DavidSPuentesc/SmartSense-Monitoring/tesis/capitulos/07-desarrollo-implementacion.tex

\chapter{Desarrollo e implementación}
\label{cap:implementacion}

\section{Arquitectura y responsabilidades}
La implementación distribuye la adquisición entre \NumeroNodos{} nodos y concentra recepción, persistencia y consulta en un gateway. La cadena funcional es PT100 $\rightarrow$ MAX31865 $\rightarrow$ ESP32-C6 $\rightarrow$ E220 $\rightarrow$ gateway $\rightarrow$ microSD/LittleFS $\rightarrow$ pantalla/dashboard. El gateway también actualiza la lectura reciente de la interfaz al recibir datos: la pantalla no necesita volver a leer el histórico para cada actualización. La figura~\ref{fig:impl-arquitectura} muestra la separación entre adquisición, enlace radio y acceso local.

\begin{figure}[htbp]
\centering

\caption[Arquitectura de adquisición y consulta local.]{Arquitectura de adquisición y consulta local. Los tres nodos comparten el gateway, que identifica las tramas, conserva series por sensor y presenta lecturas por pantalla y Wi-Fi. Fuente: diseño del proyecto.}
\label{fig:impl-arquitectura}
\end{figure}

El enlace entre nodos y gateway es LoRa punto a punto con mensajes propios, no una red LoRaWAN. El Wi-Fi conecta el navegador con el gateway y nada más. Así se consultan los datos sin Internet, mientras el gateway tenga alimentación, almacenamiento y hora válida.

\section{Construcción del nodo sensor}
\label{sec:impl-nodo}
Cada nodo combina una placa XIAO ESP32-C6, una PT100 magnética de tres hilos, el MAX31865, un E220 y una batería LiPo. La conexión RTD se configura como \texttt{MAX31865\_3WIRE}; el firmware define $R_{\mathrm{nominal}}=\SI{100}{\ohm}$ y $R_{\mathrm{ref}}=\SI{421.1}{\ohm}$. Este último es el valor caracterizado del módulo que usa la conversión (sección~\ref{sec:fund-calculos}).

El MAX31865 se conecta por SPI implementado en software; la alimentación del acondicionador se conmuta desde un pin para reducir su actividad entre lecturas. El E220 se conecta por UART y dispone de líneas de selección de modo. La figura~\ref{fig:impl-esquematico-nodo} documenta las conexiones y la figura~\ref{fig:impl-nodo-montado} muestra el montaje físico. El radio es un E220-400T22D. La sonda es una PT100 magnética de tres hilos marca ZUIDID (artículo 1005008619909588 de AliExpress): elemento de película delgada en una sonda de 19$\times$9.5~mm con tubo protector y funda de resorte, encapsulada en resina epoxi con silicona térmica, cable estándar de $-60$ a \SI{200}{\celsius} y terminal en U de tres hilos \citep{pt100aliexpress}. El vendedor no indica la clase de tolerancia (sección~\ref{sec:marco-rtd}).

\begin{figure}[htbp]
\centering

\caption[Conexiones eléctricas del nodo sensor.]{Conexiones del nodo: SPI hacia el MAX31865, UART y líneas de modo hacia el E220, alimentación y divisor de batería. Los rótulos identifican el tipo de componente, no la referencia comercial exacta de la sonda ni del radio. Fuente: esquema del proyecto.}
\label{fig:impl-esquematico-nodo}
\end{figure}

\begin{figure}[htbp]
\centering

\caption[Nodo ensamblado e instalado sobre un equipo.]{Nodo ensamblado e instalado sobre un equipo de la planta piloto. Fuente: registro fotográfico del proyecto.}
\label{fig:impl-nodo-montado}
\end{figure}

\begin{figure}[htbp]
\centering
\begin{minipage}[t]{0.31\textwidth}\centering

\end{minipage}\hfill
\begin{minipage}[t]{0.31\textwidth}\centering

\end{minipage}\hfill
\begin{minipage}[t]{0.31\textwidth}\centering

\end{minipage}
\caption[Carcasas finales del nodo y del gateway.]{Carcasas finales impresas en PLA. Izquierda: nodo cilíndrico con la antena SMA. Centro: tapa del nodo con el conector USB-C de carga y la antena. Derecha: gateway con la ventana de la pantalla táctil, la antena y la marca del nodo asociado. Los archivos STL y 3MF están en \texttt{hardware/carcasa/}. Fuente: registro fotográfico del proyecto.}
\label{fig:impl-carcasas-finales}
\end{figure}

\begin{figure}[htbp]
\centering
\begin{minipage}[t]{0.34\textwidth}\centering

\end{minipage}\hfill
\begin{minipage}[t]{0.62\textwidth}\centering

\end{minipage}
\caption[Nodo A instalado sobre el motor del succionador.]{Izquierda: ventilador de succión de la máquina Twin con su motor y el nodo A instalado sobre la carcasa. Derecha: detalle del nodo con la carcasa final sobre el motor, fijado por el imán de la sonda. Fuente: registro fotográfico del proyecto.}
\label{fig:impl-instalacion-final}
\end{figure}

\subsection{Ciclo de adquisición y control de fallas}
El archivo \texttt{Nodo\_Lora.ino} de la versión con LoRa y página local inicia interfaces, carga configuración persistida, alimenta el acondicionador y revisa su registro de fallas. En condiciones normales intenta cuatro conversiones, descarta valores no numéricos y valores fuera de los límites programados, y promedia las lecturas aceptadas. El registro de fallas del MAX31865 permite identificar problemas eléctricos \citep{max31865}; los límites de software son filtros, no el rango de la sonda.

Si todas las conversiones fallan se intenta una lectura adicional y, si tampoco sirve, el firmware devuelve 0.0. Como es un número finito, puede llegar al histórico; por eso hay que revisar los valores anómalos de cada serie, y un indicador explícito de validez en la trama es una mejora pendiente.

Tras medir temperatura y batería, el nodo forma y transmite la trama, atiende brevemente mensajes y programa el temporizador de sueño profundo. El parámetro de sueño se guarda con \texttt{Preferences} entre 5 y 7200~s; el código trae 60~s por defecto y el piloto operó con los \PeriodoNominal{} guardados en configuración. Durante los 30 primeros ciclos tras energizar el nodo, el firmware solicita configuración remota en cada ciclo; después no escucha mientras duerme.

\subsection{Lectura de batería}
El ADC lee un divisor resistivo. En la versión revisada se definen $R_1=344\,800~\Omega$, $R_2=994\,300~\Omega$, ganancia $K=1$ y corrección $B=\SI{0.090}{\volt}$. La operación programada es
\begin{equation}
V_{\mathrm{bat}}=K V_{\mathrm{ADC}}\frac{R_1+R_2}{R_2}+B.
\label{eq:impl-bateria}
\end{equation}
La tensión se convierte en un porcentaje lineal entre 3.30 y \SI{4.10}{\volt}, saturado entre 0 y 100, como indicador para la interfaz; no es una medición de carga remanente ni la curva OCV--SoC de la sección~\ref{sec:metodo-autonomia}. El dimensionamiento del divisor y el error del ADC están en la sección~\ref{sec:fund-calculos}.

\section{Comunicación y formato de mensajes}
\label{sec:impl-comunicacion}
El módulo de radio es un Ebyte E220-400T22D, basado en el LLCC68, cuya banda va de 410.125 a 493.125~MHz en pasos de 1~MHz; el canal 23 usado por nodos y gateway corresponde a 433.125~MHz, la frecuencia de fábrica \citep{e220manual}. El firmware incluye una rutina de configuración que escribe por comandos AT la dirección, el canal 23, UART a 9600~bit/s 8N1, tasa aérea de 2.4~kbit/s, modo fijo, paquetes de 200 bytes y el código de potencia 0, que en este módulo equivale a 22~dBm, su valor máximo y de fábrica. La rutina está deshabilitada en el arranque normal, de modo que el radio trabaja con los parámetros que tiene guardados; al reproducir el sistema conviene leerlos desde el módulo. La dirección de destino del maestro es 1.

Para transmitir en modo fijo, el nodo antepone los bytes alto y bajo de la dirección del gateway y el canal al mensaje textual terminado en salto de línea. La dirección radio encamina la trama; la MAC identifica de forma persistente el sensor para el almacenamiento y la interfaz. La tabla~\ref{tab:impl-identidad-nodos} fija la correspondencia que usan los scripts del piloto; la dirección 13 del código es la del ejemplo, no la de los tres dispositivos.

\begin{table}[htbp]
\centering
\caption{Identificadores de los nodos en los scripts de análisis.}
\label{tab:impl-identidad-nodos}
\begin{tabular}{ll}
\toprule
\textbf{Nombre en el análisis} & \textbf{MAC} \\
\midrule
Nodo A & \texttt{58:E6:C5:13:A3:C0} \\
Nodo B & \texttt{58:E6:C5:13:A9:20} \\
Nodo C & \texttt{58:E6:C5:19:28:20} \\
\bottomrule
\end{tabular}
\end{table}

La trama histórica contiene tipo \texttt{DATA}, \texttt{ID}, \texttt{TEMP}, \texttt{BAT} y \texttt{MAC}. La instrumentación posterior amplía el formato con los campos de la tabla~\ref{tab:impl-campos}. En el firmware se construye como la siguiente secuencia de claves, con valores separados por comas:
\begin{quote}\small\ttfamily
DATA,ID=...,SEQ=...,TEMP=...,VBAT=...,\\
BAT=...,UP=...,MAC=...
\end{quote}

\begin{table}[htbp]
\centering\small
\caption{Campos de aplicación y significado en la versión instrumentada.}
\label{tab:impl-campos}
\begin{tabularx}{\textwidth}{@{}p{1.7cm}X>{\raggedright\arraybackslash}p{4.5cm}@{}}
\toprule
\textbf{Campo} & \textbf{Contenido} & \textbf{Alcance} \\
\midrule
\texttt{ID} & Dirección lógica del nodo. & No reemplaza la MAC del archivo. \\
\texttt{TEMP} & Temperatura calculada en el nodo, en \textdegree C. & El gateway puede aplicar offset. \\
\texttt{BAT} & Porcentaje aproximado por tensión. & Indicador, no capacidad medida. \\
\texttt{MAC} & Identificación persistente del dispositivo. & Clave para asociar serie y configuración. \\
\texttt{SEQ} & Contador incrementado en cada envío. & Añadido después del histórico; retenido en sueño profundo. \\
\texttt{VBAT} & Tensión calculada por ADC y divisor. & Añadida para ensayos instrumentados. \\
\texttt{UP} & Milisegundos encendido hasta construir la trama. & No mide recepción ni latencia de red. \\
\bottomrule
\end{tabularx}
\end{table}

El intercambio de configuración utiliza \texttt{CFG\_REQ}, \texttt{CFG} y \texttt{CFG\_ACK}; también existen mensajes de consulta y estado. Estos mensajes no deben contarse como muestras térmicas. El contador \texttt{SEQ} se incrementa para \texttt{DATA}, sobrevive al sueño profundo y puede reiniciarse por corte de alimentación. El gateway cuenta recepciones entre secuencias observadas, pero no elimina duplicados ni detecta todos los reinicios; una prueba directa de PDR debe tratar esos casos (sección~\ref{sec:metodo-60min}).

La instrumentación de RSSI habilita el byte adicional del E220 y registra un indicador de ausencia cuando no está disponible; el protocolo pide comprobarla con el módulo instalado y permite desactivarla si interfiere con la recepción. El RSSI existe desde el ensayo de alcance; el histórico de planta no lo tiene.

\section{Gateway, reloj y persistencia}
El gateway utiliza ESP32-C6, radio E220, pantalla táctil con controlador ST7789 y microSD. Las conexiones añadidas se presentan en la figura~\ref{fig:impl-esquematico-gateway}. Al recibir una trama, el programa identifica la MAC, actualiza su última recepción, separa temperatura cruda de corregida y actualiza el estado mostrado. La lógica de alarma se ejecuta con la temperatura del nodo disponible en el gateway.

\begin{figure}[htbp]
\centering

\caption[Conexiones externas del gateway.]{Conexiones externas del gateway con el radio UART y la salida de alarma crítica. La pantalla, el panel táctil y la ranura microSD forman parte de la placa; el esquema permite distinguir sus funciones de las conexiones agregadas. No certifica una función de seguridad de máquina. Fuente: esquema del proyecto.}
\label{fig:impl-esquematico-gateway}
\end{figure}

La hora se sincroniza desde el navegador con la zona UTC$-$5, y con ella se nombran los archivos y se ubican las muestras en el día. Mientras el reloj no sea válido la rutina de guardado no escribe, así que una lectura visible en pantalla no garantiza que se haya guardado; verificar hora y escritura es parte de la puesta en marcha.

\subsection{Archivos diarios y ventana móvil}
\label{sec:impl-almacenamiento}
El gateway guarda en la microSD cuando está montada y en LittleFS si no; LittleFS aloja además los recursos web y la configuración. Es un medio alternativo, no una réplica ni una migración automática, y un fallo al abrir un archivo en una tarjeta montada no conmuta a LittleFS.

Por cada MAC hay un directorio y por cada fecha un archivo de texto cuyas líneas guardan el segundo del día y la temperatura multiplicada por diez como entero, con una resolución de representación de \SI{0.1}{\celsius}. Se guarda la temperatura corregida y se evita escribir dos veces el mismo segundo del mismo sensor. Secuencia, batería y RSSI no van en esas líneas; se capturan aparte por la salida serie.

La constante \texttt{MAX\_DAYS\_HISTORY} vale 30. La limpieza ordena los archivos diarios por fecha y elimina los más antiguos cuando existen más de 30. En operación diaria esto produce una ventana móvil de 30 días; si hay días sin archivo, la implementación conserva hasta 30 fechas con datos, no necesariamente 30 días calendario consecutivos.

El conjunto analizado se exportó antes de que la rotación eliminara sus fechas; por eso los \DuracionComunDias{} días de estudio superan las 30 fechas que el gateway retiene. La exportación directa desde la web no se verificó; para repetir el piloto hay que programar la extracción antes de la rotación y conservar la copia fuera del dispositivo.

\section{Pantalla local y dashboard}
El gateway publica el punto de acceso \texttt{Sensores\_Temp} y la página local en \texttt{192.168.4.1}. El navegador recibe actualizaciones por eventos del servidor cada segundo, que muestran la última lectura de cada nodo y su estado de conexión; la adquisición sigue siendo cada 120~s.

Las funciones implementadas incluyen temperatura y batería recientes, consulta por fecha, gráfica de 24~horas, mínimo, máximo y promedio, agrupación por máquina y comparación entre sensores. También permiten asignar nombres, configurar el periodo, ajustar la compensación y fijar umbrales. La figura~\ref{fig:impl-dashboard} ilustra estas funciones con nueve registros de interfaz; el análisis experimental corresponde a los \NumeroNodos{} nodos del piloto.

\begin{figure}[htbp]
\centering

\caption[Dashboard local y organización de registros por máquina.]{Dashboard con agrupación por máquina, lectura reciente, batería, conectividad y tendencia. La captura muestra la organización de nueve registros de interfaz; el análisis experimental de este trabajo corresponde a tres nodos. Fuente: captura del proyecto.}
\label{fig:impl-dashboard}
\end{figure}

\subsection{Compensación progresiva de temperatura}
El gateway permite ajustar un offset por sensor a partir de una referencia fría y un punto caliente. Para temperatura cruda $T_r$, base fría $T_f$, punto caliente $T_c$ y offset $O$, el comportamiento nominal dentro de una configuración válida se expresa como
\begin{equation}
T_{\mathrm{corr}}=T_r+O\,\min\!\left(1,\max\!\left(0,\frac{T_r-T_f}{T_c-T_f}\right)\right),
\qquad T_c>T_f.
\label{eq:impl-offset}
\end{equation}
Por debajo de $T_f$ no se aplica el ajuste y por encima de $T_c$ se aplica completo; si faltan referencias válidas o la separación es insuficiente, el offset se suma completo. Conviene conservar los parámetros usados, porque un cambio de offset produce saltos en el registro que no vienen de la máquina. Es un ajuste operativo, no una calibración \citep{jcgm2012}.

\subsection{Alarmas y alcance de la supervisión}
Los umbrales por nodo distinguen advertencia y condición crítica; la interfaz los señala visualmente y con sonido en el navegador, y el gateway tiene además una salida digital de alarma crítica. Llaman la atención sobre una condición térmica configurada; no diagnostican la causa ni son un sistema de parada de seguridad. Sus valores por defecto están en la sección~\ref{sec:fund-calculos}.

\section{Relación entre implementación y evidencia}
La implementación permite adquirir y conservar las series; qué puede afirmarse con ellas lo fijan los procedimientos del capítulo~\ref{cap:metodologia}. Hay que distinguir el firmware revisado, la configuración desplegada y los registros de cada ensayo: la instrumentación añadida después no completa el histórico, y los cálculos de autonomía no sustituyen una descarga hasta el corte.
