DavidSPuentesc/SmartSense-Monitoring/tesis/capitulos/02-planteamiento-problema.tex

\chapter{Planteamiento del problema}
\label{cap:problema}

\section{Necesidad identificada}
En la planta piloto, la temperatura de los equipos se revisaba con inspecciones puntuales: cada lectura decía cómo estaba el equipo en ese momento y nada más. Como las lecturas no se guardaban con una identificación y una hora comunes, lo que pasaba entre una visita y la siguiente quedaba sin documentar. El problema que aborda este trabajo es esa falta de un historial térmico continuo y accesible con el que comparar jornadas, puntos de medición y transitorios de la operación.

Resolverlo exige cuatro funciones encadenadas: adquirir la temperatura superficial, transmitirla desde el equipo, almacenarla por sensor y fecha, y presentarla para consulta. Si una falla, la lectura puede ser correcta y aun así no estar disponible después. A eso se suman las restricciones de la instalación: puntos distribuidos, poco cableado de comunicación, nodos a batería y consulta local, que obligan a equilibrar frecuencia de adquisición, consumo y continuidad del registro, como en cualquier red de sensores diseñada para una aplicación concreta \citep{yick2008}.

Existen soluciones comerciales de monitoreo de condición; el WISE-2410, por ejemplo, integra temperatura y vibración sobre LoRaWAN \citep{wise2410}. La pregunta de ingeniería que motiva SmartSense es otra: cómo construir una plataforma modificable que integre una sonda externa de superficie y un historial ajustado a las consultas que necesita esta planta. Ser abierta no la hace mejor por sí sola, y no todos los sistemas comerciales dependen de la nube; la comparación por características está en el capítulo~\ref{cap:estado-arte}.

\section{Pregunta de investigación}
\begin{quote}
¿Es viable diseñar e implementar una red inalámbrica, abierta y de operación local que adquiera, transmita, almacene y visualice la temperatura superficial de equipos industriales, conservando un historial útil para analizar su comportamiento térmico?
\end{quote}

Viabilidad significa aquí que la cadena completa funciona y que su comportamiento en el piloto queda caracterizado: recepción de muestras identificadas, consulta del histórico, comparación térmica de campo y evaluación del enlace y de la energía. La respuesta distingue lo observado directamente de lo inferido o estimado.

\section{Justificación y alcance}
Técnicamente, el proyecto se justifica porque conserva información que una inspección aislada no da: el historial permite revisar un episodio térmico y orientar nuevas inspecciones. Académicamente, porque documenta la relación entre requisitos, decisiones de integración y evidencia experimental, de modo que otro desarrollador pueda revisar y adaptar la solución. Abierto se refiere a los archivos de diseño, el firmware y el software, publicados con sus licencias; los módulos comerciales que se usan siguen siendo cerrados.

El alcance comprende \NumeroNodos{} nodos, un gateway, adquisición por contacto, almacenamiento local, visualización histórica y alarmas por umbrales configurables. La evaluación en planta cubre \DuracionComunDias{} días para los nodos A y C y una ventana más larga para el nodo B; las comparaciones entre nodos usan el tramo en que coinciden. Lo que se mide es la temperatura del punto de la superficie donde va la sonda, no la temperatura interna del motor ni la de toda la carcasa.

Quedan fuera del alcance la calibración trazable, la descarga completa de la batería, el comportamiento de una red más grande y la relación causal entre temperatura y daño de rodamientos. Siguiendo la distinción entre adquisición, diagnóstico y pronóstico \citep{jardine2006,cinar2020}, el sistema aporta los datos para el monitoreo de condición; los algoritmos de mantenimiento predictivo no forman parte del trabajo.
