DavidSPuentesc/SmartSense-Monitoring/tesis/preliminares/portada.tex

\begin{titlepage}
\begin{center}
\vspace*{2cm}
{\Large\bfseries SMARTSENSE MONITORING: SISTEMA INALÁMBRICO PARA EL MONITOREO Y ANÁLISIS HISTÓRICO DE TEMPERATURA EN EQUIPOS INDUSTRIALES\par}
\vfill
{\large Jesus Andre Bojaca Lopez\par}
\vspace{0.4cm}
{\large David Santiago Puentes Cárdenas\par}
\vfill
{\large Universidad ECCI\par}
{\large Facultad de Ingenierías\par}
{\large Programa de Ingeniería Electrónica\par}
{\large Bogotá D. C.\par}
{\large 2026\par}
\end{center}
\end{titlepage}

\begin{titlepage}
\begin{center}
\vspace*{1.6cm}
{\Large\bfseries SMARTSENSE MONITORING: SISTEMA INALÁMBRICO PARA EL MONITOREO Y ANÁLISIS HISTÓRICO DE TEMPERATURA EN EQUIPOS INDUSTRIALES\par}
\vfill
{\large Jesus Andre Bojaca Lopez\par}
\vspace{0.4cm}
{\large David Santiago Puentes Cárdenas\par}
\vfill
{\large Trabajo de grado presentado como requisito para optar al título de Ingeniero Electrónico\par}
\vfill
{\large Tutores:\par}
{\large Jhon Edwin Vera\par}
{\large Sergio Francisco Mora Martínez\par}
\vfill
{\large Universidad ECCI\par}
{\large Facultad de Ingenierías\par}
{\large Programa de Ingeniería Electrónica\par}
{\large Bogotá D. C.\par}
{\large 2026\par}
\end{center}
\end{titlepage}
