DavidSPuentesc/SmartSense-Monitoring/hardwarex/SmartSense_HardwareX.pdf

Article title
SmartSense Monitoring: an open-source wireless PT100 node and gateway for surface-temperature monitoring of industrial equipment

Authors
Jesus Andre Bojaca Lopez, David Santiago Puentes Cardenas*, Jhon Edwin Vera, Sergio Francisco Mora Martinez

Affiliations
Electronic Engineering Program, Faculty of Engineering, Universidad ECCI, Bogota D.C., Colombia

Corresponding author’s email address and Twitter handle davids.puentesc@ecci.edu.co

Abstract
SmartSense Monitoring is an open-source wireless PT100 node and gateway for industrial surface-temperature monitoring. Each battery-powered node combines a XIAO ESP32-C6, a three-wire PT100 probe, a
MAX31865 front-end and an Ebyte E220 LoRa radio at 433 MHz. The gateway stores a rolling 30-day history locally and serves a Wi-Fi dashboard without a cloud service. A three-node evaluation includes a 32-day pilot deployment and an extended Node B record, totalling 51,338 samples across the individual recording windows. Raw availability was 76.0%, 32.3% and 75.1%; link availability conditioned on inferred gateway-active periods was 97.8–98.4%. Arrival intervals support an inferred PDR of 95.3–96.6%. Six time-stamped paired readings against an infrared thermometer, taken with the surface stable, differ by 0.15 ◦C on average and 0.23 ◦C at most after offset adjustment, without establishing absolute accuracy. A five-day partial discharge supports estimated autonomy of 177 days by linear extrapolation and 291–307 days using a LiPo-curve model, not demonstrated service lifetime. A temperature rise was later associated with a bearing anomaly during inspection, supporting condition monitoring without validated diagnosis or prediction. Hardware, firmware, software and analysis artifacts are versioned in a public repository; absent primary CSV files and incomplete component identification limit full replication of the evaluation.

Keywords
Open-source hardware; LoRa; PT100; RTD; MAX31865; ESP32-C6; industrial temperature monitoring; condition monitoring

Specifications table

Hardware name | SmartSense Monitoring
Subject area | • Engineering and material science • Educational tools and open source alternatives to existing infrastructure
Hardware type | • Measuring physical properties and in-lab sensors • Field measurements and sensors • Electrical engineering and computer science
Closest commercial analog | Industrial wireless RTD/condition-monitoring loggers such as the Advantech WISE-2410 and commercial PT100 wireless data loggers.
Open source license | Hardware: CERN-OHL-S v2. Firmware and software: MIT License. Documentation: CC-BY 4.0.
Cost of hardware | Itemized total: 627,000 COP (≈157 USD at the project conversion assumption of 4,000 COP/USD). Node-specific parts: 149,000 COP (≈37 USD), before shared wiring; see Bill of materials.
Source file repository | SmartSense-Monitoring on GitHub; (https://github.com/DavidSPuentesc/SmartSense-Monitoring) archived on Zenodo, DOI 10.5281/zenodo.22903028 (https://doi.org/10.5281/zenodo.22903028) (concept DOI resolving to the latest version; release v1.0-tesis: 10.5281/zenodo.22903029).

### 1. Hardware in context

Continuous temperature monitoring of motors and other industrial equipment helps identify conditions associated with friction, overload, poor ventilation or mechanical degradation. In a manual inspection, an operator obtains only the value at the instant of measurement; if that value is not systematically recorded, the thermal evolution of the equipment cannot be reconstructed or related to its operating and stop cycles.

Wireless sensor networks distribute measurement points without installing communication cabling at each location [1,2,6]. For low-data-rate applications, LoRa provides a long-range, low-power alternative suited to battery-powered nodes, whose range and scalability have been characterised experimentally [3,7,8]. Relevant precedents include LoRaWAN temperature monitoring with a local-server option [9], an open condition-monitoring sensor with vibration and acoustic measurements [10], and the local SD-based HIGROTERM logger [12]. SmartSense contributes the integration of an external three-wire PT100 and MAX31865, point-to-point radio, battery operation and a gateway-hosted daily history and dashboard. Its contribution is this documented platform and pilot evaluation, rather than invention of its constituent technologies or superiority over all existing systems. It supports condition-based maintenance [4,11] but does not implement or validate a predictive-maintenance algorithm.

A PT100 RTD was selected for its established industrial use, three-wire lead compensation with the MAX31865 and availability in a magnetic surface probe suitable for motor housings. The installed probe is a ZUIDID magnetic three-wire PT100 (AliExpress item 1005008619909588): a thin-film element in a 19 × 9.5 mm probe with a protective tube and spring sheath, epoxy-encapsulated with thermally conductive silicone, a standard cable rated −60 to 200 ◦C and a three-wire U-terminal [14]. The seller does not state the tolerance class, and the −60 to 200 ◦C figure is the cable rating, so the generic RTD conversion range cannot be assigned to the complete installed probe. The field comparison below characterises agreement in a narrow temperature interval, not the full measurement range or inter-node repeatability.

Compared with proprietary industrial loggers such as the Advantech WISE-2410, SmartSense Monitoring trades integrated vibration sensing for full openness and local-first operation. Table 1 contrasts both systems by capability rather than price alone, making it suitable for pilot plants and educational settings where flexibility and reproducibility matter more than a turnkey platform.

### 2. Hardware description

SmartSense Monitoring consists of one or more battery-powered sensor nodes and a gateway/visualizer. Each node acquires the surface temperature of a machine with a magnetic PT100 probe and a MAX31865 RTD front-end, estimates its battery state, and transmits the reading over a 433 MHz LoRa link before entering deep sleep. The gateway receives the frames, identifies each node by its MAC address, applies a configurable offset, stores the samples locally and presents them on an integrated touch display and a Wi-Fi web dashboard.

The documented radio configuration uses 9600 bit/s UART (8N1), 2.4 kbit/s air rate, channel 23 in the stated 433 MHz band and fixed addressing. The radio is an Ebyte E220-400T22D (Semtech LLCC68, 410.125– 493.125 MHz), so channel 23 corresponds to 433.125 MHz, its factory frequency. The transmit power is 22 dBm, the module’s maximum and factory default, which is also the value (power code 0) written by the firmware’s one-time configuration routine; the datasheet gives a typical receiver sensitivity of −127 dBm at 2.4 kbit/s [13]. A 120 s nominal cycle provides 720 expected samples per node per day, balancing thermal-history resolution with traffic, storage and battery demand for this pilot.

- It provides automatic periodic surface-temperature logging using commercially available modules and an itemized bill of materials.

Feature | SmartSense | WISE-2410 | Advantage
Open hardware | Project schematics and enclosure files, CERN-OHL-S v2 | Commercial design; no open hardware release identified | SmartSense
External PT100 | Yes, three-wire surface probe | Integrated temperature sensor; no external PT100 specified | SmartSense
Communication | LoRa 433 MHz (point-to-point) | LoRaWAN | Different
Vibration sensing | No | Yes | WISE-2410
Local history | microSD or LittleFS; rolling 30-day store | Depends on gateway/application integration | SmartSense
Cloud dependency | None for local dashboard | LoRaWAN gateway/server required; cloud is not inherently mandatory | SmartSense
IP rating | Not demonstrated | IP66 specified | WISE-2410
Autonomy evidence | Estimated from 5-day partial discharge: 177 or 291–307 days; 1000 mAh, 120 s cycle | Up to 2 years specified; hourly updates [5] | WISE-2410 (specified); SmartSense pending
Software openness | MIT node/gateway firmware and software | WISE Studio utility; open firmware not identified | SmartSense
Cost basis | 149,000 COP per node in listed parts (≈37 USD); excludes shared wiring | No comparable dated quotation available | Not comparable

Table 1: Functional comparison with Advantech WISE-2410 [5]. WISE-2410 retains advantages in vibration, IP66 protection and specified lifetime. Autonomy uses different update intervals and evidence types; no controlled superiority claim follows. SmartSense cost uses the project BOM and a 4,000 COP/USD conversion assumption.

- It operates fully offline: the gateway serves its own dashboard over a local Wi-Fi access point, so no cloud account or Internet connection is required.
- It preserves a per-sensor daily history, enabling the study of thermal trends, transients and machine on/off cycles that a spot measurement cannot capture.
- It is a modular basis for further work: additional nodes, alternative RTD probes, or extra variables (e.g. current, vibration) can be integrated by reusing the node design.
- Published project schematics and source code support teaching wireless sensor networks, RTD acquisition and local data handling; the purchased modules retain their manufacturer-specific internals.

Design files

The complete repository, with the editable KiCad schematics, node and gateway firmware, software, BOM, enclosure files, analysis scripts, figures, licenses and the manuscript sources, is released as version v1.0-tesis on GitHub (DavidSPuentesc/SmartSense-Monitoring) (https://github.com/DavidSPuentesc/SmartSense-Monitoring) and archived on Zenodo under the concept DOI 10.5281/zenodo.22903028, (https://doi.org/10.5281/zenodo.22903028) which resolves to the latest version (this release: 10.5281/zenodo.22903029).

The primary historical and range-test CSV files read by the scripts are not included in the archived version; their publication depends on the partner company's authorization. The tolerance class of the PT100 probe is not stated by its seller. The repository therefore supports inspection and reconstruction of the documented design, but not yet exact replication of every reported experiment.

### 3. Design files summary

Design filename | File type | Open source license | Location of the file
Node schematic (nodo sensor) | KiCad schematic + PDF/SVG | CERN-OHL-S v2 | hardware/kicad/ in identified snapshot
Gateway schematic (gateway) | KiCad schematic + PDF/SVG | CERN-OHL-S v2 | hardware/kicad/ in identified snapshot
smartsense.kicad sym | KiCad symbol library | CERN-OHL-S v2 | hardware/kicad/
Node firmware (Nodo Lora) | Arduino C++ (.ino) | MIT | Firmware directory specified below
Gateway firmware (maestro Lora pantalla) | Arduino C++ (.ino) + web assets | MIT | Firmware directory specified below
Bill of materials (BOM.csv) | CSV spreadsheet | CERN-OHL-S v2 | hardware/BOM.csv
Enclosure (node, gateway, lids) | STL + zipped 3MF | CERN-OHL-S v2 | hardware/carcasa/

The schematics document SPI, UART, switched sensor power and the battery divider. Both firmware folders are under sensores espnow lora/version con lora y pagina local/; they contain acquisition, reception, storage and dashboard logic. The BOM and existing PLA enclosure STL/3MF files are in the paths above. These project files do not replace missing probe specifications or a frozen record of the pilot configuration.

Bill of materials

Costs reproduce the project BOM, reviewed on 15 September 2026, in Colombian pesos (COP). USD equivalents use the project’s approximate conversion assumption of 1 USD = 4,000 COP, not a verified dated exchangerate quotation. Supplier invoices and purchase dates are not included. The table covers three nodes and one gateway; prices are historical project entries rather than current market quotations.

### 4. Bill of materials summary

ID | Component | Qty. | Unit cost (COP) | Total (COP) | Source | Material
U1 | Seeed Studio XIAO ESP32-C6 (node) | 3 | 30,000 | 90,000 | Seeed Studio (https://www.seeedstudio.com/) | Semiconductor
U2 | ESP32-C6 Touch LCD 1.47 board (gateway) | 1 | 90,000 | 90,000 | Local distributor | Semiconductor
U3 | Ebyte E220-400T22D LoRa module (LLCC68, 22 dBm) + antenna | 4 | 30,000 | 120,000 | Ebyte (https://www.cdebyte.com/products/E220-400T22D) | Semiconductor
RT1 | ZUIDID magnetic three-wire PT100 probe (thin film; cable rated −60 to 200 ◦C) | 3 | 30,000 | 90,000 | AliExpress (https://www.aliexpress.com/item/1005008619909588.html) [14] | Metal
U4 | MAX31865 RTD front-end module | 3 | 14,000 | 42,000 | Sigma Electr´onica (https://www.sigmaelectronica.net/) | Semiconductor
BT1 | LiPo battery 3.7 V 1000 mAh | 3 | 30,000 | 90,000 | Did´acticas Electr´onicas (https://www.didacticaselectronicas.com/) | Other
U5 | LiPo charge and protection module (TP4056 or equiv.) | 3 | 5,000 | 15,000 | Local distributor | Semiconductor
R1 | Resistor 344.8 kΩ (battery divider) | 3 | – | – | Local distributor | Other
R2 | Resistor 994.3 kΩ (battery divider) | 3 | – | – | Local distributor | Other
MEC1 | 3D-printed PLA enclosure | 4 | 10,000 | 40,000 | Self-printed | Polymer
W1 | Wires, connectors, headers, hardware, adhesives | 1 | 50,000 | 50,000 | Local distributor | Other

Itemized total: 627,000 COP (≈157 USD at the stated conversion). Node-specific parts sum to 149,000 COP per node, including the 1000 mAh cell and enclosure; gateway board, radio and enclosure sum to 130,000 COP. Shared wiring/hardware contributes 50,000 COP, including battery-divider resistors. These entries do not establish a labor, shipping or certification cost.

### 5. Build instructions

The following steps describe the construction of one sensor node and the gateway. Refer to the node and gateway schematics (Design files) and to the Bill of materials for component designators.

Sensor node

1. Use a three-wire magnetic PT100 probe (the pilot used a ZUIDID thin-film probe, AliExpress item 1005008619909588, cable rated −60 to 200 ◦C, tolerance class not stated [14]); record the tolerance class when available before replication. Configure the MAX31865 module in three-wire mode (bridge the 2/3-wire jumper), and connect the PT100 leads: the two leads from the same probe end to F+ and RTD+, and the remaining lead to RTD-, bridged to F-.
2. Wire the MAX31865 SPI bus to the XIAO ESP32-C6: CLK → D6 (GPIO16), SDO→ D5 (GPIO23), SDI →D4 (GPIO22), CS→ D3 (GPIO21). Power the module VIN from D2 (GPIO2) so the firmware can switch it off during deep sleep.
3. Connect the E220 LoRa module by UART: E220 TXD → D7 (GPIO17), RXD→ D8 (GPIO19), M0 → D10 (GPIO18), M1 → D9 (GPIO20); power VCC/GND from 3V3/GND.
4. Build the battery divider: VBAT – R1 (344.8 kΩ) – A0 (GPIO0) – R2 (994.3 kΩ) – GND. Connect the LiPo cell through the TP4056 charge/protection module to the XIAO battery pads.
5. Flash the node firmware (Nodo Lora.ino) with the Arduino IDE and the ESP32 board package. Install the Adafruit MAX31865 library. Set RREF to the measured reference resistance of your MAX31865 module (421.1 Ω in this build).
6. Fit the components in the 3D-printed PLA enclosure and attach the PT100 magnetically to the target surface.

Gateway

1. Connect the E220 module to the ESP32-C6 Touch LCD board: E220 TXD→ GPIO8 (gateway RX), RXD →GPIO7 (gateway TX), and both M0 and M1 to GPIO9; power VCC/GND from 3V3/GND.
2. Optionally wire a critical-alarm output (LED, buzzer or relay driver) to GPIO16.
3. Flash the gateway firmware (maestro Lora pantalla.ino) and upload the web dashboard assets to the on-board storage (LittleFS). Insert a microSD card for the history.

Safety. Use a fused LiPo cell with the TP4056 protection module and observe LiPo handling precautions. Ensure the PT100 and enclosure are rated for the surface temperature of the monitored equipment and mounted so they do not interfere with moving parts.

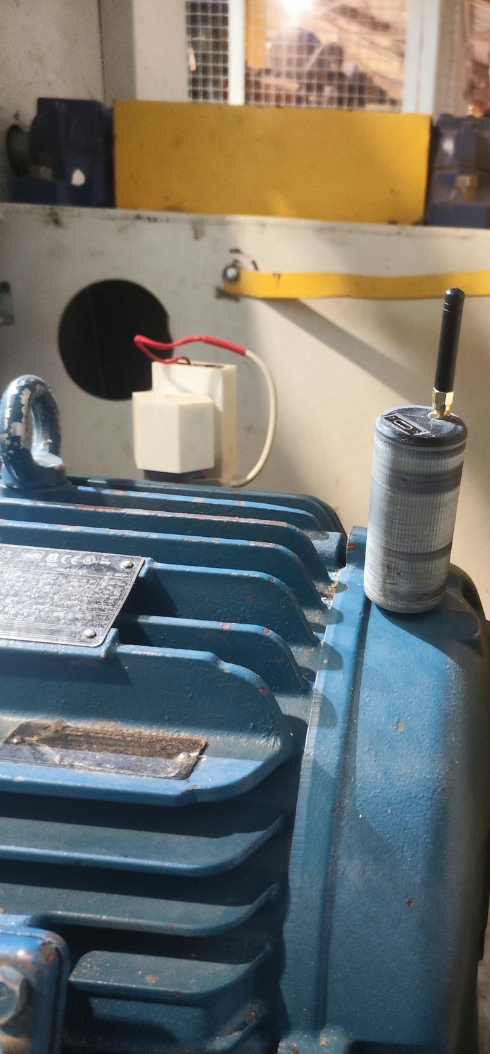
[picture p9: figure]

Figure 1: Assembled sensor node mounted on a motor housing: the PT100 probe with the MAX31865 module (left) and the node enclosure with the LoRa antenna (right).

### 6. Operation instructions

1. Power the gateway. It creates a Wi-Fi access point (Sensores Temp) and serves the dashboard at http://192.168.4.1.
2. Power each node. The reviewed firmware defaults to 60 s of sleep, configurable between 5 and 7200 s; the pilot used 120 s. Activity after waking adds to this sleep duration. Verify the retained setting before replication. The gateway registers each node by its MAC address.
3. In the dashboard, assign names to sensors, group them by machine, set the sampling interval, apply a per-node temperature offset, and configure warning and critical thresholds.

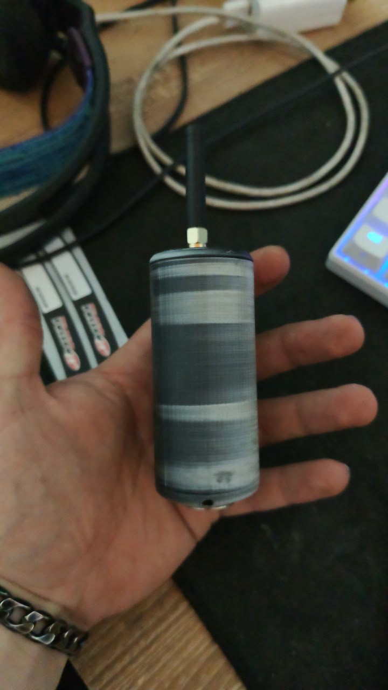
[picture p10: figure]
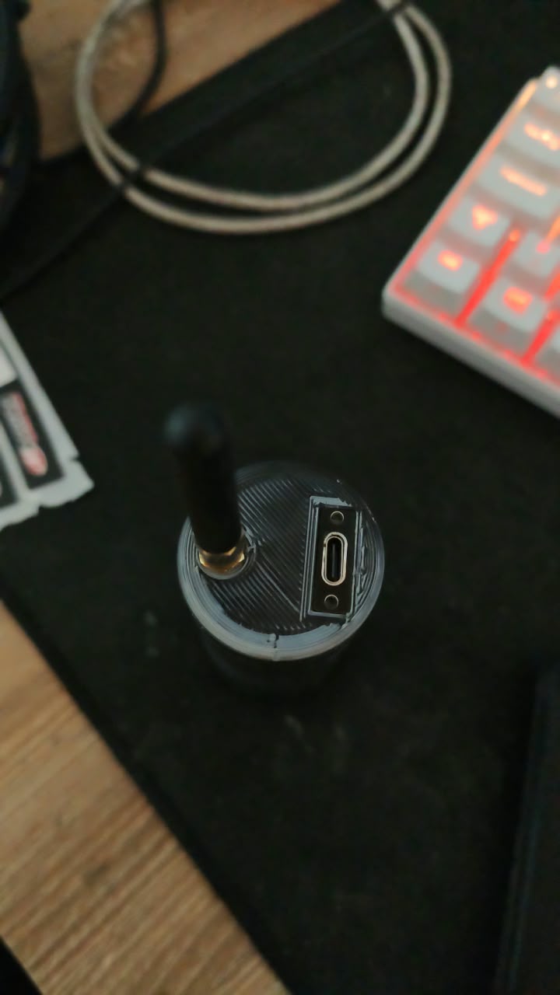
[picture p11: figure]
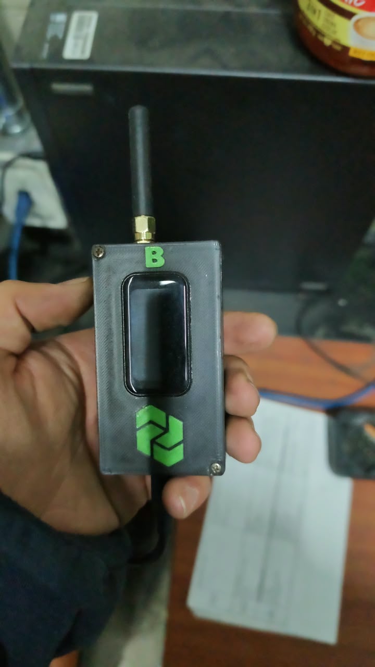
[picture p12: figure]

Figure 2: Final 3D-printed PLA enclosures. Left: cylindrical node enclosure with the SMA antenna. Centre: node lid with the USB-C charging port and antenna. Right: gateway enclosure with the touch-screen window, antenna and the label of its paired node. STL and 3MF files are in hardware/carcasa/.

4. Monitor the live values (temperature, battery, connectivity) and consult the per-day 24-hour history, including minimum, maximum and average, and compare sensors of the same machine.
5. Preserve copies of the per-sensor stored history before the 30-day rotation removes older dates. The project analysed exported CSVs and the software replica can import them; direct web CSV download is not verified in the reviewed gateway firmware and is not claimed as a demonstrated interface function.

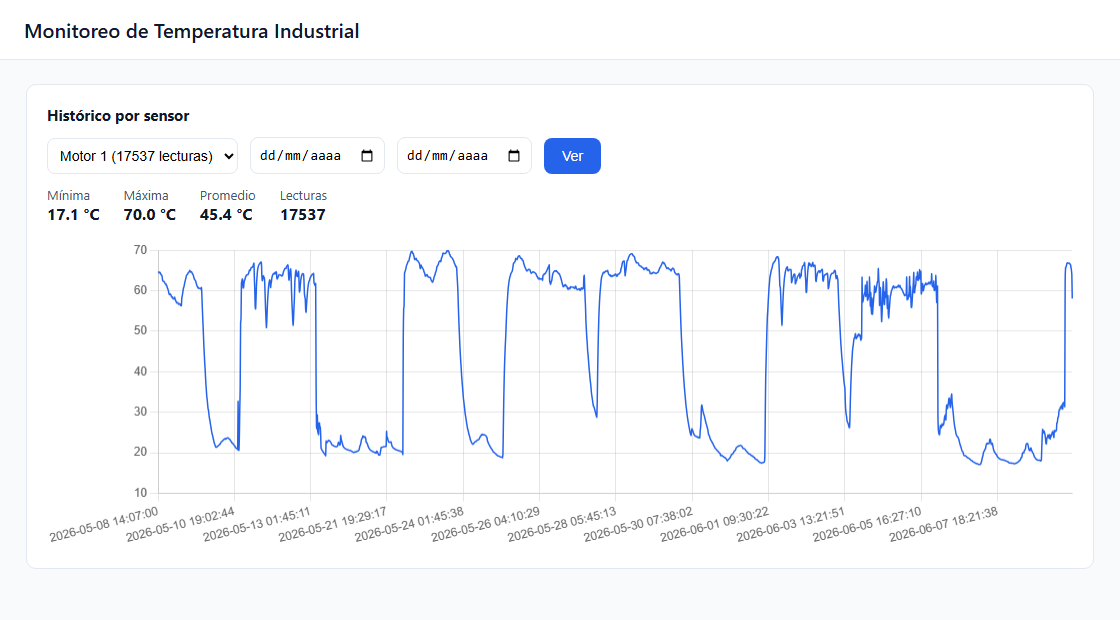
[picture p13: figure]

Figure 3: Local web dashboard: per-sensor temperature history over the deployment, with minimum, maximum and mean statistics. Shown here running on the open-source software replica with generic sensor labels.

Safety. The critical-alarm output is a supervisory aid, not a safety interlock; do not use it as the sole protection for equipment or personnel.

### 7. Validation and characterization

The three-node evaluation includes a 32-day pilot deployment (8 May–9 June 2026 for Nodes A and C), with Node B recorded from 10 May to 20 July 2026. The 51,338 samples are the sum of these individual files, not a count over 32 complete days common to all three nodes. Figures comparing nodes use their overlapping interval. The nominal cycle was 120 s and the documented median inter-arrival interval was 121 s. Separate partial-discharge and radio-range tests were performed in August.

Availability. Table 2 separates raw system-level data availability from link availability conditioned on inferred gateway-active periods. The generator analisis/figuras validacion.py uses 121 s as the expected cadence. Raw availability divides received samples by the expected count across each node’s first-to-last-record span. Conditioned availability removes the entire duration of each inter-arrival gap exceeding 363 s before computing the expected count. Simultaneous gaps in Fig. 9 support a common-cause interpretation, including gateway power interruptions during plant stoppages; they do not independently prove the power state or distinguish reception, clock and storage failures. Thus 97.8–98.4% describes classified active periods, not overall system availability, and the excluded hours cannot all be asserted to be confirmed power-off hours.

Node | Samples | Raw avail. | Conditioned link avail. | Gaps | Hours excluded
Node A | 17,537 | 76.0% | 98.4% | 66 | 176
Node B | 16,487 | 32.3% | 98.3% | 73 | 1154
Node C | 17,314 | 75.1% | 97.8% | 81 | 180

Table 2: Documented availability in the individual recording windows. Node B’s longer file includes a gap of approximately 33 days; its raw availability is not a comparison over the same calendar span as A and C. Gap counts and excluded hours are temporal classifications, not a direct power log.

Reception cadence and inferred packet delivery. Retained short intervals cluster near a 121 s median (Fig. 10). The separate generator analisis/perdida paquetes.py uses a 120 s nominal cycle and excludes intervals longer than 1800 s. For retained gaps it rounds the interval divided by 120 s to k, infers k − 1 missing frames when k ≥ 2, and computes received/(received + inferred missing). The documented inferred PDR is 96.55%, 96.07% and 95.32% for A, B and C, respectively: 95.3–96.6% rounded, with inferred loss of 3.5–4.7%. Each estimate uses its individual node file, including Node B’s extension. These filters and denominators differ from availability; neither metric is a direct sent-versus-received count. Without a historical sequence counter and send log, cadence assumptions cannot distinguish radio loss from absent acquisition or persistence.

Representative 60-minute window. The historical window of 10 May 2026, 00:00–01:00 (Fig. 5), contains 29, 30 and 30 records for A, B and C against 30 nominally expected at a 120 s cycle: received/expected ratios of 96.7%, 100% and 100%. The denominator is a schedule, not an observed transmission count. The script selects a window with at least 25 records per node, so this is a coverage-selected illustration, not an independent test or an unbiased estimate for all hours. RSSI was enabled later for the range test; the interface used did not expose SNR. A sequence counter added after the deployment supports future direct PDR testing but cannot recover historical sends. End-to-end latency and service recovery require synchronized node/gateway measurements.

Range test. On 20 August 2026 a node moved away from the gateway and back in an urban non-line-ofsight path with buildings in between (Fig. 4). Valid packets were received at the farthest observed distance, approximately 688 m, with RSSI near −98 dBm at 20:44–20:54, compared with approximately −15 dBm nearby. The test ended voluntarily with the link still operational: at least 688 m is a demonstrated lower bound in this geometry. Against the E220-400T22D datasheet sensitivity of −127 dBm typical at 2.4 kbit/s (−126 to −129 dBm) [13], the −98 dBm RSSI leaves a margin of about 29 dB; this is a margin to the manufacturer’s figure, not a measured link-failure point. The recorded battery indicator stayed near 94% during 2.6 h; this voltage-derived indication does not measure charge consumption. Motion and changing obstacles prevent a controlled RSSI–distance characterization; fixed positions and repeated trials remain future work.

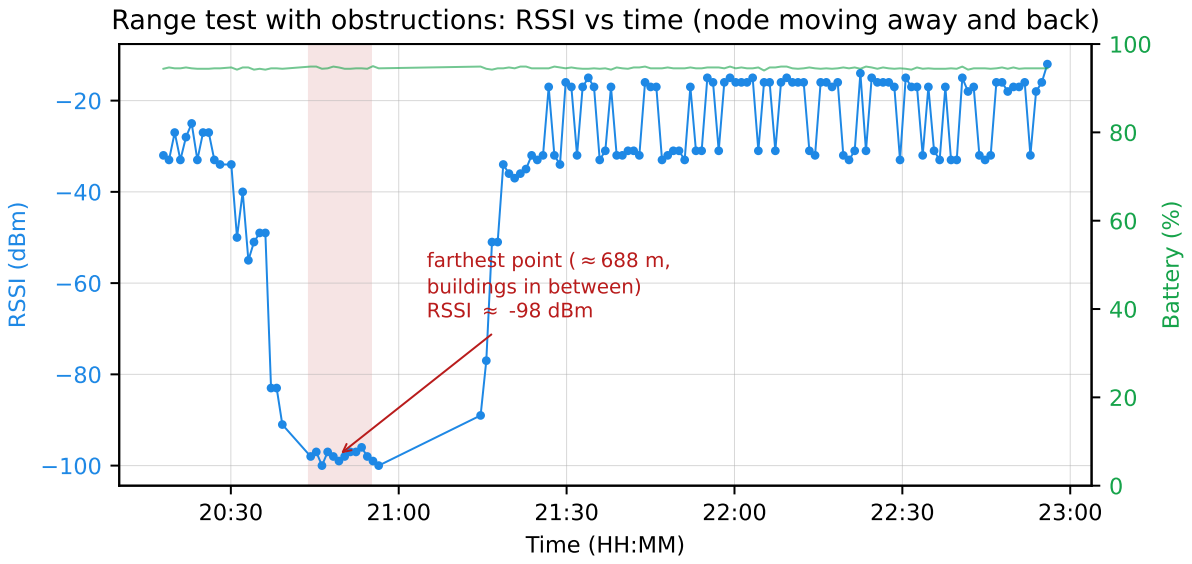
[picture p14: figure]
Time (HH:MM); RSSI (dBm); RSSI ≈ -98 dBm; Battery (%)

farthest point ( ≈ 688 m, buildings in between)

## Range test with obstructions: RSSI vs time (node moving away and back)

Figure 4: Urban obstructed-path test of 20 August 2026: per-packet RSSI (blue) and voltage-derived battery indication (green) against time during a mobile outward and return route. The link remained operational near 688 m at approximately −98 dBm; distance was not a controlled fixed-position sweep.

Temperature field comparison. The purpose was to assess consistency of the installed node with a field reference on the suction-fan motor. Each Fluke 62 MAX reading was photographed next to the probe, and the photo time recorded by the phone locates it in the exported CSV; the node reading at that instant is interpolated between the two surrounding samples (analisis/parejas fluke.py), so every pair can be checked against the record (Table 3). The six pairs taken with the surface stable (changing less than 0.1 ◦C/min), over three visits, give a signed mean difference of −0.07 ◦C, a mean absolute difference of 0.15 ◦C, an RMSE of 0.16 ◦C and a maximum of 0.23 ◦C between 51.6 and 67.6 ◦C. The pair of 10 May was taken while the motor was starting after a stop and the surface rose 0.34 ◦C/min; the housing seen by the Fluke warms ahead of the magnetic probe’s contact point, and its −3.6

◦C difference reflects that thermal lag. With all seven pairs the mean absolute difference is 0.64 ◦C and the RMSE 1.37 ◦C. Earlier field readings from a visit whose record was not exported are not used.

Date and time Fluke (◦C) SmartSense (◦C) ∆T (

◦C) Rate (◦C/min)
10 May 22:54:00 | 37.4 | 33.8 | −3.6 | +0.34
12 May 14:17:15 | 51.7 | 51.6 | −0.1 | −0.08
25 May 17:09:02 | 67.7 | 67.6 | −0.1 | −0.01
25 May 17:15:18 | 67.7 | 67.5 | −0.2 | −0.01
25 May 19:20:49 | 65.3 | 65.2 | −0.1 | −0.02
5 June 17:14:19 | 62.5 | 62.3 | −0.2 | −0.04
5 June 17:30:01 | 61.4 | 61.6 | +0.2 | −0.04

Table 3: Field-comparison pairs with photo time. SmartSense is the Node A reading interpolated at the photo time; the rate is the surface change over the surrounding ten minutes.

The FLIR image (Fig. 6), attributed in the field record to a C8 camera, corroborates the location and approximate 70–71 ◦C magnitude of the hotspot; it is not synchronized with the paired readings. The result is field consistency, not traceable calibration. The Fluke was also used to adjust the offset, so the comparison is not independent. The project cites instrument specifications of ±1.5 ◦C for the Fluke and ±2

| | | | ◦C for the FLIR, with

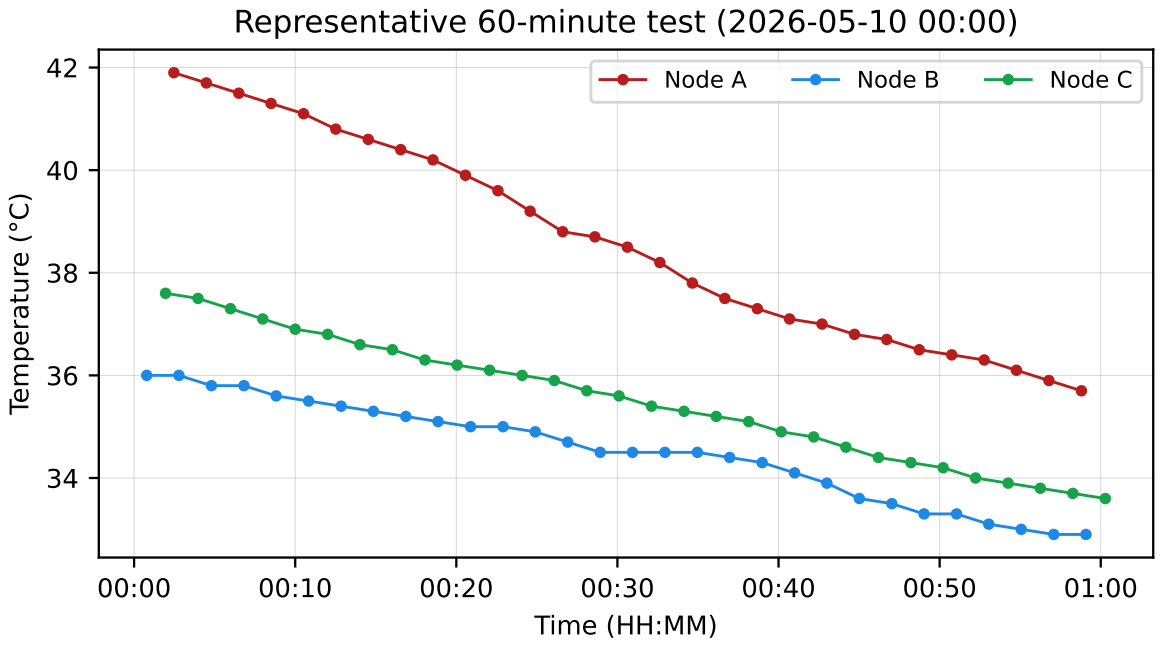
[picture p15: figure]
Time (HH:MM); Temperature (°C); Node A; Node B; Node C

00:00 | 00:10 | 00:20 | 00:30 | 00:40 | 00:50 | 01:00

## Representative 60-minute test (2026-05-10 00:00)

Figure 5: Temperature during a coverage-selected historical hour with three nodes. The original plot label “test” identifies this illustrative window, not a separate trial with a transmission counter.

no current Fluke calibration certificate. These limits exceed the order of the 1 ◦C target and are not a combined uncertainty budget for the installed system. Emissivity and viewed area affect infrared readings; contact and mounting affect the PT100. Complementary characterization must use a calibrated contact reference, separate adjustment from verification, compare the three nodes at multiple temperatures and account for reference, conversion, lead, mounting and repeatability contributions. Absolute accuracy and inter-node repeatability remain unestablished.

Field observation (case study). The suction-fan motor history includes rises and falls and a recorded maximum of 70.0 ◦C (Fig. 8). Plant observations associated rising segments with periods when the machine stopped while the fan continued spinning unloaded; no synchronized machine-state log establishes the timing or lag of each transition. The thermal image then provides spatial context for the hotspot (Fig. 6). Subsequent inspection associated the case with a bearing anomaly, which the plant team serviced during the machine stops of 30–31 May and 7–8 June 2026, after the 23 May peak; the exported history shows the probe near ambient temperature during those stops. This sequence—thermal history, operational context, thermal image and later inspection association—illustrates the use of historical data in condition monitoring. It does not establish diagnosis, prediction, lead time, causality, sensitivity or false-alarm performance; load, ventilation, mounting and other factors were not controlled.

Instrumented activity and temperature range. A firmware-instrumented interval was 2.279 s in eight of ten documented starts, with small variations reported for the remaining two. Instrumentation begins after initial serial setup and delay, so this is not total physical power-on-to-service time or synchronized network latency. Dividing by the 120 s cycle gives approximately 1.9% instrumented duty cycle; complete reset recovery remains to be measured through reception and persistence at the gateway. Across the individual historical files, surface temperature spanned 15.3–70.0 ◦C, with per-node means of 39.5–45.4 ◦C. These statistics describe recorded thermal behaviour, not calibrated range or measurement uncertainty.

Estimated battery autonomy. A controlled five-day partial discharge under the nominal 120 s operating cycle used the same 1000 mAh cell type fitted to the nodes, from 13 to 18 August 2026. Two volt-


Figure 6: Thermal image of the suction-fan motor, attributed to a FLIR C8 in the field record, locating a hotspot near 70–71 ◦C. It supplies spatial context without proving a bearing cause or the PT100’s absolute accuracy.

age readings, 4.112 V and 4.089 V over 120 h, give a slope of approximately 0.19 mV/h. The generator analisis/autonomia bateria.py extrapolates that slope to 3.30 V for a conservative linear estimate of 177 days. Its assumed typical LiPo open-circuit-voltage/state-of-charge curve, fitted to the same two points, gives 291–307 days at cutoffs of 3.30 and 3.00 V, respectively (Fig. 7). This range expresses two cutoffs under one model, not a statistical confidence interval. The curve is a project modeling assumption without a documented primary cell characterization. A component-level model built from datasheet currents and firmware timings (analisis/modelo consumo.py, Monte Carlo) gives 42–54 days, i.e. 3.5–6.4 times more consumption than the discharge implies; until node current is measured, autonomy is bounded between about 1.5 and 10 months.

Both values are estimated autonomy, not experimentally demonstrated lifetime. The linear result is conservative relative to the LiPo model but is not a guaranteed physical lower bound. Temperature, load, relaxation, ADC resolution, aging and self-discharge can alter the projection from this small voltage drop. Model-implied average current is approximately 0.13–0.24 mA; neither it nor the assumed microcontroller sleep current is an integrated measurement of the complete node. The 1.9% instrumented duty cycle does not establish energy consumption. A full discharge to a specified cutoff and current logging by operating state are needed.

Capabilities and limitations.

- Acquires periodic surface-temperature readings with a three-wire PT100 and configurable per-node offset; the tolerance class of the probe is not stated by the seller.
- Raw availability is 76.0%, 32.3% and 75.1% in the individual windows; conditioned link availability is 97.8–98.4% and PDR is inferred at 95.3–96.6%, using different gap filters.
- Operates locally with a rolling 30-day per-sensor store; older dates are removed after rotation. Pre-rotation exports preserved the records analysed beyond 30 days, including Node B’s longer history. LittleFS is an alternative storage medium, not a mirrored backup. Direct web CSV export is unverified and primary CSVs are absent from the reviewed repository.
- Six time-stamped pairs in steady state agree with the same Fluke used for the offset within 0.23 ◦C; a pair

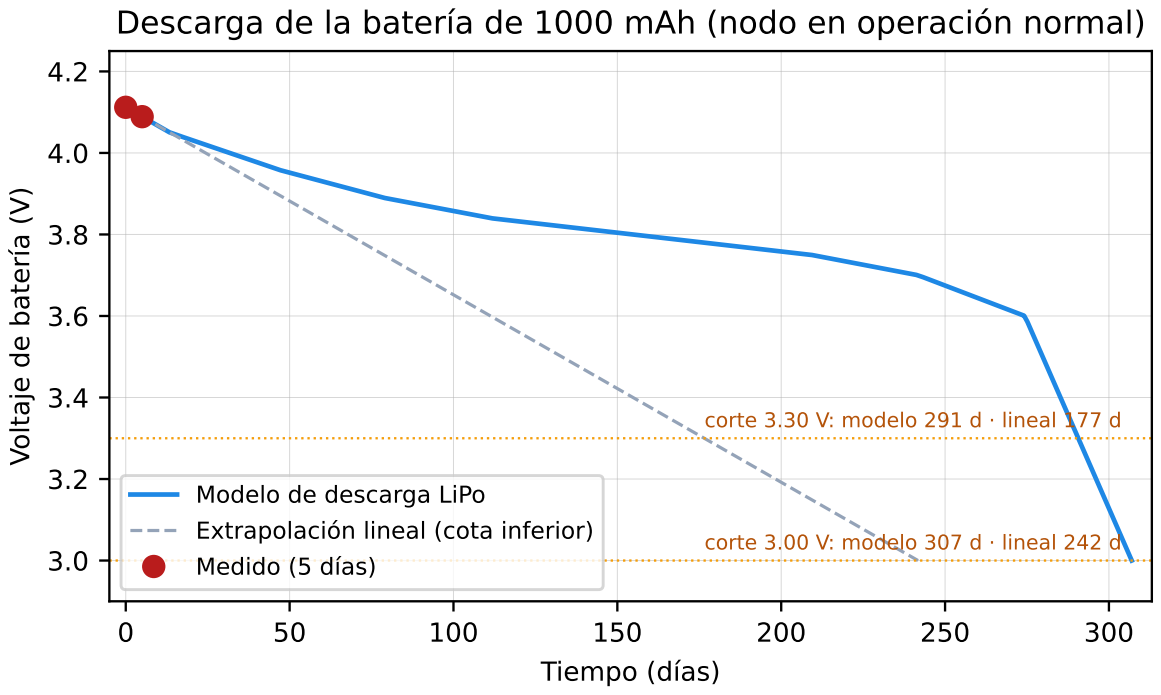
[picture p16: figure]
Tiempo (días); Voltaje de batería (V)

| | corte 3.30 V: modelo 291 d · lineal 177 | d
Modelo Extrapolación lineal (cota inferior) Medido | de descarga LiPo (5 días) | corte 3.00 V: modelo 307 d · lineal 242 | d

### Descarga de la batería de 1000 mAh (nodo en operación normal)

Figure 7: Two measured voltage points over five days with a 1000 mAh cell and extrapolated curves. Estimated autonomy is 177 days (linear, 3.30 V cutoff) or 291–307 days (assumed LiPo curve, 3.30/3.00 V cutoffs). The original plot’s lower-bound label compares models; it does not guarantee service lifetime.

taken during a warm-up differs by 3.6 ◦C. Absolute accuracy requires an independent calibrated contact reference and an uncertainty budget.
- A five-day partial discharge supports estimated autonomy of 177 days or 291–307 days under the stated model and cutoff assumptions; extended lifetime and complete-node current consumption were not experimentally demonstrated.
- LoRa range of at least ≈688 m in a non-line-of-sight urban path, with the link operating down to ≈ −98 dBm RSSI (test stopped voluntarily, not by link failure).
- The interface used did not expose SNR, and synchronized end-to-end latency and complete service recovery were not measured. Three deployed nodes do not constitute controlled inter-node repeatability or a network-capacity test.

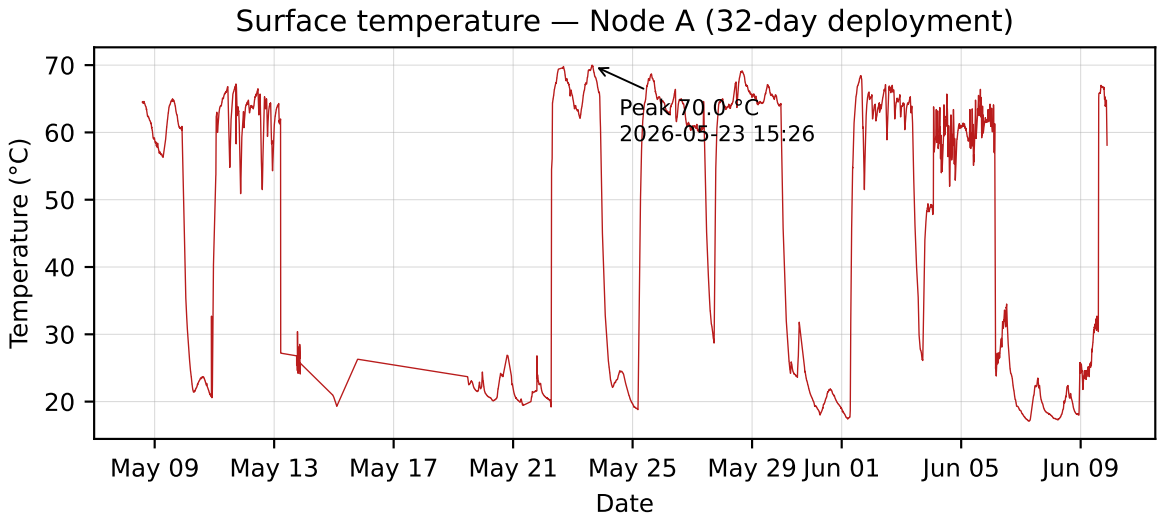
[picture p17: figure]
Date; Temperature (°C); Peak 70.0 °C 2026-05-23 15:26

May 09 May 13 May 17 May 21 May 25 May 29 Jun 01 | Jun 05 | Jun 09

## Surface temperature — Node A (32-day deployment)

Figure 8: Node A surface-temperature history during the 32-day pilot deployment. The 70.0 ◦C peak is a historical observation; its annotation does not identify a mechanical cause.

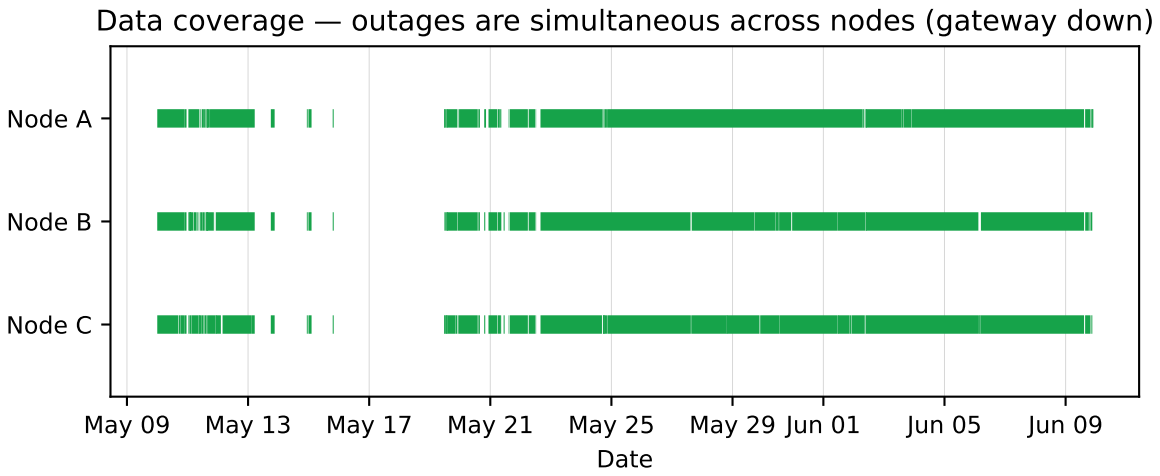
[picture p18: figure]
Date; Node C; Node B; Node A

May 09 | May 13 | May 17 | May 21 | May 25 | May 29 Jun 01 | Jun 05 | Jun 09

Data coverage — outages are simultaneous across nodes (gateway down)

Figure 9: Data coverage in the three-node overlapping interval. White gaps retain missing data. The original “gateway down” plot label is an interpretation compatible with simultaneous interruptions, not an independently verified power-state record.

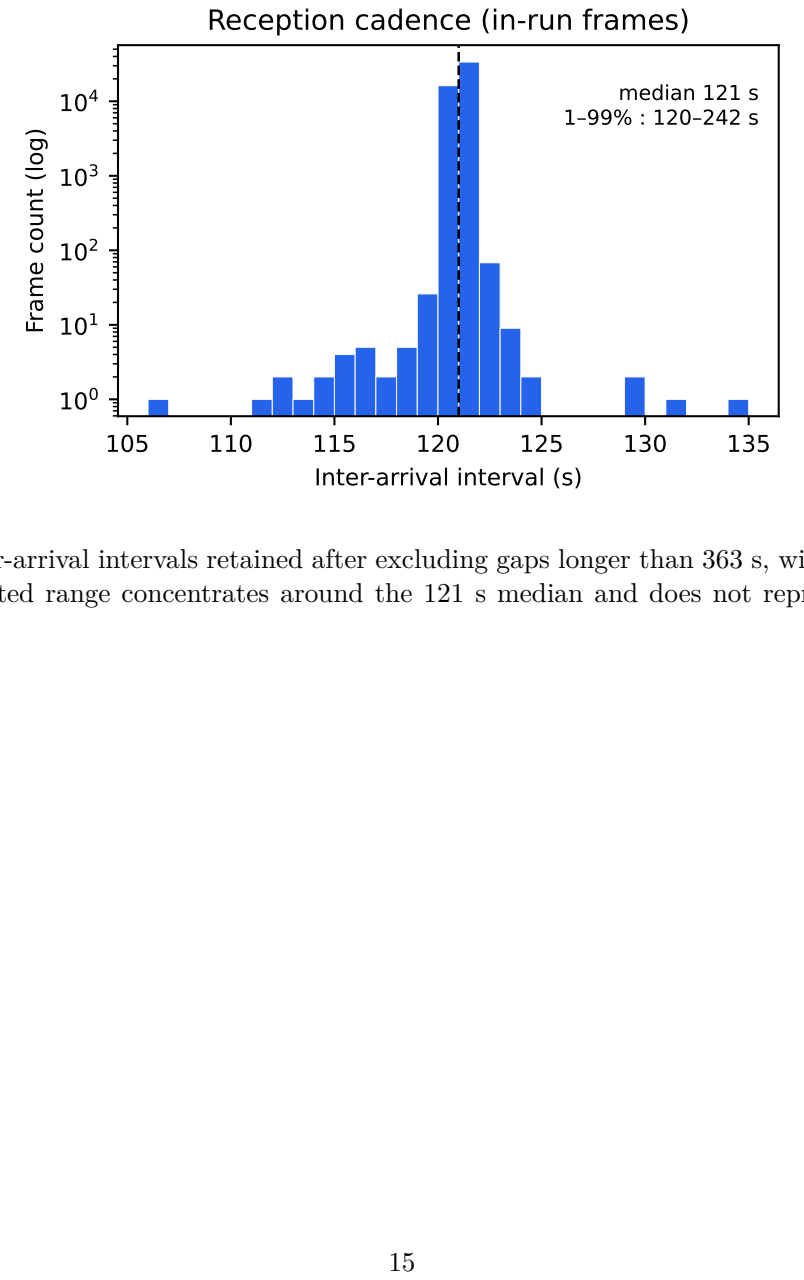
[picture p19: figure]
Inter-arrival interval (s); Frame count (log); median 121 s 1–99% : 120–242 s; Reception cadence (in-run frames)

Figure 10: Short inter-arrival intervals retained after | excluding gaps longer than 363 | s, with logarithmic frame-
count axis. The plotted range concentrates | around | the | 121 s | median and | does not represent the full outage
distribution.

Ethics statements
This work did not involve human subjects or animal experiments.

CRediT author statement
Jesus Andre Bojaca Lopez: Conceptualization, Methodology, Software, Investigation, Writing – Original draft. David Santiago Puentes Cardenas: Conceptualization, Hardware, Software, Validation, Data curation, Writing – Review & Editing. Jhon Edwin Vera: Supervision. Sergio Francisco Mora Martinez: Supervision.

Declaration of generative AI and AI-assisted technologies in the writing process
During the preparation of this work the authors used generative AI tools (ChatGPT, OpenAI, and Claude, Anthropic) to assist with language editing, restructuring and consistency checks of the manuscript. After using these tools, the authors reviewed and edited the content as needed and take full responsibility for the content of the publication.

Acknowledgements
The authors thank the partner company that provided access to the pilot plant. This research did not receive any specific grant from funding agencies in the public, commercial, or not-for-profit sectors.

References

[1] I. F. Akyildiz, W. Su, Y. Sankarasubramaniam, and E. Cayirci, “Wireless sensor networks: A survey,” Computer Networks, vol. 38, no. 4, pp. 393–422, 2002.
[2] J. Yick, B. Mukherjee, and D. Ghosal, “Wireless sensor network survey,” Computer Networks, vol. 52, no. 12, pp. 2292–2330, 2008.
[3] M. Centenaro, L. Vangelista, A. Zanella, and M. Zorzi, “Long-range communications in unlicensed bands: the rising stars in the IoT and smart city scenarios,” IEEE Wireless Communications, vol. 23, no. 5, pp. 60–67, 2016.
[4] A. K. S. Jardine, D. Lin, and D. Banjevic, “A review on machinery diagnostics and prognostics implementing condition-based maintenance,” Mechanical Systems and Signal Processing, vol. 20, no. 7, pp. 1483–1510, 2006.
[5] Advantech Co., Ltd., “WISE-2410 LoRaWAN wireless condition monitoring sensor,” Data Sheet, 23 October 2024. Manufacturer datasheet, (https://advdownload.advantech.com/productfile/PIS/WISE-2410/file/WISE-2410_DS%28102324%2920241023133301.pdf) accessed 15 September 2026.
[6] G. Mois, S. Folea, and T. Sanislav, “Analysis of three IoT-based wireless sensors for environmental monitoring,” IEEE Trans. Instrum. Meas., vol. 66, no. 8, pp. 2056–2064, 2017.
[7] A. Augustin, J. Yi, T. Clausen, and W. M. Townsley, “A study of LoRa: Long range & low power networks for the Internet of Things,” Sensors, vol. 16, no. 9, art. 1466, 2016.
[8] M. Bor, U. Roedig, T. Voigt, and J. M. Alonso, “Do LoRa low-power wide-area networks scale?” in Proc. 19th ACM MSWiM, 2016, pp. 59–67.
[9] T. Polonelli, D. Brunelli, A. Bartolini, and L. Benini, “A LoRaWAN wireless sensor network for data center temperature monitoring,” in Applications in Electronics Pervading Industry, Environment and Society, LNEE, vol. 573, Springer, 2019.
[10] M. O. Jakobsen, “Low cost MEMS accelerometer and microphone based condition monitoring sensor, with LoRa and Bluetooth Low Energy radio,” HardwareX, vol. 18, art. e00525, 2024.
[11] Z. M. C¸ ınar, A. A. Nuhu, Q. Zeeshan, O. Korhan, M. Asmael, and B. Safaei, “Machine learning in predictive maintenance towards sustainable smart manufacturing in Industry 4.0,” Sustainability, vol. 12, no. 19, art. 8211, 2020.
[12] R. R. Ribeiro, E. Bauer, and R. Lameiras, “HIGROTERM: An open-source and low-cost temperature and humidity monitoring system for laboratory applications,” Inventions, vol. 6, no. 4, art. 84, 2021.
[13] Chengdu Ebyte Electronic Technology Co., Ltd., “E220-400T22D user manual: 433/470 MHz 22 dBm LoRa wireless module,” v1.0, 2020. Manufacturer page, (https://www.cdebyte.com/products/E220-400T22D) accessed 17 September 2026.
[14] ZUIDID, “Magnetic RTD PT100 sensor, high temperature, oil and corrosion resistant,” AliExpress item 1005008619909588 product page (thin-film element, 19 × 9.5 mm probe, cable rated −60 to 200 ◦C, three-wire U-terminal), accessed 23 September 2026. Product page. (https://www.aliexpress.com/item/1005008619909588.html)
