DavidSPuentesc/SmartSense-Monitoring/hardware/kicad/nodo_sensor.pdf

1 | 2 | 3 | 4 | 5 | 6
1 | 2 | 3 | 4 | 5 | 6

AB

C

D

AB

C

### D Date:

Size: A4 | Rev:
KiCad E.D.A. 10.0.5 | Id: 1/1

## Title: SmartSense - Nodo sensor de temperatura

### File: nodo_sensor.kicad_sch

### Sheet: /

SmartSense Monitoring - design files | H1 1 | H2 2 | H3 3 | RT1 PT100 3 hilos D10 1 | D9 2 | D8 3 | D7 4
3V3 5 | GND 6 | D6 | 7 D5 | 8 D4 | 9 D3 | 10 D2 | 11 D0_A0 | 12 BAT_P | 13 BAT_N | 14 U1
XIAO ESP32-C6 | P1 1 | P2 | 2 R2
994.3k | CLK 1
SDO 2
SDI 3 | CS 4
VIN 5 | GND 6
3V3_OUT 7 | RDY 8
F_P | 9 RTD_P | 10 RTD_N | 11
F_N | 12 U4 MAX31865 (RREF 421.1) AUX 1 | M0 | 2 M1 | 3 RXD | 4
TXD | 5
VCC | 6 GND | 7 U3
Ebyte E220-433 POS | 1 NEG | 2 BT1

LiPo 3.7V 2000mAh

VBUS | 1 GND | 2
J3 USB carga | P1 1 | P2 | 2 R1

344.8k

IN_P 1

IN_N 2 | B_P 3 | B_N 4 | OUT_P | 5 OUT_N | 6 U5 Carga/proteccion LiPo

VBAT_SENSE GND
VBAT GND

# VBATGND

VBAT Divisor: VBAT - R1 - VBAT_SENSE (A0) - R2 - GND. Factor (R1+R2)/R2 = 1.347 PT100 3 hilos: par del mismo extremo a F+ y RTD+; hilo restante a RTD-, puenteado con F- (jumper 2/3-wire)

# Nodo sensor: XIAO ESP32-C6 + PT100/MAX31865 + LoRa E220-433

Verificado contra Nodo_Lora.ino; detalle en hardware/CONEXIONES.md
