DavidSPuentesc/SmartSense-Monitoring/figuras/modelo-consumo.pdf

0 | 10 | 20 | 30
Carga por ciclo (mA·s), caso nominal

ESP32-C6

E220 RX

E220 TX (exceso)

MAX31865 + RTD

33

18

33

4

Reparto del consumo activo

50 | 100 | 150 | 200 | 250 | 300
Autonomía estimada hasta 3.30 V (días)

0

250

500

750

1000

1250

1500

1750
Frecuencia (Monte Carlo)
fichas: 47 | d

[42, 54]

descarga observada,
lineal: 177 d

descarga observada,
curva LiPo: 291–307 d

Modelo por fichas frente a la descarga observada
