DavidSPuentesc/SmartSense-Monitoring/figuras/distribucion-temperatura.pdf

Node A | Node B | Node C

20

30

40

50

60

70

Temperature (°C)

Temperature distribution per node
