DavidSPuentesc/SmartSense-Monitoring/figuras/val-intervalos.pdf

105 | 110 | 115 | 120 | 125 | 130 | 135
Inter-arrival interval (s)

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
Frame count (log)

median 121 s
1–99% : 120–242 s

### Reception cadence (in-run frames)
