DavidSPuentesc/SmartSense-Monitoring/Entrega_SmartSense/Proyecto_SmartSense_Monitoring_IEEE.pdf

# SmartSense Monitoring: Sistema Inalámbrico para el Monitoreo y Análisis Histórico de Temperatura en Equipos Industriales

Jesus Andre Bojaca Lopez y David Santiago Puentes Cárdenas Programa de Ingeniería Electrónica, Facultad de Ingeniería Universidad ECCI, Bogotá D.C., Colombia {jesusa.bojacal, davids.puentesc}@ecci.edu.co

Resumen—Este artículo presenta el diseño, implementación y evaluación preliminar de SmartSense Monitoring, un sistema inalámbrico para medir temperatura superficial en equipos de una planta piloto. La solución está compuesta por nodos con microcontrolador XIAO ESP32-C6, sondas PT100 de tres hilos, acondicionadores MAX31865, alimentación mediante batería y comunicación LoRa con módulos Ebyte E220. Un gateway con ESP32-C6 recibe las mediciones, las almacena en una tarjeta microSD y las presenta mediante una pantalla local y un dashboard web. A diferencia de una inspección manual puntual, la solución conserva el comportamiento térmico durante las 24 horas, permite consultar días anteriores, comparar sensores, aplicar compensaciones de temperatura y configurar alarmas. Durante la validación en planta, el histórico permitió observar un incremento de temperatura en el motor de un succionador después de la parada de la máquina; el comportamiento se relacionó posteriormente con una condición anómala de los rodamientos. El sistema se comparó cualitativamente con una pistola de temperatura Fluke y con un sensor Advantech WISE-2410 en la configuración disponible en planta. Los resultados funcionales verificaron la adquisición, transmisión, almacenamiento, visualización histórica, compensación y gestión de alarmas. La evaluación cuantitativa de exactitud y disponibilidad se completará con los registros pareados de los instrumentos de referencia.
Index Terms—Internet de las cosas industrial, LoRa, PT100, MAX31865, monitoreo de temperatura, mantenimiento predictivo, dashboard, ESP32-C6.
I. INTRODUCCIÓN

El seguimiento de temperatura en motores y otros equipos industriales permite identificar cambios asociados con fricción, sobrecarga, ventilación deficiente o degradación mecánica. En una inspección manual, el operario obtiene únicamente el valor correspondiente al instante de la medición. Si este valor no se registra de manera sistemática, no es posible reconstruir la evolución térmica del equipo ni relacionarla con sus ciclos de operación y parada.
Las redes de sensores inalámbricos permiten distribuir puntos de medición sin instalar cableado de comunicación en cada ubicación [1], [2]. Para aplicaciones de baja tasa de datos, LoRa ofrece una alternativa de largo alcance y bajo consumo adecuada para nodos alimentados por batería [3], [4]. Estas características se aprovecharon en SmartSense Monitoring para construir una plataforma local, modular y configurable. El propósito del proyecto fue implementar y validar un sistema capaz de medir temperatura superficial, transmitirla

Insertar: arquitectura

Figura 1. Arquitectura implementada de SmartSense Monitoring.

de manera inalámbrica, conservar un histórico por sensor y facilitar el análisis del comportamiento térmico. El trabajo evolucionó desde un anteproyecto hasta un prototipo funcional instalado en una planta piloto. Por tanto, este documento describe las actividades realizadas y los resultados evidenciados, en lugar de presentar únicamente resultados esperados.
Las contribuciones principales del proyecto fueron: 1) integración de nodos PT100 de tres hilos con comunicación LoRa;
2) almacenamiento diario con respaldo local; 3) dashboard de 24 horas con comparación de sensores; 4) compensación configurable de temperatura; y 5) alarmas térmicas visuales, sonoras y mediante salida física.

II. ARQUITECTURA DEL SISTEMA
La arquitectura implementada, mostrada conceptualmente en la Fig. 1, está formada por nodos sensores, un enlace LoRa, un gateway y clientes locales conectados por Wi-Fi. Cada nodo adquiere la temperatura y el estado estimado de batería. El gateway recibe las tramas, identifica el nodo, aplica la compensación configurada, almacena la muestra y actualiza la interfaz.

II-A. Nodo sensor
Cada nodo fue construido con un Seeed Studio XIAO ESP32-C6, una sonda PT100 de tres hilos, un MAX31865, una batería LiPo y un módulo Ebyte E220. El MAX31865 fue configurado mediante la biblioteca de Adafruit en el modo MAX31865_3WIRE. Se utilizó una resistencia nominal de 100 Ω y una resistencia de referencia caracterizada en 421,1 Ω. En cada ciclo se efectuaron varias conversiones de temperatura y se descartaron valores inválidos. El firmware también consultó el registro de fallas del MAX31865 para detectar problemas de conexión o lecturas fuera de rango. La tensión de batería se obtuvo mediante el convertidor analógico-digital del ESP32-C6 y un divisor resistivo. El porcentaje estimado se calculó entre 3,30 V y 4,10 V.
La trama de aplicación incluyó el identificador del nodo, temperatura, porcentaje de batería y dirección MAC. Después de la transmisión, el nodo ingresó en sueño profundo. El periodo puede configurarse entre 5 y 7200 segundos; durante la versión evaluada se utilizó un valor predeterminado de 60 segundos.

II-B. Comunicación LoRa

La comunicación se implementó con módulos UART Ebyte E220 configurados mediante comandos AT. Se utilizó direccionamiento fijo, un canal común para los nodos y el gateway, velocidad serial de 9600 bit/s y velocidad aérea de 2,4 kbit/s. La dirección MAC identifica de manera persistente cada sensor, mientras que la dirección de radio permite encaminar los mensajes.
El firmware del gateway posee un campo reservado para RSSI, pero la versión revisada no habilita ni procesa dicho valor desde el E220. Tampoco se procesa la relación señalruido (SNR). En consecuencia, estas variables no se presentan como resultados experimentales del prototipo actual.

II-C. Gateway y persistencia

El gateway fue implementado con un ESP32-C6, pantalla táctil con controlador ST7789, módulo E220 y tarjeta microSD. La tarjeta se utiliza como medio principal para los históricos. Si no está disponible, LittleFS funciona como respaldo. Para cada dirección MAC se crea un directorio independiente y un archivo por fecha. Cada línea contiene el segundo transcurrido desde el inicio del día y la temperatura representada con resolución de 0,1

◦C. El firmware conserva hasta 30 días por sensor. La hora se sincroniza desde el navegador y se ajusta a la zona horaria UTC–5, por lo cual el sistema puede trabajar localmente sin conexión permanente a Internet.

III. DASHBOARD Y FUNCIONES DE SUPERVISIÓN

El | gateway | crea | el | punto | de | acceso | Wi-Fi
Sensores_Temp y publica el dashboard en la dirección local 192.168.4.1. La actualización de los datos se realiza mediante eventos enviados por el servidor aproximadamente cada segundo.
La interfaz implementada permite visualizar temperatura, batería y conectividad; consultar fechas disponibles; representar las 24 horas; obtener mínimo, máximo y promedio; comparar sensores de una misma máquina; asignar nombres; configurar el intervalo de muestreo; aplicar compensaciones; y establecer umbrales de advertencia y condición crítica.
La Fig. 2 muestra nueve sensores registrados y organizados en cinco grupos: Twin, Molino 1, Empaque A, Cuarto Frío y sensores aún sin asignar. Cada tarjeta presenta la última temperatura, batería, estado de conexión, intervalo térmico y una minigráfica. La agrupación permite comparar sensores pertenecientes a una misma máquina y reduce el tiempo necesario para localizar una condición anómala. La interfaz también integra accesos a emergencias, configuración y selección del diseño visual.

III-A. Compensación de temperatura

Para aproximar la lectura de cada PT100 al instrumento de referencia se implementó una compensación configurable. El usuario captura una referencia en condición fría y posteriormente establece un ajuste en condición caliente. Entre ambos puntos, el firmware aplica una compensación progresiva.
Si Tr es la temperatura cruda, Tf la referencia fría, Tc el punto de calibración caliente y O el offset establecido, la compensación dentro del intervalo puede expresarse como

Tcorr = Tr + O

(
Tr − Tf
Tc − Tf

)
, | (1)

limitando el factor de interpolación entre cero y uno. Por debajo de la referencia fría no se aplica corrección y, por encima del punto caliente, se aplica el offset completo.

Evidencia pendiente: tabla con lectura cruda, cámara termográfica, offset y lectura corregida para cada nodo.

III-B. Alarmas

Cada nodo posee un umbral de advertencia y un umbral crítico configurables. Al superar el primero, el dashboard cambia la representación visual. Al superar el segundo, se activa el estado crítico, una alarma sonora opcional en el navegador y la salida física definida en el gateway. El usuario puede silenciar la alarma sin eliminar el registro del evento. La arquitectura permite integrar posteriormente módulos de relés o variables de control. Sin embargo, cualquier acción automática sobre maquinaria debe diferenciarse de las alarmas ya verificadas y validarse bajo criterios de seguridad industrial.

IV. METODOLOGÍA DE EVALUACIÓN

La validación se estructuró en cuatro etapas. Primero se verificó la lectura de las PT100 y el reporte de fallas del MAX31865. Luego se comprobó el envío de tramas y la identificación de los nodos. En la tercera etapa se validaron el almacenamiento, la consulta por fecha y las funciones del dashboard. Finalmente, el sistema se instaló temporalmente en equipos de la planta para observar el comportamiento térmico durante la operación.
La exactitud se evaluará con muestras pareadas entre SmartSense y un instrumento de referencia. Para n pares de datos, el error absoluto medio se calcula mediante

MAE = 1
n

∑n

i=1

|TSS,i − Tref,i| . | (2)

También se calcularán temperatura mínima, máxima, promedio, diferencia antes y después del offset y duración de los incrementos térmicos relevantes.


Figura 2. Interfaz principal de SmartSense Monitoring con los sensores agrupados por máquina. La captura evidencia la supervisión simultánea de nueve registros y la presentación de temperatura, batería, conectividad y tendencia reciente.

Cuadro I
FORMATO DE MEDICIÓN PAREADA EN PLANTA
Hora | SmartSense | Referencia | Estado
| (
| ◦C) | (
| | ◦C) | máquina
Pendiente | – | – | Operación/parada
Pendiente | – | – | Operación/parada
Pendiente | – | – | Operación/parada
V. COMPARACIÓN CON MÉTODOS DISPONIBLES
V-A. Medición manual con pistola Fluke
En el primer escenario, un operario se desplaza hasta el equipo y obtiene una lectura puntual. Por ejemplo, una medición de 60 ◦C en el motor del succionador describe únicamente el instante de la inspección. El procedimiento resulta útil como verificación directa, pero depende de la disponibilidad del operario y no conserva automáticamente la evolución anterior y posterior.

V-B. Advantech WISE-2410
El WISE-2410 disponible en la planta es un dispositivo industrial de monitoreo de condición que integra acelerómetro de tres ejes, temperatura, procesamiento local y LoRaWAN [8]. Su capacidad de medir vibración constituye una ventaja para el diagnóstico mecánico.
La comparación de visualización se restringió a la configuración y plataforma disponibles en la planta. En esta implementación, el equipo de trabajo observó una ventana temporal limitada y no dispuso de la misma flexibilidad para ajustar la lectura térmica o consultar directamente un día completo. Esta observación no se presenta como una limitación general del WISE-2410, pues sus capacidades dependen del gateway, servidor y aplicación empleados.

V-C. SmartSense Monitoring
SmartSense presentó el historial de la fecha seleccionada sobre un eje de 24 horas, compensación independiente por nodo, comparación entre sensores y umbrales configurables. Además, funcionó mediante una red local sin depender de servicios externos.

VI. RESULTADOS OBTENIDOS
La Tabla III resume las funciones verificadas mediante revisión del firmware y pruebas funcionales del prototipo. Los resultados cuantitativos de planta se mantienen separados hasta incorporar los archivos originales y las mediciones de referencia.

VI-A. Caso del motor del succionador
La Fig. 3 corresponde al succionador de la máquina Twin y presenta una jornada completa, desde aproximadamente las 00:01 hasta las 23:59. Al inicio se observó una condición relativamente estable cercana a 48 ◦C a 49 ◦C. Alrededor de la 01:30 ocurrió un incremento rápido hasta una zona superior a 63 ◦C. Después del transitorio, la mayor parte de la curva permaneció aproximadamente entre 57 ◦C a 61 ◦C, con ciclos repetidos de calentamiento y enfriamiento.

Cuadro II
COMPARACIÓN CUALITATIVA DE LOS MÉTODOS EVALUADOS
Criterio | Pistola Fluke | WISE-2410 evaluado | SmartSense Monitoring
Adquisición | Puntual y manual | Automática y periódica | Automática y periódica
Dependencia del opera- rio | Alta | Baja | Baja
Histórico | Requiere registro externo | Depende de la plataforma instalada | Archivo diario por sensor
Visualización observada | Un valor instantáneo | Ventana disponible en planta | Fecha seleccionable y 24 horas
Ajuste térmico | Depende del instrumento | No disponible para el equipo en la inter-
| | faz evaluada | Offset configurable por nodo
Alarmas | No incorporadas | Dependen de la integración | Advertencia, crítica, visual y sonora
Comparación entre sen- sores | No | Depende de la plataforma | Incluida en el dashboard
Variables | Temperatura | Vibración y temperatura | Temperatura, batería, conexión y alarmas
Operación sin Internet | Sí | Depende de la arquitectura | Sí, mediante servidor local

Cuadro III
RESULTADOS FUNCIONALES VERIFICADOS
Función | Estado
Lectura de PT100 de tres hilos | Implementada
Detección de fallas del MAX31865 | Implementada
Identificación individual de nodos | Implementada
Temperatura y batería en la trama | Implementada
Sueño profundo y periodo configurable | Implementada
Almacenamiento microSD/LittleFS | Implementada
Histórico por sensor y fecha | Implementada
Gráfica diaria de 24 horas | Implementada
Mínimo, máximo y promedio | Implementada
Comparación de sensores | Implementada
Offset progresivo por nodo | Implementada
Umbrales y alarmas | Implementada
Exportación directa CSV | Por verificar
RSSI y SNR experimentales | No implementados

Se identificaron varios picos breves por encima de 63 ◦C. El mayor ocurrió cerca del mediodía y el dashboard mostró una máxima de 67,0

◦C. También se observaron descensos hasta la zona de 52 ◦C a 55 ◦C durante la tarde, seguidos por recuperaciones progresivas. A partir de aproximadamente las 21:00, la temperatura aumentó de forma gradual y se estabilizó alrededor de 60 ◦C a 61 ◦C hasta finalizar el día. El cambio de color de la curva representa los umbrales configurados: verde para la zona inferior, naranja para advertencia y rojo para condición térmica alta.
Este patrón muestra que el calentamiento no correspondió a un único evento aislado. La serie histórica permitió observar transitorios y repeticiones que no podrían reconstruirse con una medición manual ocasional. De acuerdo con la operación observada en planta, los tramos ascendentes corresponden a periodos en los que la Twin se detuvo y el motor del succionador permaneció girando en vacío. Los descensos se presentaron cuando la máquina volvió a operar. Esta relación aporta contexto al comportamiento térmico, aunque las horas exactas deberán confirmarse con un registro de marcha y parada.
La revisión posterior relacionó el patrón con una condición anómala en los rodamientos. Para presentar este hallazgo como resultado concluyente se incorporarán la gráfica original, la hora de parada, la magnitud del incremento y la evidencia de inspección o mantenimiento.
La captura muestra un mínimo de 21,8

◦C, un promedio
de 36,6

◦C y un máximo de 67,0

◦C. Sin embargo, los dos
primeros valores no concuerdan con el intervalo visible de la curva. La revisión del dashboard mostró que la actualización periódica puede sobrescribir los indicadores del histórico seleccionado con las estadísticas del día actual, mientras conserva en pantalla la curva de la fecha consultada. Por rigor experimental, el mínimo y el promedio de esta jornada se recalcularán a partir del archivo original antes de utilizarlos como resultados cuantitativos.

Evidencia pendiente: archivo original del día, horas de marcha y parada de la Twin y confirmación de la inspección de rodamientos.

VII. EVIDENCIAS COMPLEMENTARIAS PENDIENTES
La Fig. 4 reserva los espacios de las evidencias que se incorporarán en la versión final. Cada fotografía deberá acompañarse con fecha, equipo, instrumento y una descripción breve del procedimiento realizado.

VIII. DISCUSIÓN
La principal ventaja evidenciada no fue únicamente la medición inalámbrica, sino la continuidad temporal. Un valor puntual informa el estado presente; una serie de tiempo permite identificar tendencias, retardos térmicos y eventos asociados con cambios de operación. El dashboard desarrollado facilitó este análisis al conservar el contexto diario completo.
La compensación configurable mejora la concordancia con una referencia, pero no reemplaza un procedimiento formal de calibración. La exactitud final depende de la clase de la PT100, la resistencia de los conductores, el contacto térmico, la ubicación de la sonda y la incertidumbre del instrumento de referencia. Por ello, la evaluación cuantitativa debe utilizar muestras simultáneas y documentar el montaje.
El límite actual de 30 días es una decisión de firmware y puede ampliarse según la capacidad de la microSD. Asimismo, los archivos poseen una estructura separada por comas, pero la versión revisada no expone todavía una ruta web de descarga CSV. Esta función debe verificarse en otra versión o implementarse antes de declararla como resultado definitivo.


Figura 3. Histórico térmico de 24 horas del succionador de la máquina Twin. La captura fue obtenida del dashboard local desarrollado. El estado offline corresponde al momento de consulta del histórico y no invalida las muestras almacenadas.

Nodo PT100 instalado en el succionador de la Twin

(a) Instalación del nodo

Medición simultánea con
pistola Fluke
(b) Referencia Fluke

Captura o fotografía de la cámara termográfica

(c) Cámara termográfica

Interfaz del Advantech
WISE-2410 usada en planta
(d) WISE-2410

Tres nodos construidos y
gateway con pantalla
(e) Prototipos físicos

Inspección o mantenimiento de los rodamientos

(f) Evidencia mecánica

Históricos de los otros puntos de medición

(g) Otros sensores

Configuración de offset y
umbrales de alarma
(h) Configuración

Figura 4. Espacios reservados para las evidencias experimentales y de implementación que se incorporarán en la versión final.

IX. CONCLUSIONES

Se diseñó e implementó un sistema funcional para el monitoreo inalámbrico de temperatura superficial en una planta piloto. Los nodos adquirieron datos mediante PT100 de tres hilos y MAX31865, los transmitieron por LoRa y redujeron consumo mediante sueño profundo. El gateway almacenó las muestras y proporcionó visualización local sin depender de Internet.
El dashboard superó la presentación de un valor instantáneo al ofrecer históricos de 24 horas, estadísticas diarias, comparación entre sensores, compensación y alarmas configurables. Esta continuidad permitió observar un comportamiento térmico anómalo en el motor del succionador después de la parada de la máquina.
La comparación mostró que la pistola Fluke continúa siendo útil como instrumento de referencia puntual y que el WISE-2410 aporta variables industriales adicionales, especialmente vibración. SmartSense se destacó por la adaptación del dashboard a las necesidades específicas de visualización y análisis

térmico de la planta.
Como trabajo siguiente se incorporarán las mediciones pareadas, se calculará el MAE antes y después de la compensación, se documentará la disponibilidad del enlace, se habilitará RSSI y se completará la exportación directa de datos.

AGRADECIMIENTOS

Los autores agradecen a la empresa aliada por facilitar el escenario de planta piloto, al profesor Jhon Edwin Vera por la dirección principal del proyecto y al profesor Sergio Francisco Mora Martínez por su acompañamiento durante la formulación y el desarrollo.

REFERENCIAS

[1] I. F. Akyildiz, W. Su, Y. Sankarasubramaniam y E. Cayirci, “Wireless sensor networks: A survey,” Computer Networks, vol. 38, no. 4, pp. 393– 422, 2002.
[2] J. Yick, B. Mukherjee y D. Ghosal, “Wireless sensor network survey,” Computer Networks, vol. 52, no. 12, pp. 2292–2330, 2008.

[3] M. Centenaro, L. Vangelista, A. Zanella y M. Zorzi, “Long-range communications in unlicensed bands: The rising stars in the IoT and smart city scenarios,” IEEE Wireless Communications, vol. 23, no. 5, pp. 60–67, 2016.
[4] Semtech Corporation, “AN1200.22 LoRa modulation basics,” Application Note, 2015.
[5] Analog Devices, “MAX31865 RTD-to-digital converter,” Data Sheet, Rev. 3, 2015. [En línea]. Disponible: https://www.analog.com/media/en/technical-documentation/data-sheets/MAX31865.pdf (https://www.analog.com/media/en/technical-documentation/data-sheets/MAX31865.pdf)
[6] Seeed Studio, “Getting started with Seeed Studio XIAO ESP32-C6,” 2026. [En línea]. Disponible: https://wiki.seeedstudio.com/xiao_esp32c6_getting_started/ (https://wiki.seeedstudio.com/xiao_esp32c6_getting_started/)
[7] Chengdu Ebyte Electronic Technology Co., Ltd., “E220 series LoRa UART module user manual,” documentación técnica del fabricante.
[8] Advantech Co., Ltd., “WISE-2410 LoRaWAN wireless condition monitoring sensor,” Data Sheet, 2024. [En línea]. Disponible: https://advdownload.advantech.com/productfile/PIS/WISE-2410/file/WISE-2410_DS(102324)20241023133301.pdf (https://advdownload.advantech.com/productfile/PIS/WISE-2410/file/WISE-2410_DS(102324)20241023133301.pdf)
[9] J. Lee, B. Bagheri y H.-A. Kao, “A cyber-physical systems architecture for Industry 4.0-based manufacturing systems,” Manufacturing Letters, vol. 3, pp. 18–23, 2015.
[10] W. Shi, J. Cao, Q. Zhang, Y. Li y L. Xu, “Edge computing: Vision and challenges,” IEEE Internet of Things Journal, vol. 3, no. 5, pp. 637–646, 2016.
