DavidSPuentesc/SmartSense-Monitoring/tesis/capitulos/06-diseno-metodologico.tex

\chapter{Diseño metodológico}
\label{cap:metodologia}

\section{Tipo de investigación y enfoque}
Es una investigación aplicada, de tipo experimental: se construyó un prototipo, se evaluaron sus funciones y se observó su operación en planta. La unidad de adquisición es el nodo con su sonda; la unidad de análisis, la serie temporal de cada nodo identificada por su MAC. El piloto comprendió \NumeroNodos{} nodos y un gateway, y su propósito fue obtener un histórico consultable y valorar adquisición, comunicación y persistencia en las condiciones disponibles.

La evidencia es de tres clases: verificaciones funcionales de la cadena implementada, registros del despliegue y ensayos complementarios de campo. Este capítulo define los procedimientos y los cálculos; los resultados y su interpretación van en el capítulo~\ref{cap:resultados}. Que un protocolo o una función existan en el firmware no cuenta como evidencia de que un ensayo se ejecutó.

\section{Población y muestra}
La población de estudio son los puntos de medición de temperatura superficial de la planta piloto; la muestra son los tres puntos instrumentados con un nodo cada uno: el motor del succionador de la máquina Twin y dos puntos adicionales de la misma planta. La unidad de análisis es la serie temporal de cada nodo, identificada por su MAC. El conjunto reúne \TotalMuestras{} muestras: \DuracionComunDias{} días para los nodos A y C, del 8 de mayo al 9 de junio de 2026, y del 10 de mayo al 20 de julio para el nodo B. Las comparaciones entre nodos se hacen sobre el tramo en que coinciden, y cada estadística individual declara sus fechas.

\section{Técnicas e instrumentos de recolección}
La adquisición la hacen los propios nodos: sonda PT100 de tres hilos, conversor MAX31865 y XIAO ESP32-C6, con transmisión LoRa al gateway y almacenamiento en archivos diarios por sensor. Como instrumentos de contraste se usaron un termómetro infrarrojo Fluke 62 MAX ($\pm$1.5~\textdegree C declarados, sin certificado vigente) y una cámara térmica FLIR C8 ($\pm$2~\textdegree C) para la imagen del punto caliente. Los registros se exportaron a CSV antes de la rotación de 30 fechas del gateway y se procesaron con los scripts de la carpeta \texttt{analisis/}: disponibilidad, pérdida estimada, ventana de 60 minutos, autonomía, alcance, cronología, modelo de consumo e incertidumbre. En los ensayos de agosto se usaron el monitor serie del nodo, un multímetro para la tensión de la celda y el registro de RSSI del gateway.

\section{Procedimiento: etapas y productos verificables}
La tabla~\ref{tab:metodo-etapas} relaciona las entradas, procedimientos, variables y salidas de cada etapa. Permite distinguir la construcción del sistema de la evaluación de los datos que produjo.

\begingroup
\small\singlespacing
\setlength{\tabcolsep}{3pt}
\begin{longtable}{@{}>{\raggedright\arraybackslash}p{2.05cm}>{\raggedright\arraybackslash}p{2.65cm}>{\raggedright\arraybackslash}p{4.0cm}>{\raggedright\arraybackslash}p{2.8cm}>{\raggedright\arraybackslash}p{3.1cm}@{}}
\caption{Secuencia metodológica y trazabilidad de sus productos.}\label{tab:metodo-etapas}\\
\toprule
\textbf{Etapa} & \textbf{Entrada} & \textbf{Procedimiento} & \textbf{Variable registrada} & \textbf{Salida} \\
\midrule\endfirsthead
\toprule
\textbf{Etapa} & \textbf{Entrada} & \textbf{Procedimiento} & \textbf{Variable registrada} & \textbf{Salida} \\
\midrule\endhead
\bottomrule\endfoot
Requisitos & Necesidad de histórico superficial y consulta local. & Traducir el uso en funciones de adquisición, envío, conservación, consulta y alarmas. & Periodo, identificación, retención y funciones requeridas. & Requisitos para contrastar con el prototipo. \\
Selección & Requisitos y documentación técnica disponible. & Comparar componentes por interfaces, montaje, energía y operación local. & Compatibilidad y limitaciones de cada alternativa. & Matriz de selección, tabla~\ref{tab:seleccion-componentes}. \\
Construcción & Componentes, esquemas y firmware. & Integrar PT100, conversor, nodo, radio, alimentación y gateway. & Conexiones, parámetros de conversión y radio. & Prototipo y esquemas reproducibles. \\
Verificación funcional & Prototipo integrado. & Revisar lectura, recepción por MAC, escritura, consulta diaria, offset y alarmas. & Lectura, trama, archivo y respuesta de interfaz. & Evidencia funcional de cada eslabón. \\
Ventana de 60 min & CSV histórico con los tres nodos. & Extraer una hora con cobertura simultánea y contar registros en $[t_0,t_0+1\,\mathrm{h})$. & Tiempo, temperatura y conteo por nodo. & Ejemplo de continuidad; no PDR directo. \\
Despliegue & Nodos sobre equipos y gateway local. & Observar marcha y parada sin bitácora sincronizada, exportar históricos y ordenar por MAC y fecha. & Temperatura, marcas temporales y huecos. & Series del piloto y cobertura individual: A/C, \DuracionComunDias{} días; B, periodo extendido. \\
Alcance & Nodo móvil, gateway y registro instrumentado. & Alejar el nodo y regresar en recorrido urbano con obstáculos. & Recepción, RSSI, batería y punto más lejano. & Cota inferior de alcance en ese recorrido. \\
Comparación térmica & PT100 instalada y Fluke 62 MAX. & Fotografiar el Fluke apuntando junto a la sonda y emparejar cada foto, por su hora, con el registro del nodo. & Lecturas SmartSense y referencia de campo. & Diferencias pareadas y límites de la comparación. \\
Descarga parcial & Nodo y celda de \SI{1000}{\milli\ampere\hour}. & Operar durante \SI{120}{\hour} y registrar tensión inicial y final. & Tensión y duración; tiempo activo por separado. & Dos extrapolaciones condicionadas, no vida útil medida. \\
\end{longtable}
\endgroup

\section{Requisitos de diseño}
Los requisitos centrales fueron medir por contacto sin tendido de cable de datos hasta cada máquina, identificar cada punto de adquisición, conservar el histórico por fecha y consultar la información sin Internet. Los criterios con que se eligió cada componente para cumplirlos, y las limitaciones aceptadas con cada elección, se documentan en la tabla~\ref{tab:seleccion-componentes} del capítulo~\ref{cap:fundamentos}, junto con los cálculos de dimensionamiento.

\section{Periodo de adquisición y carga de datos}
\label{sec:metodo-muestreo}
El periodo nominal del piloto fue \PeriodoNominal{}. La evolución térmica de la superficie de los equipos es lenta frente a las oscilaciones que se estudian por vibración, así que una serie con esa cadencia sigue los calentamientos y enfriamientos, aunque no capture transitorios más breves. No se midió la constante de tiempo del conjunto sonda y máquina.

Para operación continua, el volumen nominal por nodo se calcula como
\begin{equation}
N_{\text{día}}=\frac{86\,400~\mathrm{s}}{120~\mathrm{s}}=720
\quad\text{muestras por nodo y día}.
\label{eq:metodo-muestras-dia}
\end{equation}
Con \NumeroNodos{} nodos son 2160 muestras diarias y 64\,800 en los 30 días que retiene el gateway, antes de descontar interrupciones. Acortar el periodo multiplica en proporción inversa las conversiones, los envíos y las escrituras, y con ellas el consumo y la probabilidad de colisiones en el canal compartido \citep{bor2016}; el dimensionamiento del almacenamiento está en la sección~\ref{sec:fund-calculos}.

Los 120~s son un compromiso de este piloto; una aplicación con cambios térmicos más rápidos o alarmas más exigentes necesitaría otro valor. El firmware usa el parámetro como duración del sueño y suma la actividad al despertar, por lo que las recepciones no llegan cada 120~s exactos: la mediana observada fue \PeriodoMediano{}, y los cálculos publicados usan el periodo nominal.

\section{Protocolo de despliegue y evaluación de comunicación}
\label{sec:metodo-enlace}
La instalación fijó las sondas sobre las superficies de interés y vinculó cada MAC con un nodo y un equipo. La puesta en marcha comprendió comprobar recepción, configurar la hora local del gateway, revisar escritura diaria y confirmar acceso al dashboard. Se mantuvieron registros separados por sensor para estudiar los ciclos de operación y los huecos. El archivo analizado se conservó mediante exportación previa a la rotación de históricos; el procedimiento de almacenamiento se desarrolla en la sección~\ref{sec:impl-almacenamiento}.

Cada comparación del piloto declara su ventana: el archivo tiene cobertura desigual y el nodo B se extiende más allá de los \DuracionComunDias{} días de A y C. Las comparaciones entre equipos se recortan a las fechas compartidas, cada estadística individual lleva sus fechas de inicio y fin, y los huecos no se rellenan.

\subsection{Indicadores y exclusiones}
Se aplican las definiciones del marco de referencia a ventanas y poblaciones explícitas:
\begin{equation}
\mathrm{PDR}=\frac{N_{\mathrm{recibidos}}}{N_{\mathrm{enviados}}}\times100\%,
\qquad
A_{\mathrm{datos}}=\frac{N_{\mathrm{muestras\ disponibles}}}{N_{\mathrm{muestras\ esperadas}}}\times100\%.
\label{eq:metodo-indicadores}
\end{equation}
La disponibilidad cruda compara lo recibido con lo esperado en toda la ventana; la condicionada excluye los tramos clasificados como gateway apagado. Ninguna de las dos es el PDR, cuyo denominador ideal son los envíos reales.

El histórico no contenía secuencia de envío. El script \texttt{analisis/perdida\_paquetes.py} ordena las llegadas por MAC y obtiene $\Delta t_i=t_{i+1}-t_i$. Para intervalos de hasta 1800~s calcula
\begin{equation}
k_i=\operatorname{round}\!\left(\frac{\Delta t_i}{120~\mathrm{s}}\right),
\qquad
\widehat{N}_{\mathrm{faltantes},i}=\max(0,k_i-1).
\label{eq:metodo-perdida-inferida}
\end{equation}
Un intervalo cercano a $kT$ implica $k-1$ tramas faltantes si la cadencia fue estable; el denominador inferido es lo recibido más lo faltante. Los huecos mayores de 30~min se excluyen de esa suma y se cuentan aparte: cuando coinciden en los tres nodos se interpretan como paradas compartidas, aunque sin bitácora de alimentación siga siendo una inferencia. El método no ve pérdidas anteriores a la primera recepción ni posteriores a la última de cada tramo.

\subsection{Ventana representativa y protocolo instrumentado}
\label{sec:metodo-60min}
La ventana de una hora se extrae del despliegue con \texttt{analisis/prueba\_60min.py}, que busca, desde el comienzo compartido y en pasos de 30~min, la primera hora con al menos 25 registros de cada nodo; a la cadencia nominal se esperan $3600/120=30$. La ventana usada es la del 10 de mayo de 2026, de 00:00 a 01:00. Como se elige por buena cobertura, ilustra el funcionamiento y no representa todas las horas del despliegue, y la razón recibido sobre esperado es cobertura nominal, no un conteo de envíos.

Los documentos \texttt{analisis/PROTOCOLO\_PDR.md} y \texttt{analisis/PROTOCOLO\_PRUEBA\_60MIN.md} especifican una repetición instrumentada distinta: cargar y registrar el voltaje inicial, programar los tres nodos y el gateway, capturar el monitor serie durante 60~min y anotar inicio, duración y distancia. La trama añade \texttt{SEQ}, \texttt{VBAT} y \texttt{UP}; el gateway puede registrar RSSI cuando recibe el byte válido del radio. Antes de usarlo se debe comprobar recepción normal y que \texttt{rssi\_raw} sea distinto de $-1$, como prescribe el protocolo. La salida se procesa mediante \texttt{analisis/analizar\_prueba.py}.

El contador de secuencia, que sobrevive al sueño profundo, permite estimar los envíos entre el primer y el último valor observados; una medición controlada debe además tratar reinicios, duplicados y extremos de sesión. Estos protocolos son posteriores al piloto: no agregan secuencias ni RSSI al CSV histórico. El tiempo \texttt{UP} es el tiempo encendido del nodo hasta formar la trama, no la latencia extremo a extremo, que requiere relojes sincronizados.

\subsection{Ensayo de alcance con obstrucciones}
El ensayo del 20 de agosto de 2026 usó la configuración de 433~MHz del proyecto en un recorrido urbano sin línea de vista, con edificios interpuestos: un nodo se alejó del gateway y regresó mientras se registraban recepción, RSSI y batería frente al tiempo. Al ser móvil, no produce una curva de RSSI frente a distancia fija.

El recorrido llegó a unos \DistanciaDemostrada{} con el enlace operativo y terminó por decisión, no por pérdida del enlace; por eso ese punto es una cota inferior en las condiciones ensayadas y no un alcance máximo ni una cobertura garantizada en planta. El margen frente a la sensibilidad de ficha del E220-400T22D se calcula en la sección~\ref{sec:resultados-alcance}. El módulo no expone SNR.

\section{Comparación térmica de campo}
La comparación utilizó un Fluke 62 MAX como referencia de campo, sin certificado vigente de calibración disponible para el estudio. En cada visita se fotografió el Fluke apuntando a la carcasa del motor del succionador junto a la sonda. La hora de cada foto, tomada del teléfono, permite ubicar en el CSV exportado las dos muestras del nodo A que la rodean; la lectura de SmartSense en ese instante se interpola linealmente entre ellas (\texttt{analisis/parejas\_fluke.py}). Para cada pareja se calcula $\Delta T_i=T_{\mathrm{SS},i}-T_{\mathrm{ref},i}$, se resumen la media, la media absoluta de la ecuación~\ref{eq:marco-concordancia}, el RMSE y el máximo, y se registra la velocidad de cambio de la superficie en los diez minutos alrededor de la foto, porque una comparación durante un calentamiento rápido mide sobre todo el retardo térmico entre la carcasa y la sonda.

El resultado es concordancia con el instrumento usado, no calibración trazable \citep{jcgm2012,jcgm2008}: son pocas parejas, un solo nodo y un intervalo térmico estrecho, la referencia infrarroja y la sonda de contacto no observan la misma área, y el mismo Fluke sirvió para ajustar el offset. La exactitud absoluta requeriría una referencia calibrada y varios puntos en los tres nodos; mientras tanto, la incertidumbre se acota por especificaciones en la sección~\ref{sec:fund-incertidumbre}.

\section{Diseño energético y estimación de autonomía}
\label{sec:metodo-autonomia}
El intervalo de actividad se obtuvo del registro instrumentado del firmware. La variable \texttt{bootMs} se fija después de inicializar el puerto serie y de una pausa inicial de 200~ms; la duración se calcula antes del sueño, tras adquisición y transmisión. Por ello excluye la actividad anterior a esa marca y no mide todo el tiempo físico desde energización. El valor de referencia de \TiempoActivo{} y el periodo nominal dan
\begin{equation}
D=\frac{t_{\mathrm{activo}}}{T}=\frac{2.279}{120}=0.01899\approx1.9\,\text{\%}.
\label{eq:metodo-duty}
\end{equation}
Es la actividad dentro del intervalo instrumentado; no es el tiempo de emisión de radio ni la recuperación del enlace.

El modelo energético de dos estados permite expresar corriente media y autonomía ideal como
\begin{equation}
I_{\mathrm{media}}=D I_{\mathrm{activo}}+(1-D)I_{\text{sueño}},
\qquad
t_{\mathrm{aut}}=\frac{C_{\text{útil}}}{I_{\mathrm{media}}}.
\label{eq:metodo-autonomia-corriente}
\end{equation}
Con la capacidad en mAh y la corriente en mA, el cociente da horas; la corriente debe ser la del nodo completo y la capacidad la útil en las condiciones del ensayo.

\subsection{Entradas de la descarga parcial y dos extrapolaciones}
El script \texttt{analisis/autonomia\_bateria.py} utiliza una celda de \SI{1000}{\milli\ampere\hour} y dos lecturas: \SI{4.112}{\volt} el 13 de agosto y \SI{4.089}{\volt} el 18 de agosto de 2026, separadas por \SI{120}{\hour}. La caída observada de \SI{0.023}{\volt} se convierte en pendiente mediante
\begin{equation}
r_V=\frac{V_0-V_1}{\Delta t}=\frac{4.112-4.089}{120}
\approx 0.000192~\mathrm{V/h},
\qquad
\widehat{t}_{\mathrm{lineal}}=\frac{V_0-V_{\mathrm{corte}}}{r_V}.
\label{eq:metodo-lineal}
\end{equation}
Hasta \SI{3.30}{\volt} la estimación lineal da \AutonomiaLinealEstimada{}; el script la llama cota conservadora porque es la menor de sus dos proyecciones, no porque sea un mínimo garantizado.

El segundo cálculo interpola una tabla típica de tensión en circuito abierto frente a estado de carga (OCV--SoC). Si $s(V)$ es la fracción de carga interpolada, se supone descarga a ritmo constante:
\begin{equation}
r_s=\frac{s(V_0)-s(V_1)}{120~\mathrm{h}},
\qquad
\widehat{t}_{\mathrm{LiPo}}=\frac{s(V_0)-s(V_{\mathrm{corte}})}{r_s}.
\label{eq:metodo-lipo}
\end{equation}
El intervalo de \AutonomiaModeloEstimada{} corresponde a los cortes de 3.30 y \SI{3.00}{\volt}. Son salidas de un modelo ajustado a dos puntos: la tabla es típica y no una caracterización de esa celda, no consta que las lecturas fueran en reposo, y una caída tan pequeña es sensible a la resolución, la temperatura y las condiciones de lectura.

\subsection{Instrumentación para caracterizar corriente}
La figura~\ref{fig:metodo-montaje-corriente} muestra el montaje previsto para observar el pulso activo, un shunt de \SI{1}{\ohm} en el retorno de la batería y un osciloscopio, con $I(t)=V_{\mathrm{shunt}}(t)/R_{\mathrm{shunt}}$; el oscilograma no llegó a registrarse. El repositorio incluye además un programa con INA219 para la corriente activa. La corriente de sueño de \SI{15}{\micro\ampere} es el valor de ficha del XIAO ESP32-C6 \citep{xiaoc6}, no una medición del nodo completo, y el perfil del script de autonomía usa una corriente activa inferida del propio modelo.

\begin{figure}[htbp]
\centering

\caption[Montaje propuesto para medición de corriente con shunt.]{Montaje para medir la corriente del nodo con un shunt de lado bajo y un osciloscopio; la caída de tensión en el shunt se convierte en corriente. Es el esquema propuesto: el pulso activo y la corriente de sueño no llegaron a registrarse. Fuente: diagrama del repositorio.}
\label{fig:metodo-montaje-corriente}
\end{figure}

\section{Trazabilidad y límites de reproducción}
Reproducir el análisis requiere el CSV exportado, las fechas, las MAC, la configuración y los registros serie de los ensayos. Los scripts toman el CSV de una ruta local configurable; el CSV mismo no está en el repositorio (sección~\ref{sec:anexos-reproducibilidad}).
