DavidSPuentesc/SmartSense-Monitoring/tesis/capitulos/09-discusion-limitaciones.tex

\chapter{Discusión, limitaciones y amenazas a la validez}
\label{cap:discusion}

\section{Aporte del sistema frente al problema de monitoreo}
El aporte del piloto consiste en integrar adquisición superficial, comunicación inalámbrica y consulta local de series identificadas por nodo. Los \TotalMuestras{} registros documentados permiten examinar comportamientos anteriores y posteriores a una inspección puntual. Esta capacidad responde al objetivo general del capítulo~\ref{cap:objetivos}: conservar contexto térmico para apoyar el monitoreo de condición. Su utilidad depende de conocer la cobertura real y las limitaciones del dato, no únicamente de disponer de una gráfica.

Frente a los métodos disponibles, el Fluke da una lectura puntual útil para contrastar una condición en campo y SmartSense añade el registro automático y el histórico. El WISE-2410 incorpora vibración y depende de su plataforma de integración (capítulo~\ref{cap:estado-arte}); la comparación es funcional, porque no hubo un ensayo controlado con los mismos puntos de montaje, referencias y criterios.

La operación local permite consultar sin Internet y la apertura del firmware permite estudiar cómo se forman y conservan los datos. La reproducibilidad es parcial: la sonda se identifica por marca y origen de compra, sin clase de tolerancia, y los CSV primarios no están en el repositorio. La contribución es un prototipo documentado y evaluado en un piloto, no una solución industrial certificada ni una red mayor que la ensayada.

\section{Qué significa la concordancia térmica obtenida}
La diferencia frente a una referencia de campo responde a una pregunta acotada: cuánto se separan dos indicaciones en el montaje y el rango observados. Seis parejas estables de un solo nodo entre 51.6 y \SI{67.6}{\celsius} no cubren desde ambiente hasta la temperatura de operación, ni las diferencias entre los tres conjuntos PT100 y MAX31865, ni la deriva con el tiempo o el desmontaje.

El mismo Fluke sirvió para fijar el offset y para contrastar, lo que favorece diferencias pequeñas; la concordancia no es una validación independiente. Las especificaciones de $\pm\SI{1.5}{\celsius}$ del Fluke y $\pm\SI{2}{\celsius}$ de la FLIR superan el objetivo de \SI{1}{\celsius}, y no son incertidumbres estándar que se sumen sin un modelo \citep{jcgm2008,jcgm2012}; el presupuesto por especificaciones de la sección~\ref{sec:fund-incertidumbre} es ese modelo, y da \IncertidumbreTipoB{} con clase B.

La comparación descansa solo en parejas verificables: cada una tiene una fotografía con hora y la lectura del nodo en ese instante está en el CSV (sección~\ref{sec:resultados-termica}). Las lecturas de campo de una visita sin registro exportado se conservan como observación, pero no entran en la estadística. La pareja tomada durante un arranque muestra que comparar una sonda de contacto con un termómetro infrarrojo solo tiene sentido con la superficie estable, y así se declara en vez de retirarla sin decirlo.

Una evaluación metrológica separa ajuste y comprobación, usa una referencia calibrada de contacto en varios puntos y repite el montaje en los tres nodos; su incertidumbre combinada incluye referencia, resistencia de referencia, conversión, conductores, contacto térmico y repetibilidad. La clase de la PT100 instalada no está documentada; el presupuesto la asume de clase B y lo declara.

\section{Disponibilidad, inferencia de paquetes y continuidad del servicio}
La disponibilidad cruda muestra la limitación práctica: cuando el gateway deja de recibir o de guardar, no hay historial nuevo aunque el enlace funcione. Por eso 76.0\,\%, 32.3\,\% y 75.1\,\% acompañan siempre al intervalo condicionado de \DisponibilidadEnlace{}; el valor bajo del nodo B viene de una ventana más larga con un hueco prolongado, no de un peor radio o sensor.

La simultaneidad de las interrupciones apunta a una causa común, y la cronología las hace coincidir con las paradas de planta; aun así no distingue entre energía, recepción, reloj o almacenamiento. Atribuir todos los huecos a apagados haría ver mejor el enlace al excluir justo los intervalos peores, así que la métrica cruda se conserva y el criterio de exclusión se declara.

Los generadores de disponibilidad y PDR usan filtros distintos, 121~s con huecos de 363~s frente a 120~s con exclusión de 1800~s, así que sus valores no son dos mediciones del mismo denominador. El \PDREstimado{} depende de la estabilidad del ciclo, del redondeo y de la exclusión de huecos largos, y sin secuencia de envíos no separa pérdida de radio, falta de adquisición y falta de persistencia.

La hora con 29/30, 30/30 y 30/30 registros es un ejemplo de cobertura nominal elegido por su continuidad, no una estimación de cuántas horas del despliegue la alcanzan. Una evaluación directa fija las ventanas antes del ensayo y cuenta envíos y recepciones, con reglas para reinicios, duplicados y extremos de sesión.

En la persistencia, LittleFS es un medio alternativo a la microSD y no un espejo (sección~\ref{sec:impl-almacenamiento}); conservar 30 fechas y exportar antes de la rotación permite estudiar periodos mayores, pero si la extracción no se hace los archivos se pierden. La descarga CSV por web no se verificó.

\section{Interpretación del alcance y de la energía}
El enlace operativo a al menos \DistanciaDemostrada{} demuestra factibilidad en el recorrido con obstrucciones. Como posición, orientación de antenas y obstáculos cambian mientras el nodo se desplaza, la curva de RSSI frente al tiempo no separa el efecto de la distancia ni da una ley de propagación, y no garantiza cobertura en otra planta.

El módulo es un E220-400T22D a 22~dBm; el margen cercano a 29~dB frente a su sensibilidad de ficha a 2.4~kbps indica reserva en el punto más lejano visitado, aunque no sustituye la medición del punto de pérdida. El módulo no expone SNR y el histórico de planta no tiene RSSI; la instrumentación posterior sirve para nuevos ensayos, no para completar los registros anteriores.

Las proyecciones energéticas muestran cuánto depende la conclusión del modelo: con los mismos dos puntos de tensión se obtienen \AutonomiaLinealEstimada{} por extrapolación lineal y \AutonomiaModeloEstimada{} con una curva LiPo típica, y el modelo por estados con fichas técnicas (sección~\ref{sec:resultados-modelo-consumo}) proyecta \AutonomiaFichaRango{}, entre 3.5 y 6.4 veces más consumo del que implica la descarga observada. Hasta que se mida la corriente del nodo, la autonomía queda acotada entre mes y medio y diez meses; la descarga parcial cubre \DuracionDescarga{} sin llegar al corte, y la temperatura, la autodescarga y el envejecimiento cambian la relación entre tensión y carga disponible.

El intervalo instrumentado de \TiempoActivo{} describe la actividad del firmware, no el tiempo total desde la energización ni la latencia de red, que termina cuando el gateway recibe, fecha, persiste y presenta la lectura. Y un ciclo de trabajo de \CicloTrabajo{} no es una medición de energía: los periféricos, los reguladores y el radio consumen también durante el sueño y hay que medirlos en la entrada del nodo completo.

\section{Alcance del caso del rodamiento}
La serie del succionador permite plantear una observación pertinente para operación: existen ascensos y descensos que justifican revisar el contexto de funcionamiento y el estado del equipo. La imagen térmica localiza calentamiento sobre la carcasa y la inspección posterior asocia el caso con una condición de rodamientos. Esta secuencia aporta un caso documentado de uso del histórico.

No hay bitácora sincronizada de las transiciones de la máquina, ni registro de carga y ambiente, ni comparación controlada antes y después de intervenir el rodamiento; ventilación, montaje de la sonda, carga y cambios de offset pueden influir en la serie. Por eso la asociación no aísla el mecanismo ni establece causalidad.

Tampoco hay fallas y periodos normales etiquetados para estimar sensibilidad, falsas alarmas o anticipación; los umbrales son reglas de atención, no un modelo de pronóstico. El caso queda dentro del monitoreo de condición \citep{jardine2006,cinar2020}.

\section{Amenazas a la validez y medidas para reducirlas}
\label{sec:discusion-validez}
La tabla~\ref{tab:discusion-validez} resume las amenazas que más afectan la interpretación. Las acciones propuestas son trabajo futuro; no se presentan como ensayos ya completados.

\begingroup
\small\singlespacing
\setlength{\tabcolsep}{3pt}
\begin{longtable}{@{}>{\raggedright\arraybackslash}p{2.4cm}>{\raggedright\arraybackslash}p{4.8cm}>{\raggedright\arraybackslash}p{3.7cm}>{\raggedright\arraybackslash}p{3.7cm}@{}}
\caption{Amenazas a la validez y comprobaciones necesarias.}\label{tab:discusion-validez}\\
\toprule
\textbf{Ámbito} & \textbf{Amenaza observada} & \textbf{Efecto sobre la conclusión} & \textbf{Acción necesaria} \\
\midrule\endfirsthead
\toprule
\textbf{Ámbito} & \textbf{Amenaza observada} & \textbf{Efecto sobre la conclusión} & \textbf{Acción necesaria} \\
\midrule\endhead
\bottomrule\endfoot
Medición térmica & Referencias con incertidumbre declarada de 1.5 y 2~\textdegree C; offset dependiente del Fluke; \NumeroParejas{} parejas estables de un nodo en 51.6--67.6~\textdegree C. & Concordancia local no equivale a exactitud ni generaliza a los tres nodos. & Referencia calibrada independiente, varios puntos y presupuesto de incertidumbre. \\
Trazabilidad térmica & Pocas parejas con hora y lecturas de una visita sin registro exportado. & La estadística se apoya en seis parejas de tres visitas. & Registrar hora y valor de cada lectura de referencia junto con el CSV de la sesión. \\
Validez interna & Estado de máquina sin bitácora sincronizada; falta control de carga, ambiente y montaje. & No se prueba causalidad del rodamiento ni retardo tras parada. & Registrar estado y condiciones junto con inspección e intervención. \\
Cobertura y selección & Fechas desiguales; huecos excluidos con dos reglas; hora seleccionada por buena cobertura. & No hay disponibilidad global superior a 97\,\% ni PDR directo de todo el calendario. & Ventana común explícita, contador de envíos y bitácora de energía del gateway. \\
Alcance & Nodo móvil, geometría variable, sin repeticiones por distancia y sin SNR. & 688~m es cota inferior del recorrido; no permite estimar cobertura universal. & Posiciones fijas, repeticiones y antenas documentadas. \\
Energía y tiempo & Descarga parcial y solo dos tensiones; intervalo de firmware sin energización física sincronizada. & Autonomía prolongada y recuperación completa siguen sin demostración. & Corriente por estados, descarga hasta corte y marcas temporales sincronizadas. \\
Software y datos & Resúmenes de captura desalineados con la fecha; CSV web sin verificar; 0.0 posible ante falla total de lectura. & Una pantalla o valor finito puede inducir interpretación errónea. & Validar fecha de consulta, exportación, calidad y manejo explícito de lecturas inválidas. \\
Reproducción y alcance externo & CSV primarios fuera del repositorio, PT100 sin clase de tolerancia declarada; piloto de tres nodos. & No se replica toda la evaluación ni se generaliza a otras plantas o cargas de red. & Publicar los datos primarios en una versión posterior del depósito Zenodo; completar la BOM y ampliar despliegues controlados. \\
\end{longtable}
\endgroup
