DavidSPuentesc/SmartSense-Monitoring/tesis/capitulos/10-conclusiones.tex

\chapter{Conclusiones y trabajo futuro}
\label{cap:conclusiones}

\section{Conclusiones vinculadas con los objetivos}
Cada conclusión responde a un objetivo del capítulo~\ref{cap:objetivos} y se apoya en el nivel de evidencia registrado en la tabla~\ref{tab:resultados-evidencia}, distinguiendo lo que funcionó de lo que todavía requiere validación adicional.

\begin{enumerate}
\item \textbf{Objetivo general: integración y evaluación del monitoreo local.} Se diseñó e implementó una red de \NumeroNodos{} nodos y un gateway que adquirió, transmitió, almacenó y permitió consultar la temperatura superficial de los equipos. El registro reúne \TotalMuestras{} muestras, con un tramo principal de \DuracionComunDias{} días para A y C y una ventana más larga para B, con los huecos y las fechas desiguales que detalla la sección~\ref{sec:resultados-despliegue}. Ese historial cumple el propósito de apoyar el monitoreo de condición, y el caso del succionador muestra un uso concreto: la serie térmica llevó a una inspección que después asoció el comportamiento con los rodamientos, sin que ello demuestre predicción ni causalidad.

\item \textbf{Objetivo específico 1: cadena de adquisición.} La cadena PT100 de tres hilos, MAX31865 y ESP32-C6 entregó lecturas identificadas por sensor. Las \NumeroParejas{} parejas de campo en régimen estable de la tabla~\ref{tab:resultados-parejas}, verificables contra el CSV, muestran concordancia con la referencia después del ajuste: media absoluta de \DiferenciaTermicaMedia{}, RMSE de \RMSETermico{} y máximo de \DiferenciaTermicaMaxima{}; una pareja tomada durante un arranque difiere 3.6~\textdegree C por el retardo térmico. Ninguna de estas cifras establece exactitud absoluta. El presupuesto por especificaciones acota la incertidumbre expandida en \IncertidumbreTipoB{} ($k=2$) con una sonda de clase B. El firmware maneja las fallas del conversor, pero devuelve 0.0 cuando todas las lecturas fallan, por lo que ese valor no sirve como indicador inequívoco de dato inválido (sección~\ref{sec:impl-nodo}).

\item \textbf{Objetivo específico 2: comunicación e identificación.} Las series separadas por MAC y la cadencia mediana de \PeriodoMediano{} confirman que el gateway recibe e identifica a los tres nodos. El PDR estimado por intervalos fue de \PDREstimado{} en los periodos activos, y en la hora seleccionada se recibieron 29/30, 30/30 y 30/30 tramas esperadas; ambos son indicadores de cobertura y no un conteo directo de todos los envíos. En el ensayo de alcance el enlace se mantuvo al menos hasta \DistanciaDemostrada{} con un RSSI cercano a \RSSILejano{}, cota inferior de ese recorrido (secciones~\ref{sec:resultados-pdr} y~\ref{sec:resultados-alcance}).

\item \textbf{Objetivo específico 3: gateway y dashboard.} Los archivos por sensor y fecha, las consultas del histórico y las capturas de pantalla respaldan el almacenamiento y la visualización local. Las compensaciones y las alarmas están documentadas en el capítulo~\ref{cap:implementacion}, aunque no se validaron de forma exhaustiva en todos sus escenarios. La captura del succionador dejó ver una inconsistencia entre la fecha de la curva y los indicadores de resumen, que debe corregirse. La exportación CSV desde la web sigue sin verificarse, y LittleFS funciona como medio alternativo, no como réplica automática de la microSD (secciones~\ref{sec:impl-almacenamiento} y~\ref{sec:resultados-sintesis}).

\item \textbf{Objetivo específico 4: construcción y operación de nodos.} Se construyeron \NumeroNodos{} nodos alimentados por batería y se documentaron sus conexiones, su montaje y su ciclo de adquisición, transmisión y sueño, con los esquemas y la instalación del capítulo~\ref{cap:implementacion}. El intervalo activo instrumentado de \TiempoActivo{} equivale a un ciclo de trabajo aproximado de \CicloTrabajo{} respecto del periodo nominal; ese intervalo no incluye el tiempo desde la energización ni la recuperación del servicio. Para que otro equipo reproduzca los nodos falta la clase de tolerancia de la PT100, que el vendedor no indica, y conservar la configuración leída del radio.

\item \textbf{Objetivo específico 5: evaluación y límites.} Se caracterizaron las temperaturas registradas, la cobertura, la entrega inferida de paquetes y la descarga parcial, con sus métodos y supuestos separados. La disponibilidad cruda fue de 76.0\,\%, 32.3\,\% y 75.1\,\% en las ventanas individuales, y de \DisponibilidadEnlace{} en los periodos de actividad inferida. La autonomía estimada, \AutonomiaLinealEstimada{} con el modelo lineal y \AutonomiaModeloEstimada{} con el modelo LiPo, se apoya en \DuracionDescarga{} de descarga y dos lecturas de tensión, no en meses de operación observados (sección~\ref{sec:resultados-autonomia}). Un modelo por estados con valores de ficha proyecta \AutonomiaFichaRango{}, así que la autonomía queda acotada entre mes y medio y diez meses hasta medir la corriente del nodo. Quedan pendientes la exactitud absoluta, el PDR por conteo directo, la corriente por estado, la latencia con relojes sincronizados y la recuperación completa tras un reinicio; delimitarlos es parte del resultado de la evaluación.
\end{enumerate}

\section{Trabajo futuro priorizado}
\label{sec:conclusiones-futuro}
Las siguientes actividades responden a las limitaciones observadas y definen qué evidencia deberá producir cada mejora. Las cantidades y criterios que siguen son propuestas de protocolo para estudios posteriores; no describen ensayos ejecutados ni resultados del piloto. Deberán fijarse antes de adquirir datos y conservarse también las sesiones fallidas.

\begin{enumerate}
\item \textbf{Caracterización térmica trazable.} Registrar cada lectura de referencia con su hora junto al CSV de la sesión, y obtener la clase de tolerancia de la PT100 instalada. Se proponen cinco puntos nominales (25, 35, 45, 55 y 70~\textdegree C), tres nodos, tres montajes independientes por nodo y diez parejas por punto y montaje: 450 parejas de verificación, separadas de las usadas para ajustar el offset. Iniciar cada serie cuando la referencia varíe como máximo 0.1~\textdegree C durante cinco minutos; registrar también su incertidumbre y uniformidad térmica. Construir el presupuesto de incertidumbre y evaluar el objetivo de 1~\textdegree C solo si $|\Delta T|+U\leq\SI{1}{\celsius}$ en cada punto y nodo, declarando cobertura de $U$ y contribuciones. Si no se satisface, informar la desviación sin declarar conformidad.

\item \textbf{Energía y autonomía observadas.} Registrar corriente en la entrada de los tres nodos durante al menos 100 ciclos normales por nodo, incluyendo arranque, conversión, transmisión, escucha y sueño; integrar carga por ciclo y medir por separado configuración y fallas. Proponer tres descargas completas por nodo hasta el corte operativo de 3.30~V, previa verificación de que sea compatible con la celda y su protección, con temperatura y condiciones de uso registradas. Informar duración, carga integrada, dispersión y diferencia respecto de ambos modelos; solo denominar autonomía observada al tiempo realmente medido hasta corte.

\item \textbf{PDR directo y cobertura comparable.} Programar tres ventanas de 24 horas con los tres nodos y ciclo nominal de 120~s (720 envíos nominales por nodo y ventana); usar los envíos realmente registrados como denominador. Conservar secuencia y conteos tanto en nodo como gateway, separando duplicados, reinicios y extremos de sesión. Registrar alimentación y almacenamiento del gateway. Informar PDR por nodo y ventana, además de pérdidas por bloques de una hora para mostrar su agrupación temporal. Evaluar el objetivo de PDR de al menos 95\,\% en cada ventana completa; si se satisface, limitar la conclusión a esas sesiones, sin suponer independencia entre tramas ni cobertura de otras jornadas. Calcular disponibilidad cruda y condicionada en las mismas ventanas, manteniendo visible toda exclusión.

\item \textbf{Caracterización de enlace a distancias fijas.} Documentar antenas y verificar la configuración retenida en el E220-400T22D. Proponer posiciones de 100, 300, 500 y 688~m, dos orientaciones de antena y escenarios con y sin obstrucciones, donde el acceso permita mantener la geometría. Capturar tres sesiones de 100 envíos por combinación, con posición fija y conteo directo; informar PDR, distribución de RSSI y variabilidad entre sesiones, incluso cuando no haya recepción. Registrar SNR solo si la interfaz o instrumentación lo permite. Distinguir la posición más lejana con recepción de un punto de fallo efectivamente observado; no extrapolar un alcance universal.

\item \textbf{Latencia y recuperación sincronizadas.} Utilizar una base temporal común para marcar energización, inicio de firmware, adquisición, envío, recepción y persistencia, verificando un desalineamiento de relojes no mayor de 10~ms. Separar así el intervalo instrumentado de \TiempoActivo{} del arranque físico total. Proponer 30 repeticiones por escenario (reinicio del nodo, reinicio del gateway y recuperación del enlace) y nodo; informar mediana, percentil 95, máximo y fallos. Evaluar por separado el criterio de recuperación de hasta 120~s sobre todas las repeticiones, sin asignar un límite de latencia no requerido ni convertirlo en garantía fuera del ensayo.

\item \textbf{Integridad de la interfaz y del dato.} Corregir la actualización de estadísticas para que correspondan a la fecha consultada, verificar exportación CSV y programar la conservación de datos antes de la rotación. Añadir un estado explícito de lectura válida y conservar cambios de offset y configuración. Comprobar alarmas y persistencia ante pérdida de alimentación y fallas del medio, documentando qué funciones de respaldo realmente se ejecutan.

\item \textbf{Seguimiento de condición con contexto operacional.} Incorporar una bitácora sincronizada de marcha, parada, carga, ambiente e intervenciones y repetir observaciones en varios equipos. Para evaluar diagnóstico o pronóstico se requerirá una población de condiciones normales y anómalas etiquetadas, criterios definidos de alarma y evaluación de falsos positivos, sensibilidad y anticipación. El caso actual puede orientar esas preguntas, pero no proporciona por sí solo esas métricas.

\item \textbf{Publicación reproducible.} La versión \texttt{v1.0-tesis} del repositorio ya está archivada en Zenodo con el DOI \DOIZenodo{}. Las versiones siguientes deben incorporar la clase de tolerancia de la PT100, los CSV y registros primarios que la empresa autorice, un diccionario de datos y scripts que no dependan de rutas personales.
\end{enumerate}

\section{Cierre}
SmartSense conserva y permite consultar las tendencias térmicas de los equipos en una red local. El piloto aportó evidencia de que la cadena completa funciona y dejó definidas las pruebas directas que faltan para cerrar su caracterización metrológica, energética y de comunicación.
