DavidSPuentesc/SmartSense-Monitoring/tesis/capitulos/05-marco-referencia.tex

\chapter{Marco de referencia}
\label{cap:marco-referencia}

\section{Temperatura superficial y monitoreo de condición}
Lo que mide SmartSense es la temperatura de la superficie en el punto de contacto de la sonda, que no es la del aire, la del devanado ni la de otros puntos del mismo equipo. El montaje, la transferencia de calor hacia la sonda y el ambiente condicionan la lectura y su tiempo de respuesta; por eso, comparar dos registros exige conservar la ubicación y anotar los cambios de montaje o de operación.

El monitoreo de condición usa observaciones del equipo para estudiar su estado; el diagnóstico identifica una condición o falla y el pronóstico anticipa su evolución \citep{jardine2006}. Tener una serie no es lo mismo que demostrar una causa o predecir una falla. Las alarmas de este proyecto comparan la lectura con un umbral configurado; no hay un modelo entrenado, una clasificación de fallas ni una estimación de vida útil restante.

\section{RTD, PT100 y referencia normativa}
\label{sec:marco-rtd}
Un detector resistivo de temperatura (RTD) aprovecha la variación de resistencia de un material con la temperatura. La designación PT100 corresponde a un elemento de platino con resistencia nominal de \SI{100}{\ohm} a \SI{0}{\celsius}. La norma IEC~60751 establece la relación resistencia--temperatura y requisitos para sensores y termómetros industriales de platino \citep{iec60751}. La relación no es exactamente lineal; el algoritmo de conversión debe corresponder al elemento utilizado y al intervalo de trabajo.

La norma no certifica una sonda concreta: la clase de tolerancia, el rango utilizable y el encapsulado dependen del componente comprado y de su documentación. Como el vendedor de la sonda instalada, de marca ZUIDID, no indica su clase de tolerancia (sección~\ref{sec:impl-nodo}), este trabajo no le atribuye conformidad de clase~B; la asume como hipótesis declarada en el presupuesto de incertidumbre (sección~\ref{sec:fund-incertidumbre}). El rango teórico del platino tampoco se extiende al conjunto, porque el cable, el montaje y la electrónica pueden limitarlo.

\subsection{Conexión de tres hilos}
En una conexión de dos hilos la resistencia de los cables se suma a la del elemento. La de tres hilos compensa esa contribución suponiendo que los conductores compensados tienen resistencias iguales; cualquier desequilibrio deja un residuo \citep{max31865}.

Por eso en SmartSense conviene mantener longitud, sección y uniones iguales y revisar los contactos. El contacto térmico de la sonda magnética con la carcasa es otro asunto: la compensación eléctrica no corrige el retardo térmico ni la diferencia entre el punto de contacto y el punto que observa otro instrumento.

\subsection{Conversión MAX31865}
El MAX31865 convierte la razón entre la resistencia RTD y una resistencia de referencia externa mediante un convertidor de 15 bits. Admite configuraciones de dos, tres y cuatro hilos, interfaz SPI y detección de fallas de conexión \citep{max31865}. Para un código RTD válido $n$, excluido el bit de falla, la relación nominal es
\begin{equation}
R_{\mathrm{RTD}}=\frac{n}{2^{15}}R_{\mathrm{ref}}.
\label{eq:marco-rtd-digital}
\end{equation}
El firmware convierte esa resistencia a temperatura. El valor y la estabilidad de $R_{\mathrm{ref}}$ entran directamente en la conversión, la resolución digital no es la exactitud del sistema, y el estado de falla se comprueba antes de aceptar cada lectura (sección~\ref{sec:fund-calculos}).

\section{Microcontrolador y operación local}
La placa XIAO ESP32-C6 integra el microcontrolador y las interfaces para los periféricos; su documentación describe conexiones, alimentación y modos de bajo consumo \citep{xiaoc6}. En el nodo, SPI enlaza el acondicionador y UART el radio; el nodo identifica cada medición y organiza su ciclo de actividad. El gateway recibe, conserva y presenta los datos, y atiende a los clientes por Wi-Fi local.

Guardar los datos cerca de la fuente sigue la idea de la computación en el borde \citep{shi2016}: no hace falta un servicio remoto para consultar el historial, pero el registro pasa a depender del gateway, de su reloj y de su medio de almacenamiento. Un archivo persistente puede consultarse aunque el nodo aparezca desconectado en ese momento.

\section{LoRa y LoRaWAN}
\label{sec:marco-lora}
LoRa es una técnica de modulación por espectro ensanchado mediante señales de frecuencia variable. Sus parámetros físicos establecen compromisos entre tasa de datos, tiempo de transmisión y capacidad de recepción \citep{semtech2015}. LoRaWAN añade reglas de acceso y una arquitectura con dispositivos, gateways y servidor de red sobre esa capa física \citep{augustin2016}. Un enlace que utiliza LoRa no es automáticamente una red LoRaWAN.

SmartSense utiliza radios E220 por UART y comunicación punto a punto hacia un gateway, con identificadores y mensajes de aplicación propios. El módulo instalado en nodos y gateway es el E220-400T22D, basado en el LLCC68, que trabaja entre 410.125 y 493.125~MHz con hasta 22~dBm y una sensibilidad típica de $-127$~dBm a 2.4~kbps según su manual \citep{e220manual}. Las condiciones de radio efectivamente usadas se obtienen del firmware y de los registros del ensayo (sección~\ref{sec:impl-comunicacion}).

Con varios emisores en el mismo canal las transmisiones pueden superponerse; el resultado con \NumeroNodos{} nodos no dice nada sobre redes mayores, cuya escalabilidad depende de la carga y de los parámetros elegidos, como estudian \citet{bor2016}.

\subsection{PDR y disponibilidad}
\label{sec:marco-pdr-disponibilidad}
La tasa de entrega de paquetes (PDR, por sus siglas en inglés) compara los paquetes válidos recibidos con los enviados dentro de una misma ventana:
\begin{equation}
\mathrm{PDR}=\frac{N_{\mathrm{recibidos}}}{N_{\mathrm{enviados}}}\times100\text{\%}.
\label{eq:marco-pdr}
\end{equation}
Hay que definir cómo se tratan duplicados, reinicios y retransmisiones; un contador de secuencia da evidencia directa si se conoce su comportamiento ante esos eventos. Cuando solo hay marcas de llegada, el número de envíos se infiere de un periodo supuesto y el resultado es un PDR estimado: un intervalo largo puede deberse a pérdida, a apagado o a un cambio de cadencia, y el archivo de recepción no distingue entre ellos.

La disponibilidad describe en qué medida el servicio o los datos estuvieron accesibles en una ventana. En el análisis de SmartSense, la disponibilidad de datos se operacionaliza como muestras recibidas frente a muestras esperadas según el periodo de referencia:
\begin{equation}
A_{\mathrm{datos}}=\frac{N_{\mathrm{muestras}}}{N_{\mathrm{esperadas}}}\times100\text{\%}.
\label{eq:marco-disponibilidad}
\end{equation}
La disponibilidad cruda usa toda la ventana observada; la disponibilidad del enlace en periodos activos excluye los intervalos clasificados como paradas del gateway y depende de ese criterio. Responden a preguntas distintas: la primera dice cuánto historial tuvo el usuario; la segunda, cómo se comportó el enlace cuando el gateway registraba. Identificar paradas por huecos simultáneos es una inferencia que conviene confrontar con registros de planta, como se hace en la cronología de la sección~\ref{sec:resultados-cronologia}.

\subsection{RSSI, SNR y alcance}
RSSI representa un indicador de potencia recibida, normalmente expresado en dBm. SNR expresa la relación entre la potencia de señal y de ruido en dB. Son magnitudes diferentes: no puede obtenerse SNR a partir de RSSI sin información adicional sobre el ruido. El análisis físico de LoRa distingue estos parámetros y su relación con la recepción \citep{augustin2016}.

La instrumentación debe decir qué magnitud entrega el módulo y cómo se convierte su código. Un registro de RSSI no da el SNR ni un alcance universal, porque antenas, obstáculos, orientación y posición cambian el resultado; si el enlace sigue operativo al terminar una prueba de distancia, el último punto es una cota inferior del alcance.

\section{Sueño profundo, ciclo de trabajo y energía}
\label{sec:marco-energia}
El sueño profundo reduce la actividad del microcontrolador entre adquisiciones, pero el consumo del nodo también incluye el radio, el acondicionador, los reguladores, el divisor y las fugas \citep{xiaoc6}; la estrategia energética tiene que decir qué periféricos quedan alimentados y cuánto dura cada estado.

Si $t_a$ es el tiempo activo y $T$ el periodo completo, el ciclo de trabajo del nodo se expresa como $D=t_a/T$. Para un modelo de dos estados, una corriente media aproximada es
\begin{equation}
I_{\mathrm{media}}=D I_a+(1-D)I_s,
\label{eq:marco-corriente-media}
\end{equation}
donde $I_a$ e $I_s$ son las corrientes medias activa y de reposo del nodo completo. El ciclo activo del microcontrolador no es el ciclo de ocupación del canal, que depende solo del tiempo de emisión de radio.

La autonomía se aproxima dividiendo la capacidad utilizable entre la corriente media, lo que exige conocer la capacidad efectiva, el corte de tensión, las pérdidas y las condiciones de descarga. Inferir meses a partir de una caída de tensión de pocos días requiere además un modelo de estado de carga; en SmartSense la evidencia energética es una \EstadoAutonomia{}.

\section{Concordancia de campo, error e incertidumbre}
\label{sec:marco-metrologia}
Según el vocabulario metrológico, calibrar establece relaciones entre indicaciones y valores de referencia con sus incertidumbres; ajustar modifica la respuesta de un instrumento. Error de medición e incertidumbre son conceptos diferentes: el primero es una diferencia respecto de un valor de referencia y la segunda caracteriza la dispersión atribuible al mensurando \citep{jcgm2012}.

En una comparación pareada de campo puede calcularse
\begin{equation}
\Delta T_i=T_{\mathrm{SS},i}-T_{\mathrm{ref},i},
\qquad
\mathrm{MAE}_{\mathrm{ref}}=\frac{1}{n}\sum_{i=1}^{n}|\Delta T_i|.
\label{eq:marco-concordancia}
\end{equation}
Estas diferencias describen la concordancia con el instrumento usado. Si ese instrumento sirvió también para ajustar el offset, la comparación no es una validación independiente; y una referencia infrarroja y una PT100 de contacto observan áreas distintas y responden de forma diferente a la emisividad, al montaje y a los transitorios, aunque sus lecturas coincidan.

Un presupuesto de incertidumbre necesita un modelo de medición e información sobre las fuentes que influyen en el resultado. Para entradas independientes $x_j$, la forma básica de combinación es
\begin{equation}
u_c^2(y)=\sum_j\left(\frac{\partial f}{\partial x_j}\right)^2u^2(x_j),
\label{eq:marco-incertidumbre}
\end{equation}
con términos de covarianza si las entradas están correlacionadas \citep{jcgm2008}. Las contribuciones son la referencia, la resistencia de referencia, los conductores, la repetibilidad y el montaje térmico. Sin una caracterización trazable, el presupuesto se construye a partir de las especificaciones (sección~\ref{sec:fund-incertidumbre}) y el resultado térmico del proyecto se presenta como \EstadoTemperatura{}.
