DavidSPuentesc/SmartSense-Monitoring/tesis/capitulos/01-introduccion.tex

\chapter{Introducción}
\label{cap:introduccion}

La temperatura superficial de un equipo industrial dice más cuando se conoce cómo cambia en el tiempo y bajo qué condiciones de operación. Una lectura aislada informa del estado del punto medido en ese instante, pero no de los ciclos de calentamiento, las recuperaciones ni los cambios ocurridos entre una inspección y la siguiente. En la planta piloto que motivó este proyecto hacía falta conservar esa información y poder consultarla por equipo sin que un operario tuviera que estar junto al instrumento.

Las redes de sensores inalámbricos reparten la adquisición, el procesamiento y la comunicación entre dispositivos distribuidos, y su diseño depende del entorno, de la energía disponible y de lo que exija la aplicación \citep{akyildiz2002,yick2008}. En el registro periódico de temperatura cada medición ocupa pocos bytes, así que importa más la continuidad del historial que la velocidad de transmisión, y las comunicaciones de baja potencia y largo alcance encajan con ese tipo de tráfico \citep{centenaro2016}. Elegir la radio es solo una parte del problema: también hay que identificar cada nodo, conservar las muestras e interpretar los periodos en que no se recibe nada.

Las arquitecturas propuestas para la Industria 4.0 conectan el proceso físico con su representación digital \citep{lee2015}. En SmartSense esa conexión se reduce a algo concreto: convertir la temperatura de una superficie en una serie que se pueda consultar. Procesar y guardar los datos cerca de donde se producen, como plantea la computación en el borde \citep{shi2016}, permite que el almacenamiento y la visualización se queden en la instalación. La operación local fue una decisión de arquitectura: el historial debe poder consultarse desde la red del gateway aunque no haya conexión permanente a Internet.

El trabajo se sitúa en el monitoreo de condición. Adquirir datos es el primer paso para estudiar el estado de una máquina; diagnosticar la causa de una falla o pronosticar la vida útil restante exige métodos y evidencias adicionales \citep{jardine2006}. Por eso un incremento térmico en una serie no basta para establecer la causa de una falla ni la vida útil restante de un componente. Esa distinción orienta la implementación y la lectura de los resultados.

El prototipo consta de \NumeroNodos{} nodos alimentados por batería, cada uno con una sonda PT100 de tres hilos, un conversor MAX31865, un microcontrolador ESP32-C6 y un radio E220, y de un gateway que conserva las muestras y las presenta en su pantalla y en un dashboard web local. El piloto reunió \TotalMuestras{} muestras: los nodos A y C cubren un tramo de \DuracionComunDias{} días, del 8 de mayo al 9 de junio de 2026, y el nodo B va del 10 de mayo al 20 de julio, de modo que las comparaciones entre los tres se hacen sobre el tramo en que coinciden. Con estos datos se examina el comportamiento térmico y la continuidad de la recepción; las pruebas complementarias aportan la concordancia de campo con un termómetro de referencia y las estimaciones de autonomía, cada una con los límites de su método.

El documento presenta primero el problema, los objetivos, los antecedentes y los conceptos en que se apoya la solución; luego el método, la construcción, los resultados y sus limitaciones. Las conclusiones contrastan cada objetivo con la evidencia obtenida, y los anexos indican dónde están los archivos, los cálculos y las pruebas del proyecto.

La contribución de SmartSense es integrar adquisición con RTD industrial, comunicación LoRa punto a punto, alimentación autónoma y un dashboard local en una plataforma abierta, y evaluar su funcionamiento conjunto en un despliegue piloto. El aporte está en la integración documentada y en la evaluación de sus resultados dentro de su contexto. El sistema apoya el monitoreo de condición; no implementa ni valida un algoritmo de mantenimiento predictivo.
