DavidSPuentesc/SmartSense-Monitoring/Correcciones/Correciones para articulo hardware x.docx

Cambiar donde dice "desarrollamos un sistema de mantenimiento predictivo".

Por este párrafo:

Existe una necesidad de monitorización térmica continua y reproducible de equipos industriales que puede ser difícil de satisfacer con soluciones comerciales cerradas o con mediciones puntuales. SmartSense propone una plataforma abierta, económica y local para adquirir, transmitir, almacenar y visualizar temperatura superficial mediante PT100 y LoRa. Se demuestra su potencial mediante la construcción reproducible y un despliegue industrial de 32 días que caracteriza la disponibilidad de comunicación, cadencia de adquisición y comportamiento térmico.

Considero que no se debe hablar de mantenimiento predictivo o no se si se equivocaron es preventivo.

Algunas cosas a tener en cuenta para agregar:

¿Cuál es su precisión absoluta?, ¿Es superior a una solución comercial?

Ojo con esto:

Algo positivo que muchos artículos no hacen: reconoce explícitamente la limitación.

Dice que las lecturas frente al Fluke 62 MAX estuvieron dentro de ±0,4 °C, pero que el mismo instrumento se utilizó para ajustar el offset y que su exactitud es ±1,5 °C. Por tanto se reconoce que no es una validación independiente. Esto esta bien.

El problema es que luego aparece:

"Temperature readings agreed ... within ±0.4 °C"

y posteriormente:

"a strict ≤1 °C validation requires a calibrated contact reference (planned)."

Esto genera una contradicción narrativa:

Se presenta un desempeño de ±0,4 °C, pero reconoce que todavía no puede demostrarlo como exactitud metrológica.

Pienso que en vez de hablar del precio de 35USD se debe comparar la información de esta forma: La comparación debería ser una tabla y no se va tanto al costo.

Característica | SmartSense | WISE-2410 | Diferencia
Open hardware | Sí | No | SmartSense
PT100 | Sí | No / sensor propio | SmartSense
LoRa | Sí | LoRaWAN | Diferente
Vibration | No | Sí | WISE
Local storage | Sí | ...
Cloud dependency | No | Ecosistema comercial
IP rating | ¿? | IP66 | SmartSense pendiente
Battery characterization | Pendiente | 2 años especificados | WISE
Cost | ~$35/node incremental | Commercial

Si responde a esto nos da mayor fuerza para presentarlo y complementa el proyecto que vamos a presentar no solo en hardware x sino en ecci:

Y después preguntaría:

1. ¿Cuál es la exactitud real?
2. ¿Cuál es la autonomía real?
3. ¿Cuál es la distancia de comunicación?
4. ¿Cuál es la potencia de transmisión?
5. ¿Cuál es el RSSI/SNR?
6. ¿Cómo se calculó exactamente el packet loss?
7. ¿Qué clase de PT100 se utilizó?
8. ¿Puede reproducirse exactamente el sistema?
9. ¿Dónde están los archivos?
10. ¿Por qué se denomina predictive maintenance?
11. ¿Qué demuestra que la anomalía térmica precedió al fallo?
12. ¿Cuál es la ventaja cuantitativa frente a WISE-2410?
13. ¿Qué significa exactamente "long-term"?
14. ¿Qué ocurre después de 30 días de almacenamiento?
15. ¿Cuál es el consumo real?
