DavidSPuentesc/SmartSense-Monitoring/figuras/val-cobertura.pdf

May 09 | May 13 | May 17 | May 21 | May 25 | May 29 Jun 01 | Jun 05 | Jun 09
| | | | Date

Node C

Node B

Node A

Data coverage — outages are simultaneous across nodes (gateway down)
