DavidSPuentesc/SmartSense-Monitoring/figuras/adjuntos_mediciones/1000089950.jpg

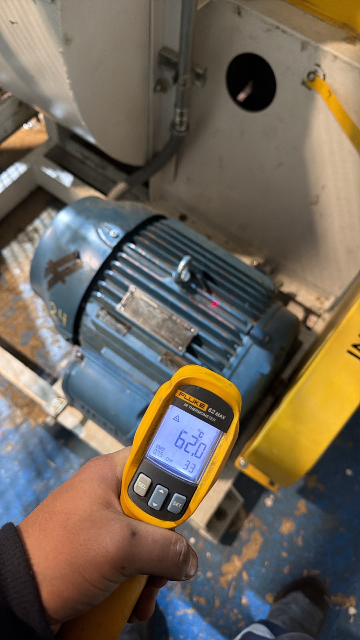
figuras/adjuntos_mediciones/1000089950.jpg
