DavidSPuentesc/SmartSense-Monitoring/figuras/adjuntos_mediciones/1000089952.jpg

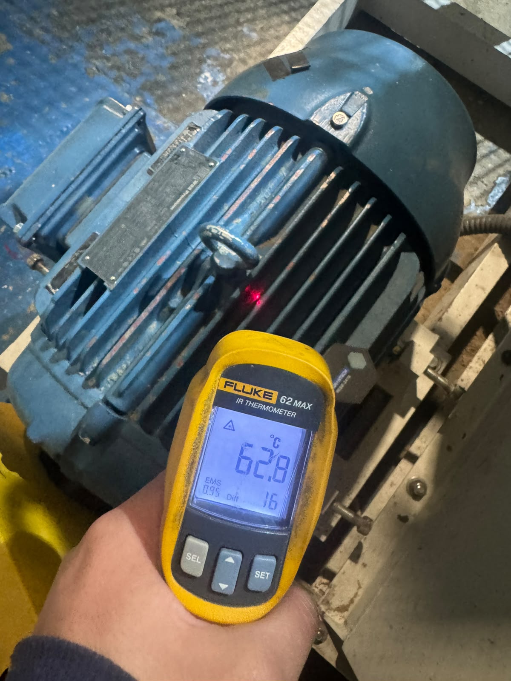
figuras/adjuntos_mediciones/1000089952.jpg
