DavidSPuentesc/SmartSense-Monitoring/figuras/adjuntos_mediciones/1000089954.jpg

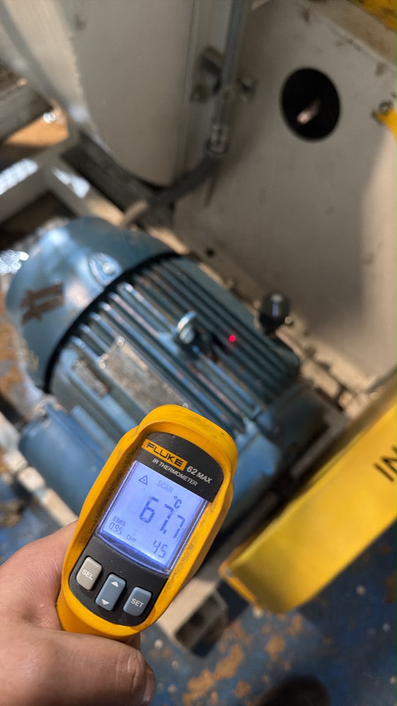
figuras/adjuntos_mediciones/1000089954.jpg
