DavidSPuentesc/SmartSense-Monitoring/figuras/adjuntos_mediciones/1000089957.jpg

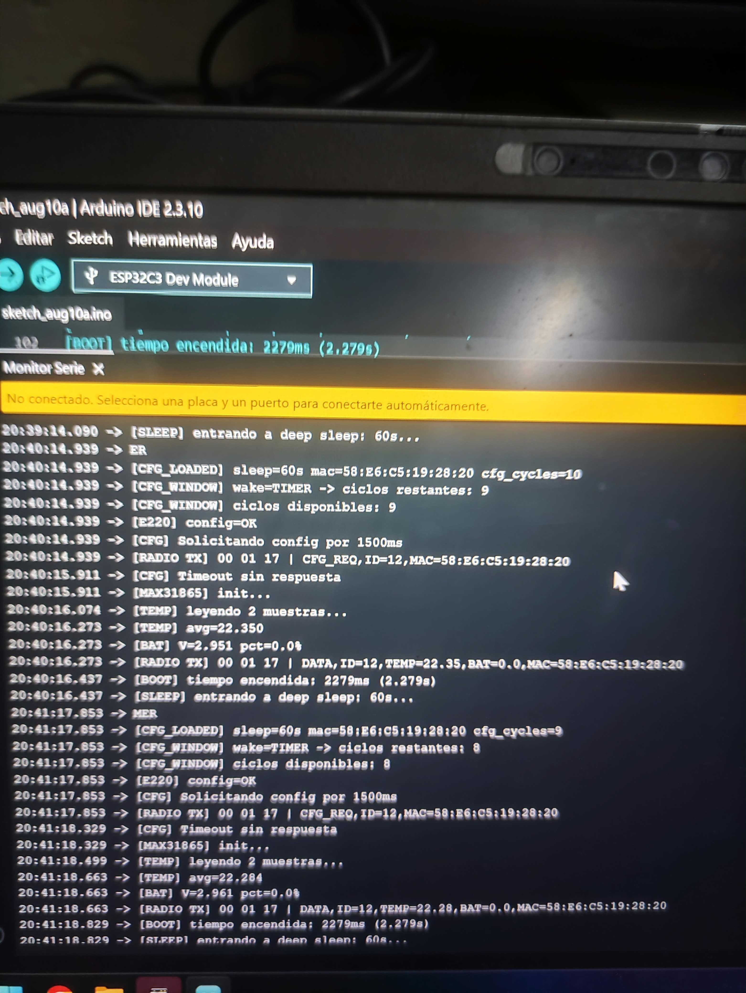
figuras/adjuntos_mediciones/1000089957.jpg
