DavidSPuentesc/SmartSense-Monitoring/figuras/adjuntos_mediciones/1000089958.jpg

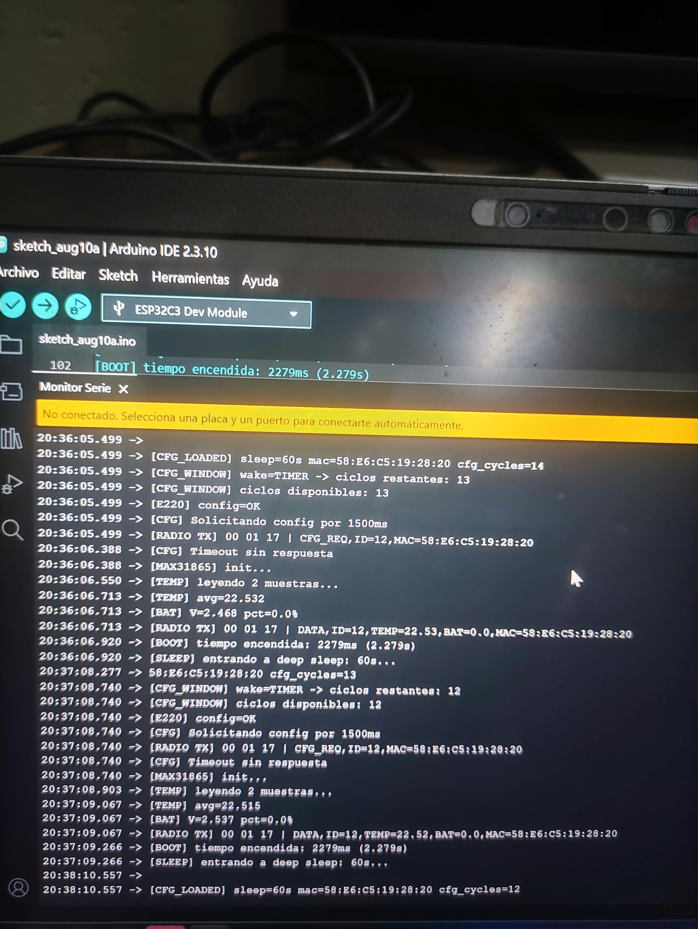
figuras/adjuntos_mediciones/1000089958.jpg
