DavidSPuentesc/SmartSense-Monitoring/figuras/adjuntos_mediciones/1000089959.jpg

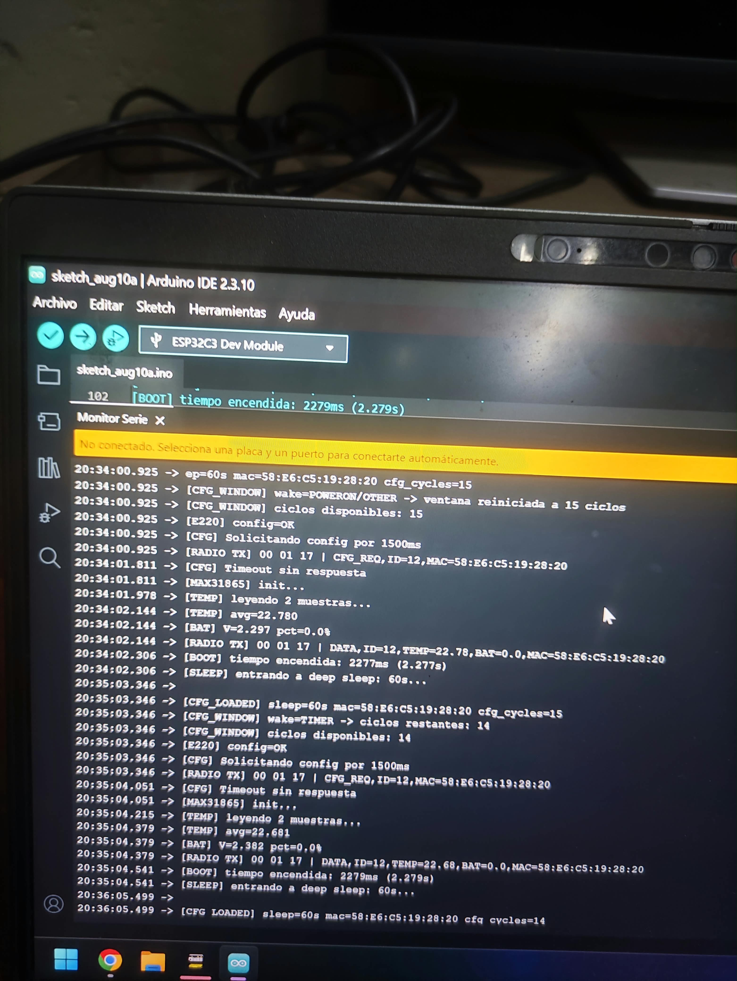
figuras/adjuntos_mediciones/1000089959.jpg
