DavidSPuentesc/SmartSense-Monitoring/figuras/adjuntos_mediciones/1000089963.jpg

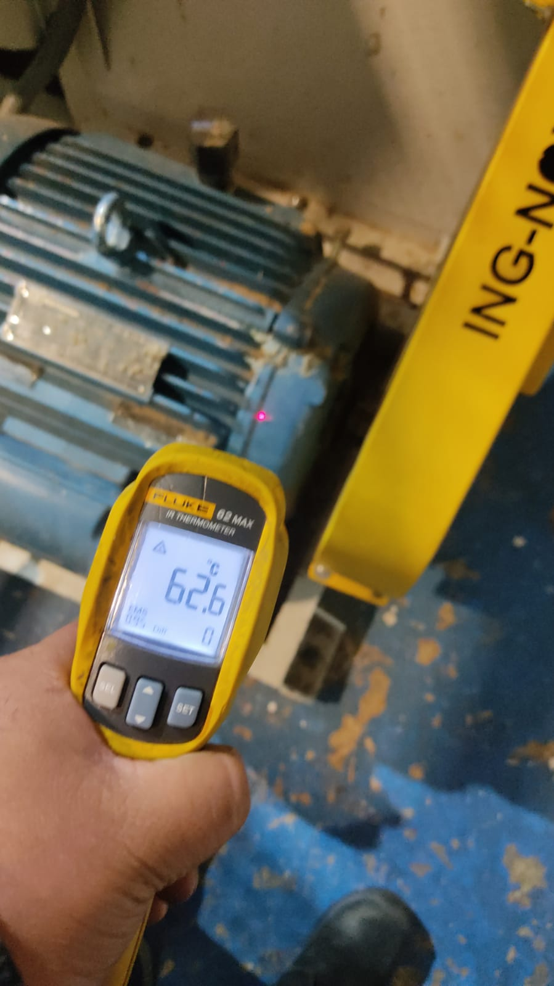
figuras/adjuntos_mediciones/1000089963.jpg
