DavidSPuentesc/SmartSense-Monitoring/figuras/adjuntos_mediciones/1000089972.jpg

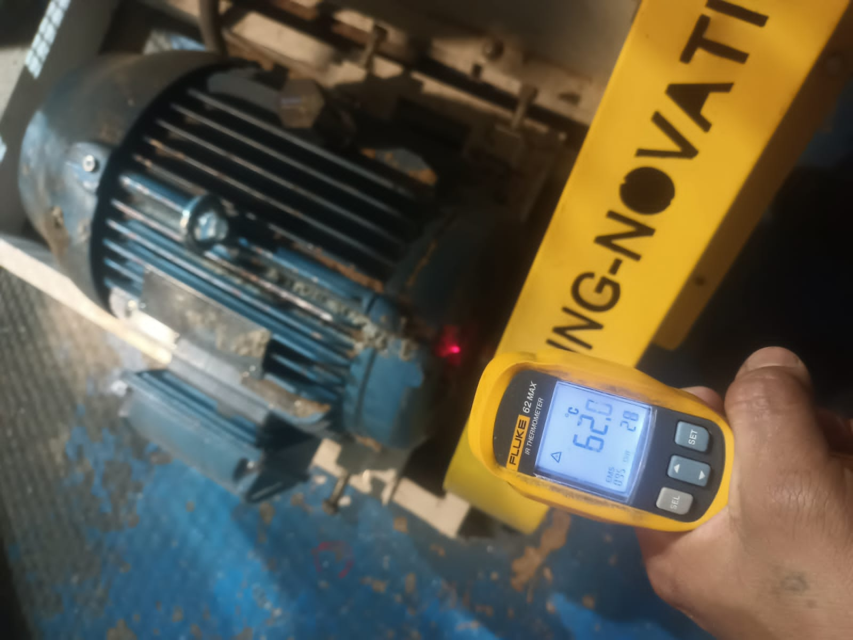
figuras/adjuntos_mediciones/1000089972.jpg
