DavidSPuentesc/SmartSense-Monitoring/figuras/adjuntos_mediciones/1000089975.jpg

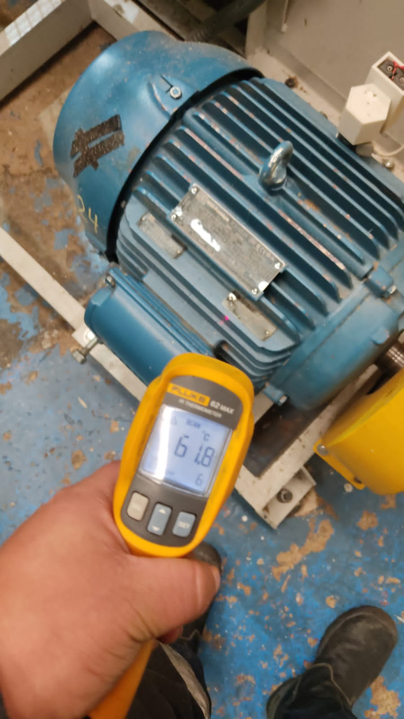
figuras/adjuntos_mediciones/1000089975.jpg
