DavidSPuentesc/SmartSense-Monitoring/figuras/adjuntos_mediciones/1000089978.jpg

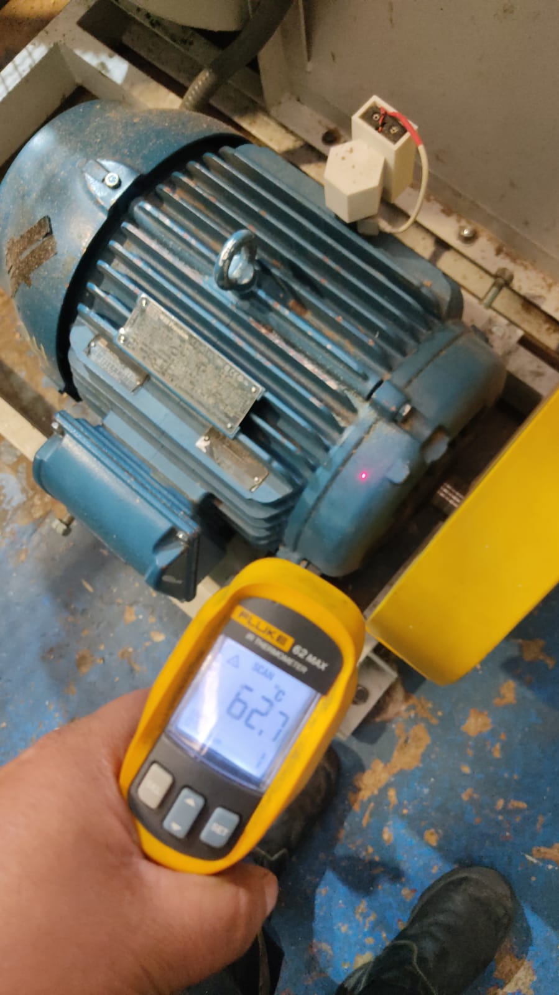
figuras/adjuntos_mediciones/1000089978.jpg
