DavidSPuentesc/SmartSense-Monitoring/figuras/adjuntos_mediciones/1000089981.jpg

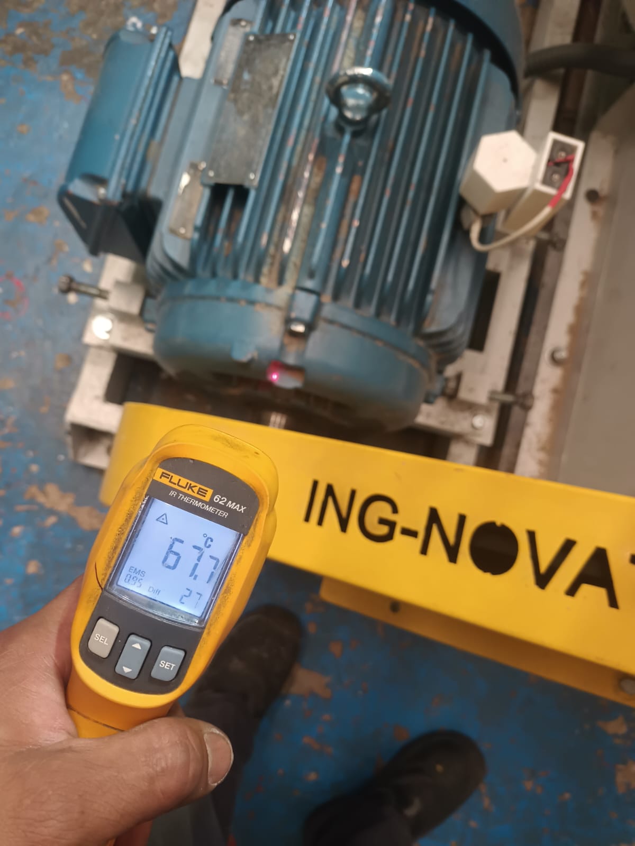
figuras/adjuntos_mediciones/1000089981.jpg
