DavidSPuentesc/SmartSense-Monitoring/figuras/adjuntos_mediciones/1000089984.jpg

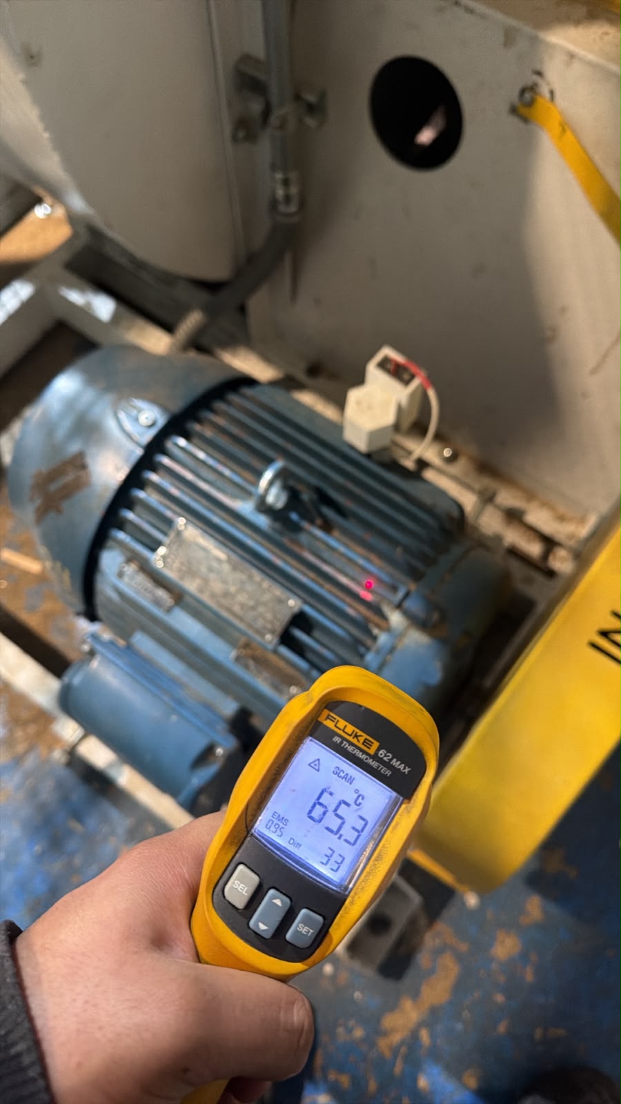
figuras/adjuntos_mediciones/1000089984.jpg
