DavidSPuentesc/SmartSense-Monitoring/figuras/adjuntos_mediciones/1000089986.jpg

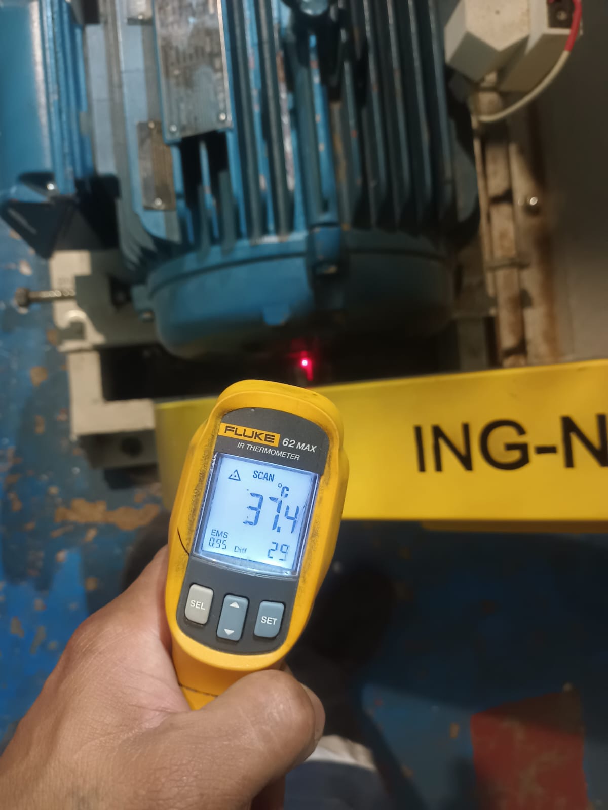
figuras/adjuntos_mediciones/1000089986.jpg
