DavidSPuentesc/SmartSense-Monitoring/figuras/adjuntos_mediciones/1000089989.jpg

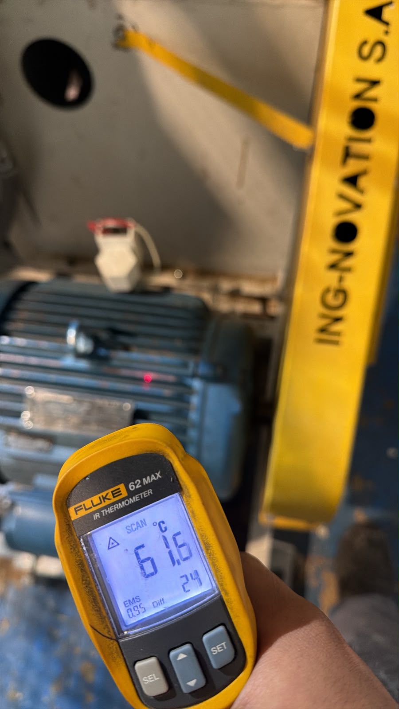
figuras/adjuntos_mediciones/1000089989.jpg
