DavidSPuentesc/SmartSense-Monitoring/figuras/adjuntos_mediciones/1000089991.jpg

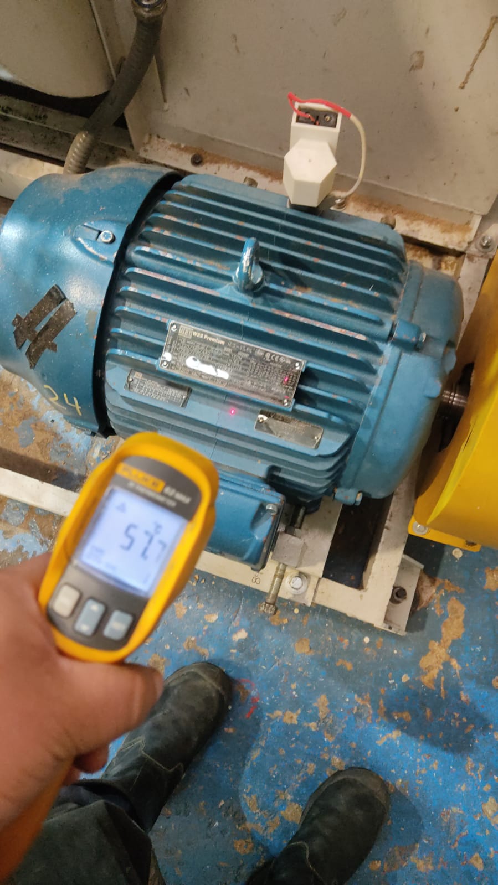
figuras/adjuntos_mediciones/1000089991.jpg
