DavidSPuentesc/SmartSense-Monitoring/figuras/adjuntos_mediciones/1000090009.jpg

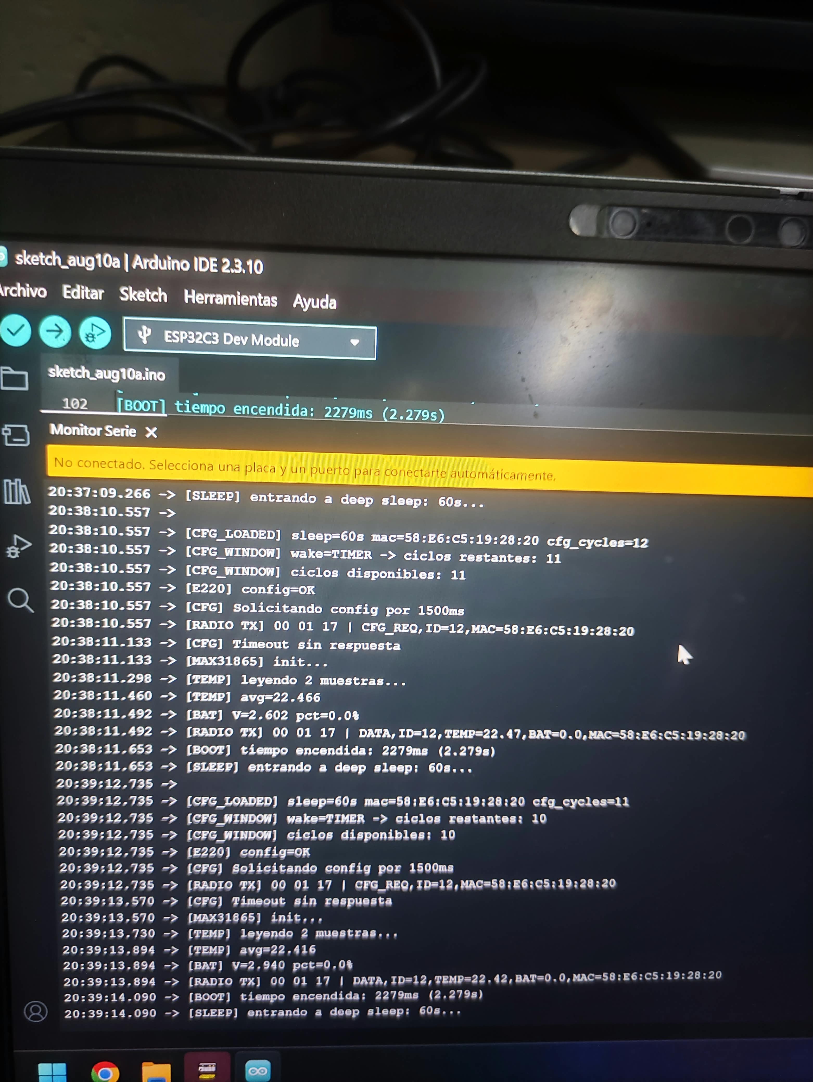
figuras/adjuntos_mediciones/1000090009.jpg
