DavidSPuentesc/SmartSense-Monitoring/figuras/adjuntos_mediciones/1000090017.jpg

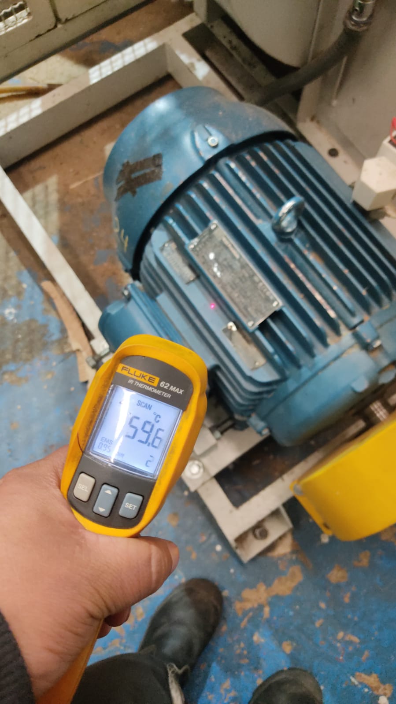
figuras/adjuntos_mediciones/1000090017.jpg
