DavidSPuentesc/SmartSense-Monitoring/figuras/arquitectura-detalle.png

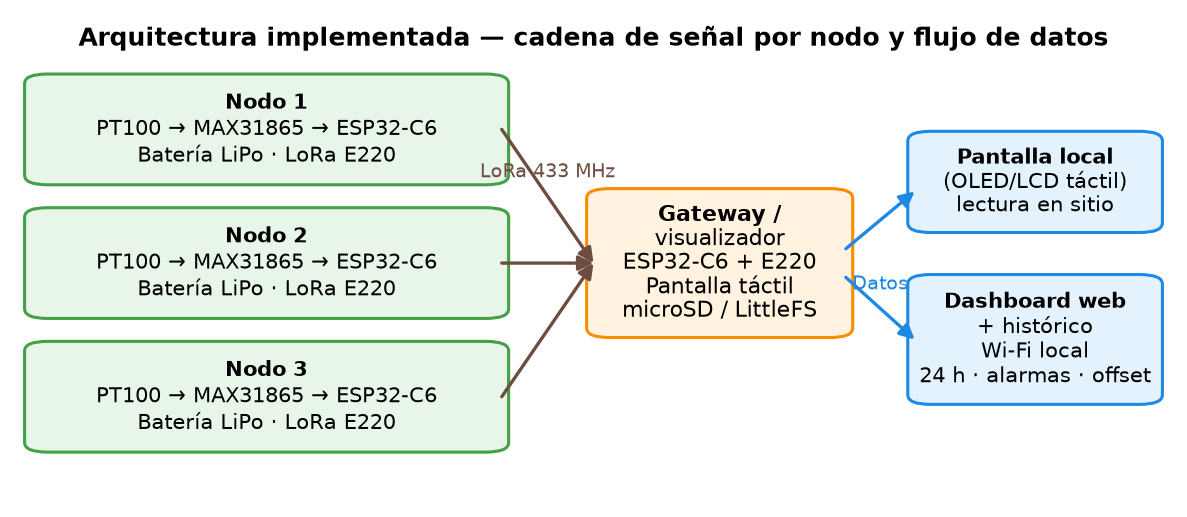
figuras/arquitectura-detalle.png
