DavidSPuentesc/SmartSense-Monitoring/figuras/autonomia-ciclo.png

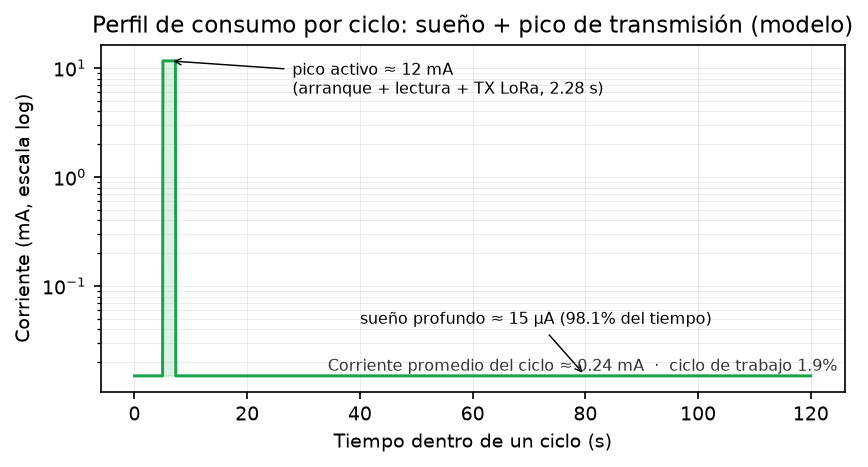
figuras/autonomia-ciclo.png
