DavidSPuentesc/SmartSense-Monitoring/figuras/autonomia-descarga.png

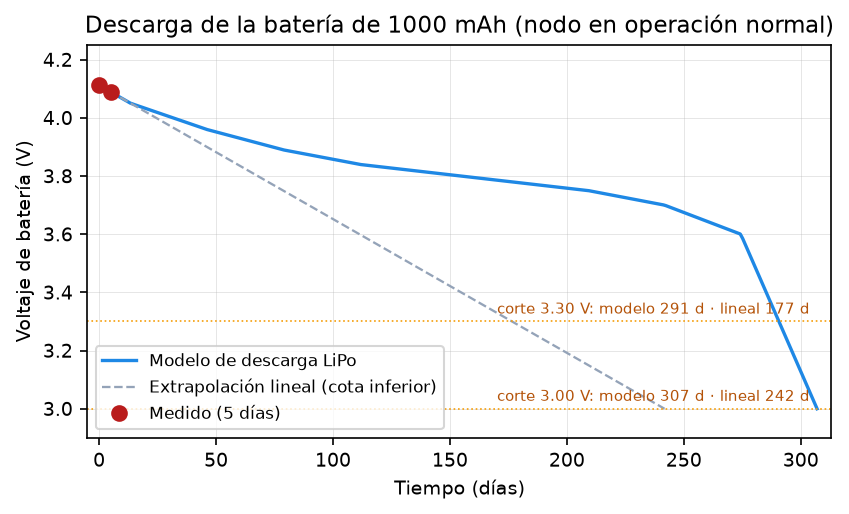
figuras/autonomia-descarga.png
