DavidSPuentesc/SmartSense-Monitoring/figuras/comparacion-sensores.png

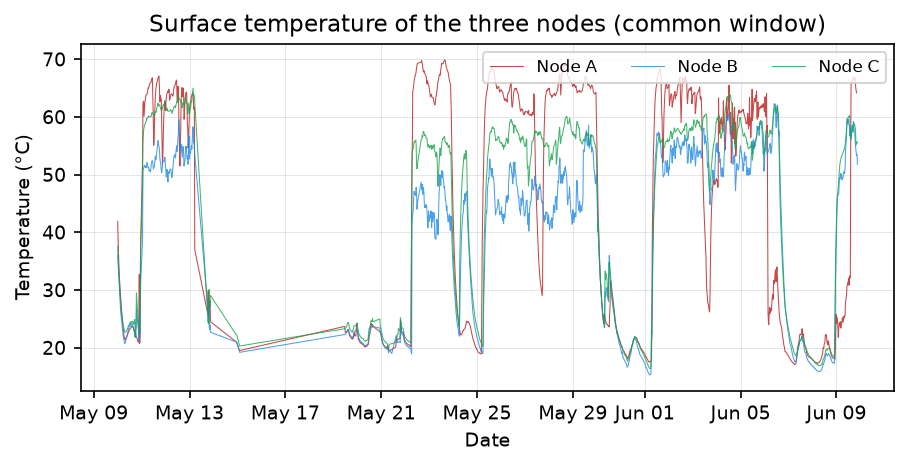
figuras/comparacion-sensores.png
