DavidSPuentesc/SmartSense-Monitoring/figuras/distribucion-temperatura.png

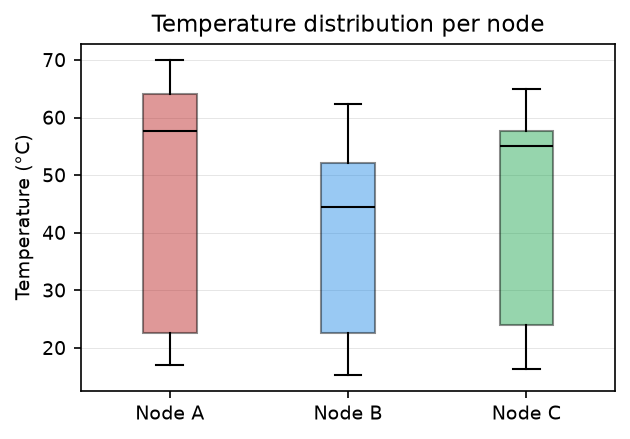
figuras/distribucion-temperatura.png
