DavidSPuentesc/SmartSense-Monitoring/figuras/evidencias/nodo-antena.jpg

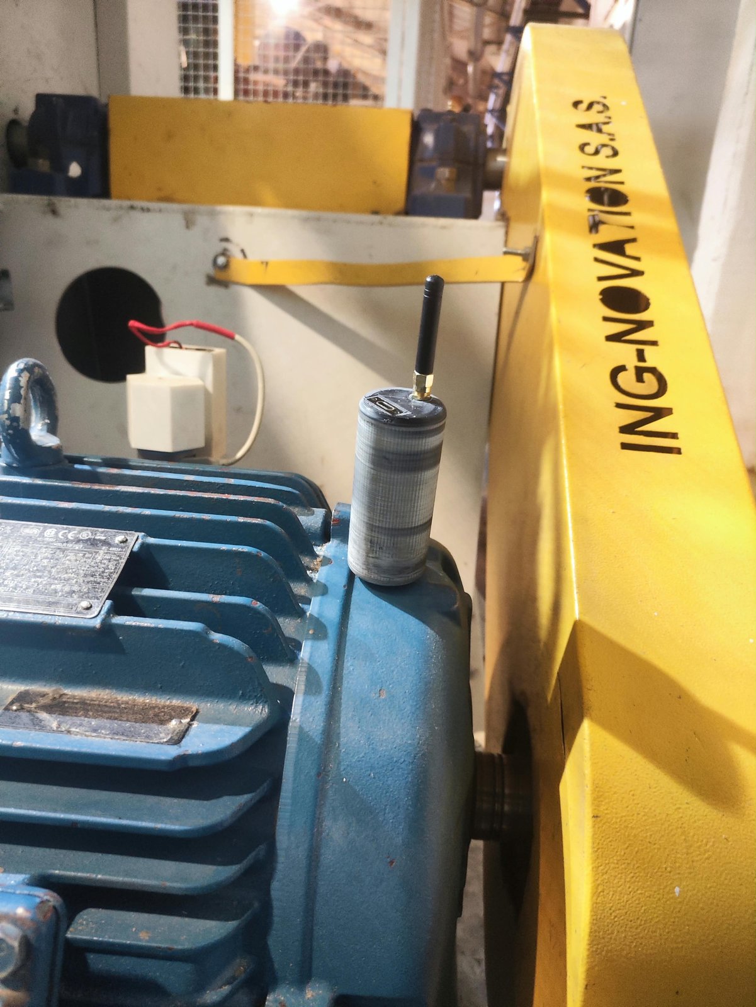
figuras/evidencias/nodo-antena.jpg
