DavidSPuentesc/SmartSense-Monitoring/figuras/evidencias/WhatsApp Unknown 2026-08-20 at 7.50.18 AM/WhatsApp Image 2026-08-19 at 10.00.28 PM.jpeg

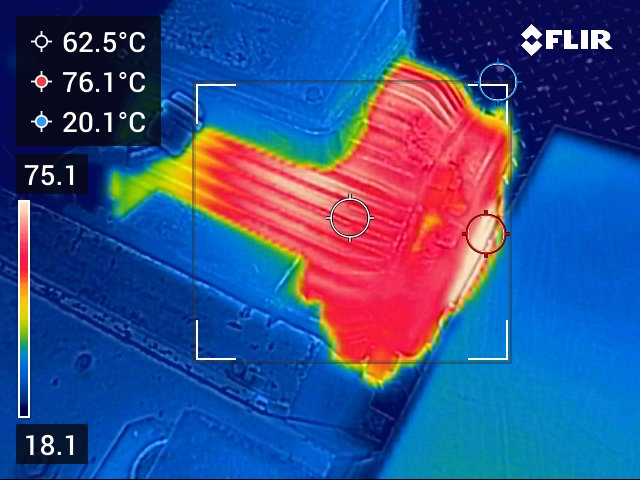
figuras/evidencias/WhatsApp Unknown 2026-08-20 at 7.50.18 AM/WhatsApp Image 2026-08-19 at 10.00.28 PM.jpeg
