DavidSPuentesc/SmartSense-Monitoring/figuras/Fotos diseño final/adjuntos/1000099060.jpg

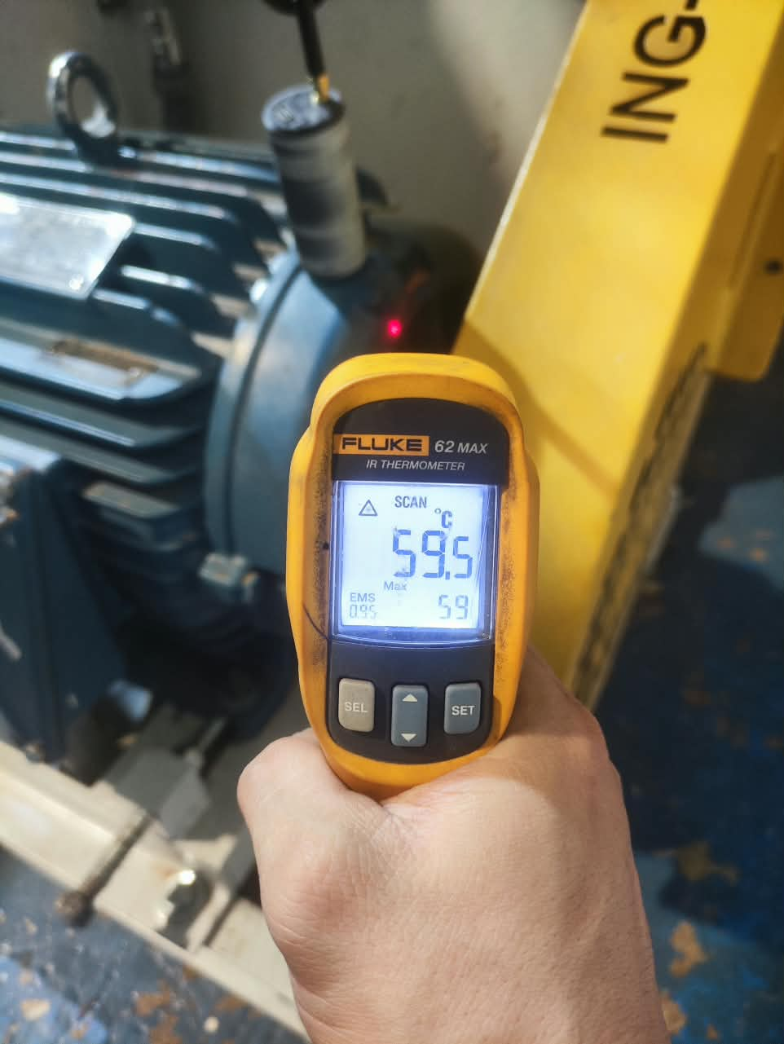
figuras/Fotos diseño final/adjuntos/1000099060.jpg
