DavidSPuentesc/SmartSense-Monitoring/figuras/Fotos diseño final/adjuntos/1000099062.jpg

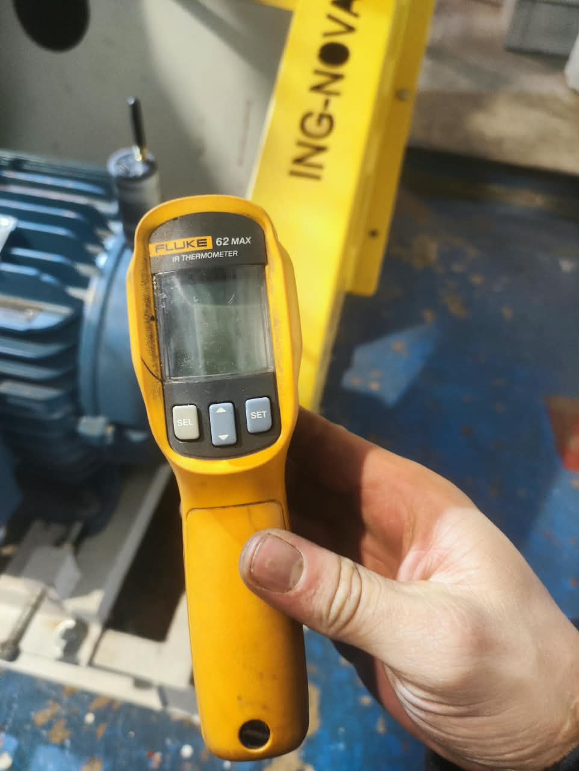
figuras/Fotos diseño final/adjuntos/1000099062.jpg
