DavidSPuentesc/SmartSense-Monitoring/figuras/Fotos diseño final/adjuntos/1000099066.jpg

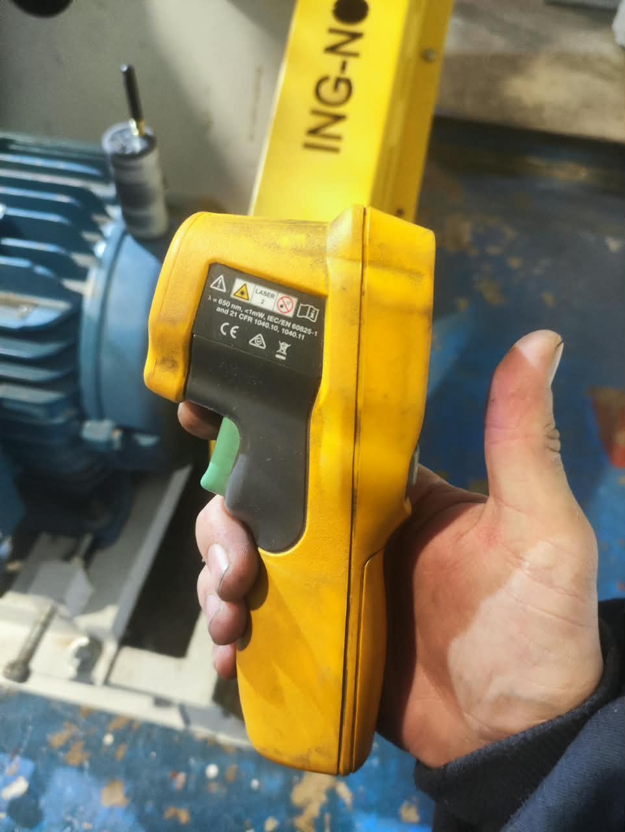
figuras/Fotos diseño final/adjuntos/1000099066.jpg
