DavidSPuentesc/SmartSense-Monitoring/figuras/Fotos diseño final/adjuntos/1000099070.jpg

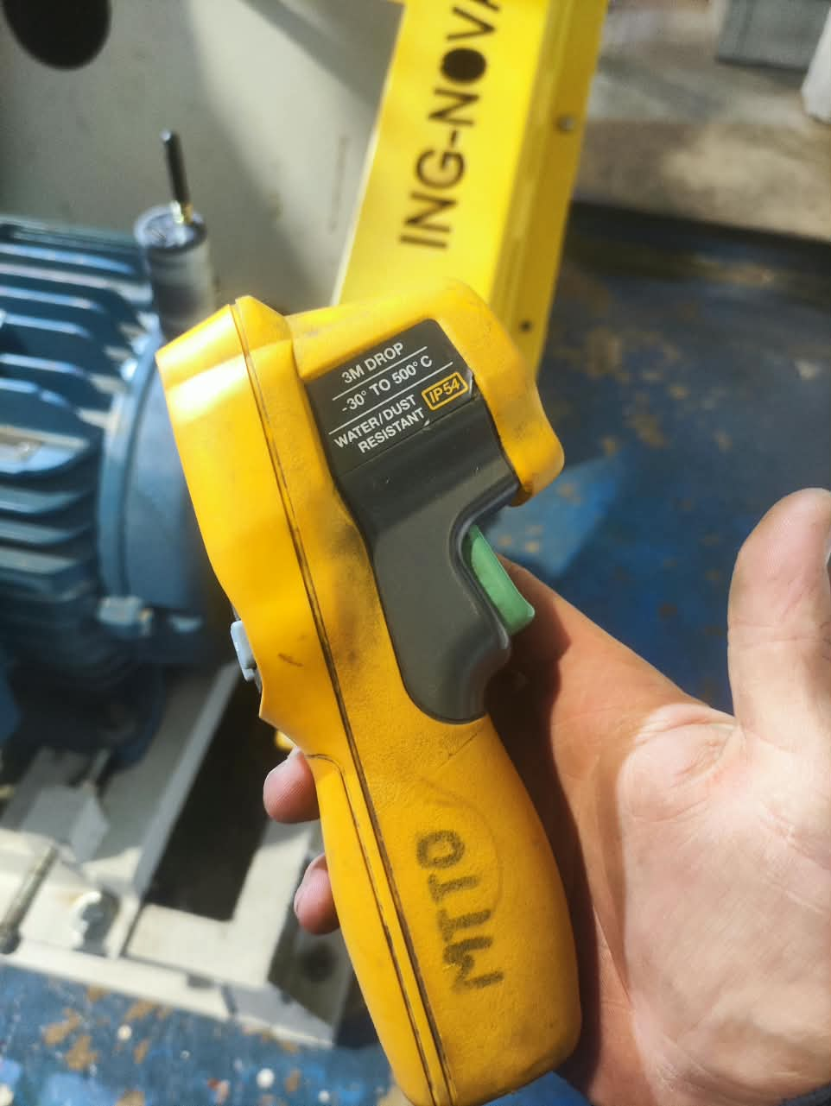
figuras/Fotos diseño final/adjuntos/1000099070.jpg
