DavidSPuentesc/SmartSense-Monitoring/figuras/Fotos diseño final/adjuntos/1000099072.jpg

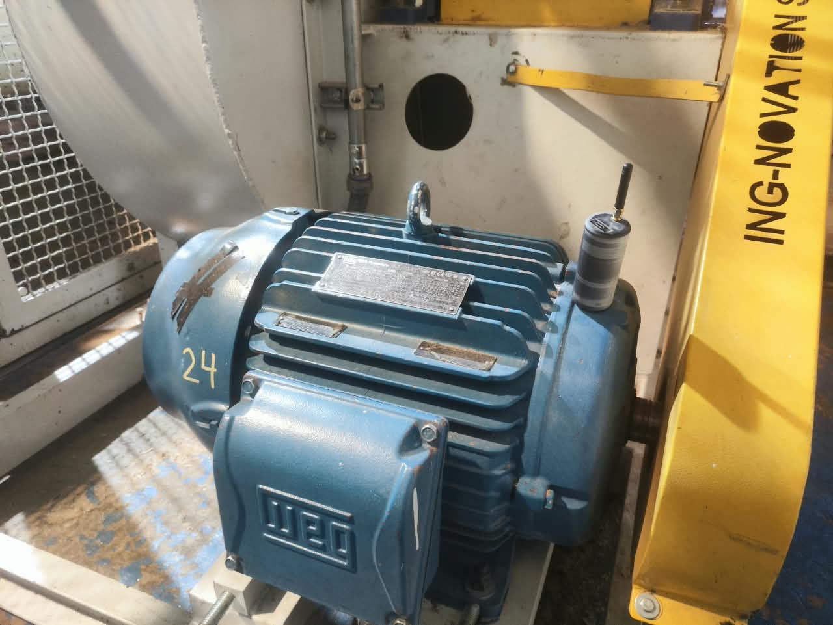
figuras/Fotos diseño final/adjuntos/1000099072.jpg
