DavidSPuentesc/SmartSense-Monitoring/figuras/Fotos diseño final/adjuntos/1000099074.jpg

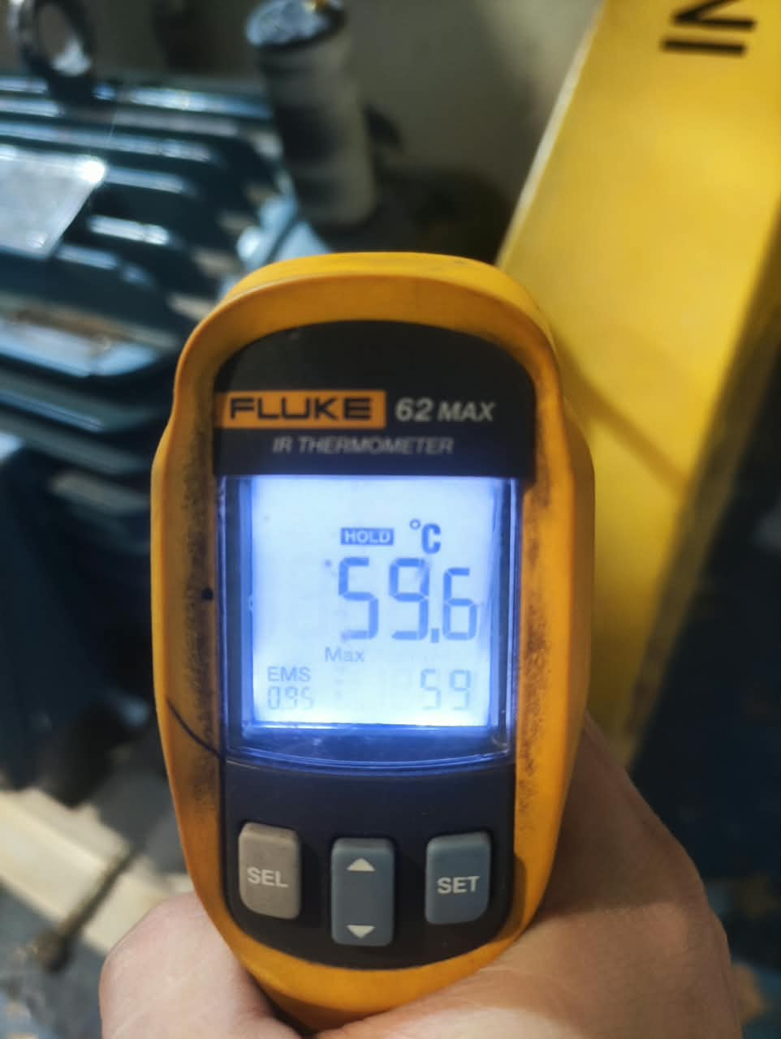
figuras/Fotos diseño final/adjuntos/1000099074.jpg
