DavidSPuentesc/SmartSense-Monitoring/figuras/val-cobertura.png

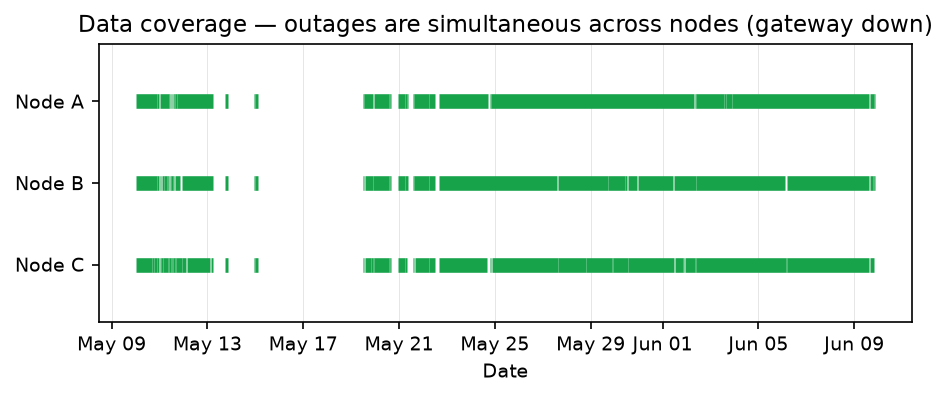
figuras/val-cobertura.png
