DavidSPuentesc/SmartSense-Monitoring/figuras/val-intervalos.png

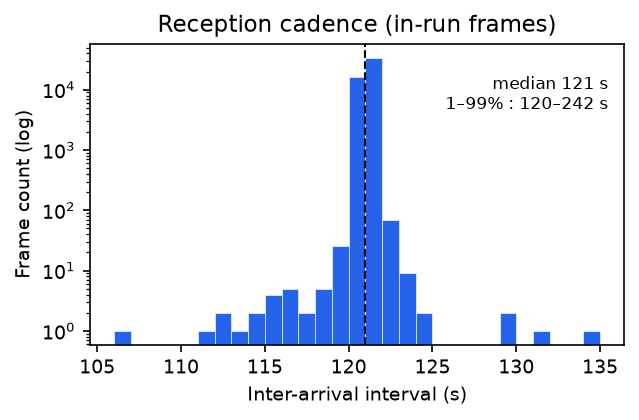
figuras/val-intervalos.png
