DavidSPuentesc/SmartSense-Monitoring/figuras/val-serie-evento.png

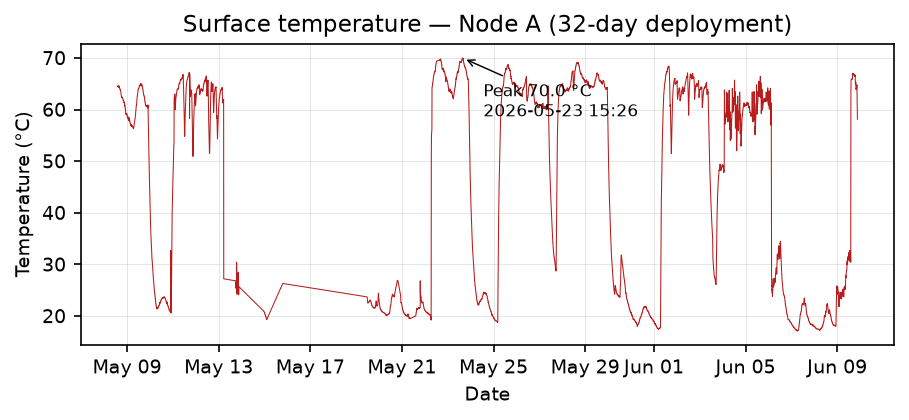
figuras/val-serie-evento.png
