DavidSPuentesc/SmartSense-Monitoring/sensores espnow lora/version con lora y pagina local/maestro_Lora_pantalla/data/embaladora.png

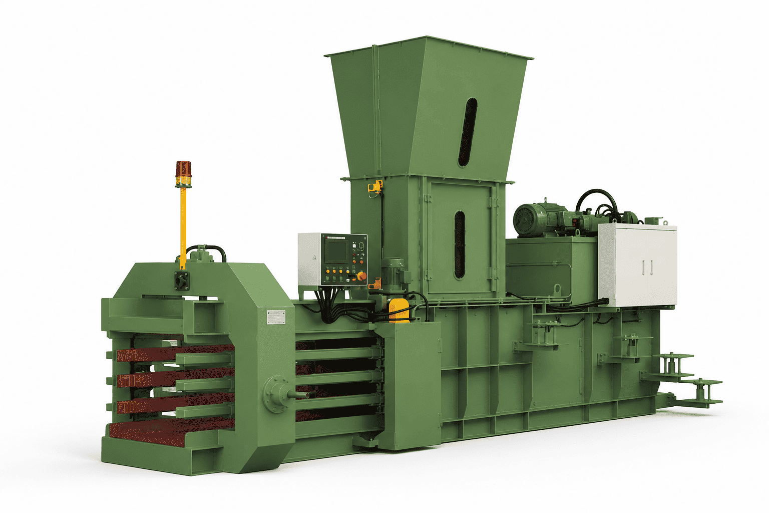
sensores espnow lora/version con lora y pagina local/maestro_Lora_pantalla/data/embaladora.png
