DavidSPuentesc/SmartSense-Monitoring/figuras/prueba-60min.png

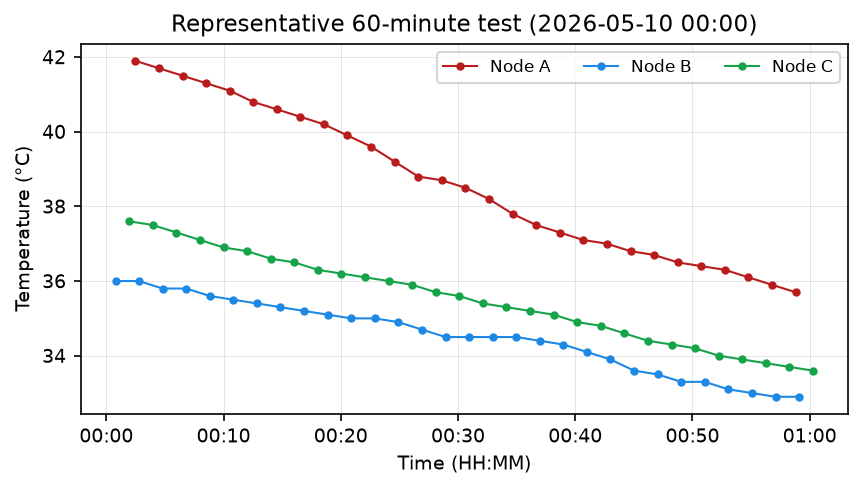
figuras/prueba-60min.png
