DavidSPuentesc/SmartSense-Monitoring/figuras/prueba-distancia.png

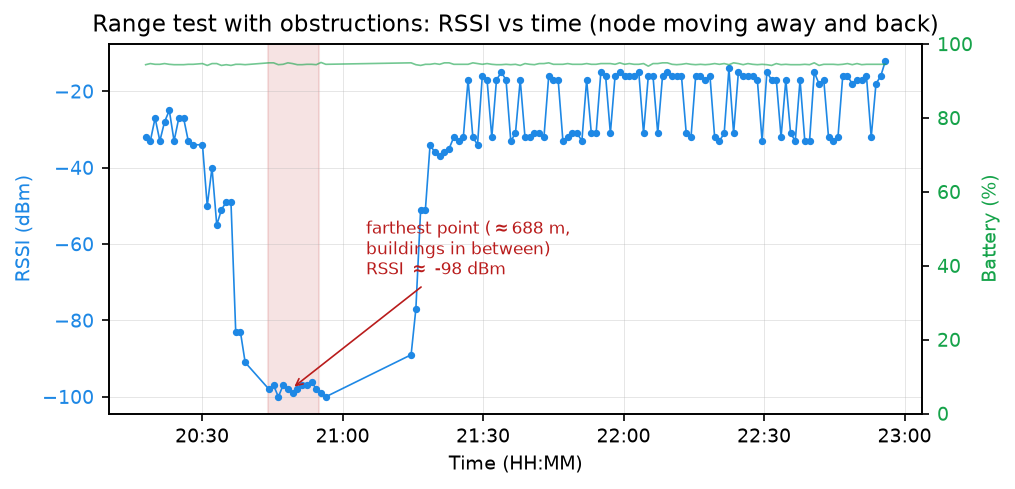
figuras/prueba-distancia.png
