DavidSPuentesc/SmartSense-Monitoring/figuras/autonomia-ciclo.pdf

## Perfil de consumo por ciclo: sueño + pico de transmisión (modelo)

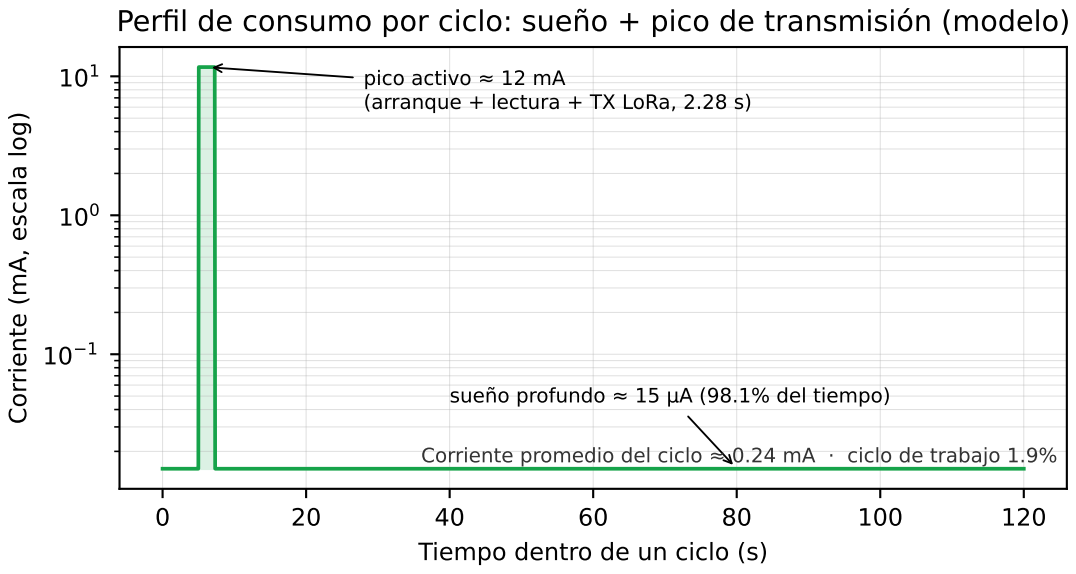
[picture p83: page 1]

pico activo ≈ 12 mA
(arranque + lectura + TX LoRa, 2.28 s)

Corriente (mA, escala log)

sueño profundo ≈ 15 µA (98.1% del tiempo)

Corriente promedio del ciclo ≈ 0.24 mA · ciclo de trabajo 1.9%

Tiempo dentro de un ciclo (s)
