DavidSPuentesc/SmartSense-Monitoring/figuras/autonomia-descarga.pdf

4.0

4.2

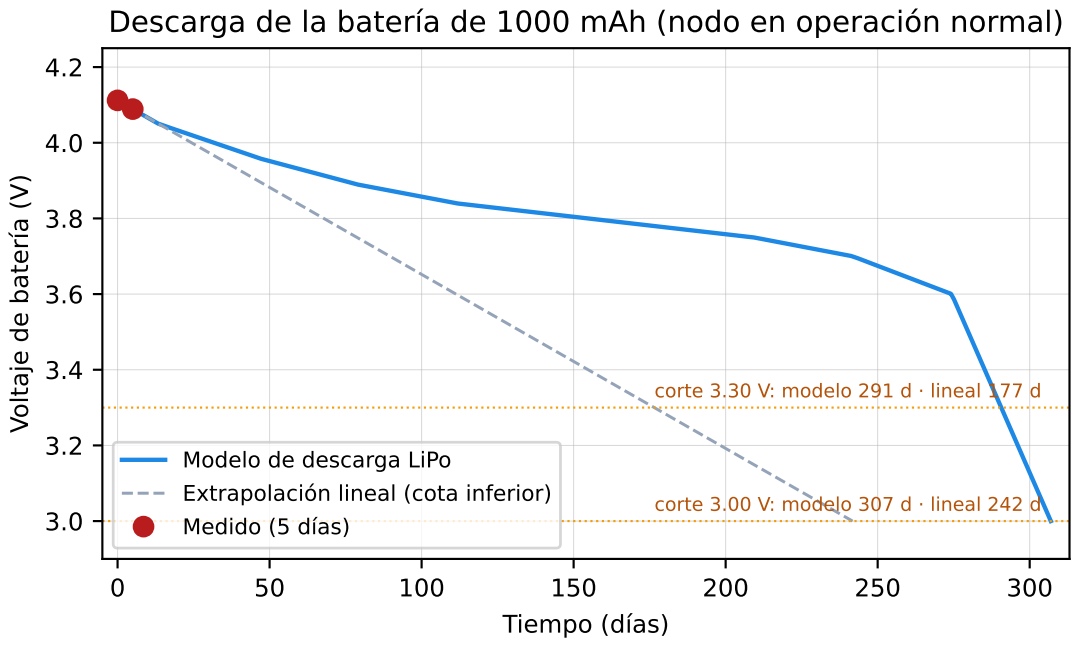
[picture p84: page 1]
Tiempo (días); corte 3.30 V: modelo 291 d · lineal 177

Descarga de la batería de 1000 mAh (nodo en operación normal)

Voltaje de batería (V)

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

Medido | (5 días)
