DavidSPuentesc/SmartSense-Monitoring/figuras/val-serie-evento.pdf

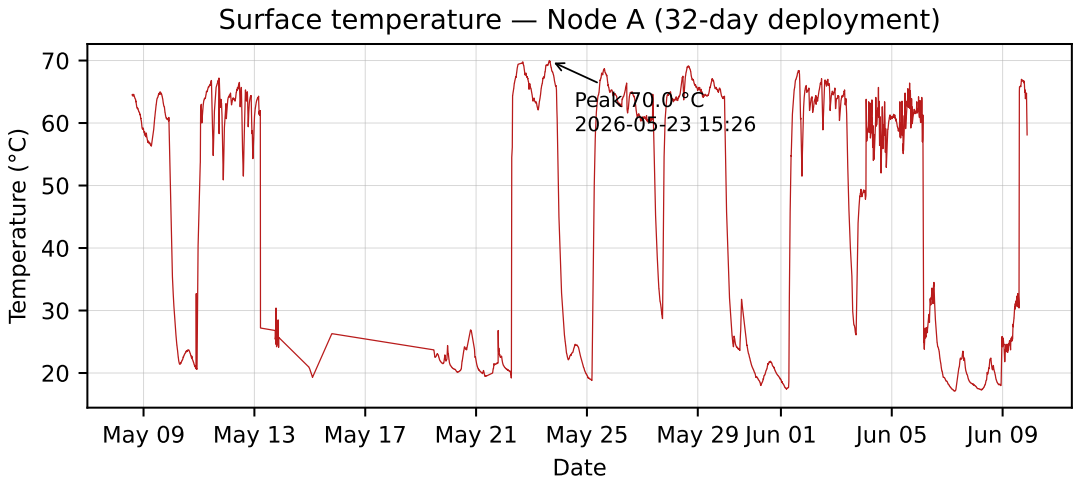
[picture p85: page 1]
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

Surface temperature — Node A (32-day deployment)

Peak 70.0 °C
2026-05-23 15:26
