DavidSPuentesc/SmartSense-Monitoring/hardware/kicad/gateway.kicad_sch

## KiCad design hardware/kicad/gateway.kicad_sch (2026-08-10)

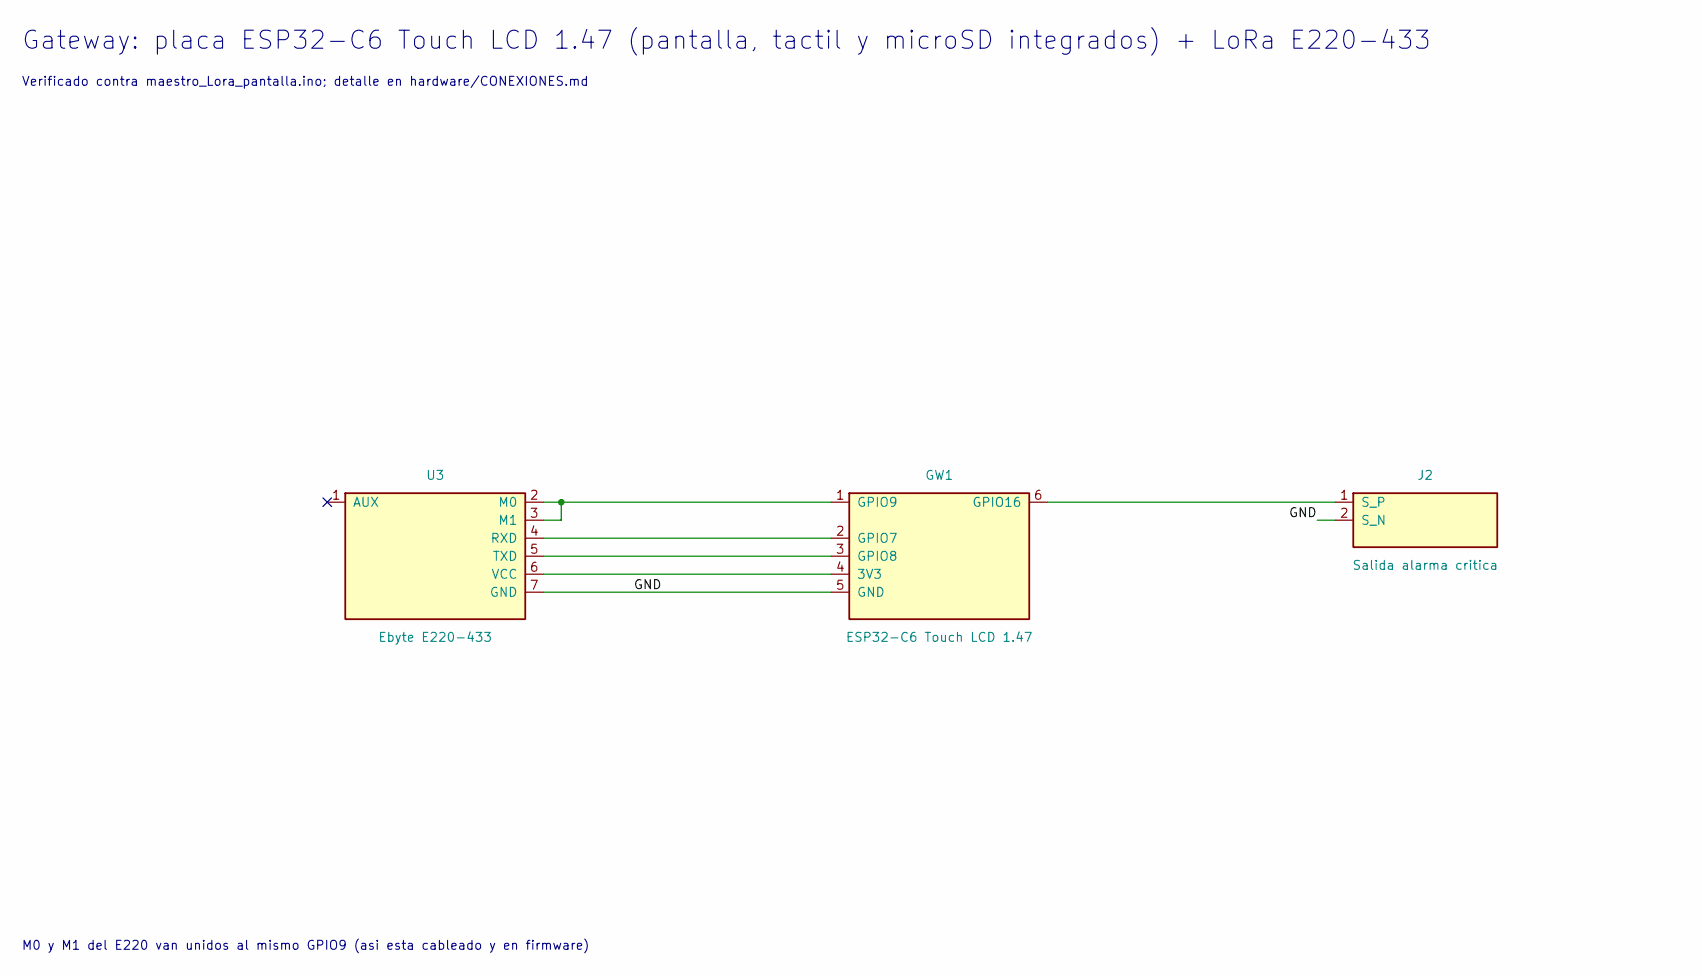
[picture p87: schematic gateway.kicad_sch]

Parts:
GW1: ESP32-C6 Touch LCD 1.47
J2: Salida alarma critica
U3: Ebyte E220-433

Connections:
GND: GW1.5 (GND), J2.2 (S_N), U3.7 (GND)
unnamed: GW1.1 (GPIO9), U3.2 (M0), U3.3 (M1)
unnamed: GW1.2 (GPIO7), U3.4 (RXD)
unnamed: GW1.3 (GPIO8), U3.5 (TXD)
unnamed: GW1.4 (3V3), U3.6 (VCC)
unnamed: GW1.6 (GPIO16), J2.1 (S_P)

Notes on the sheet:
Gateway: placa ESP32-C6 Touch LCD 1.47 (pantalla, tactil y microSD integrados) + LoRa E220-433
Verificado contra maestro_Lora_pantalla.ino; detalle en hardware/CONEXIONES.md
M0 y M1 del E220 van unidos al mismo GPIO9 (asi esta cableado y en firmware)
