DavidSPuentesc/SmartSense-Monitoring/hardware/kicad/nodo_sensor.kicad_sch

## KiCad design hardware/kicad/nodo_sensor.kicad_sch (2026-08-10)

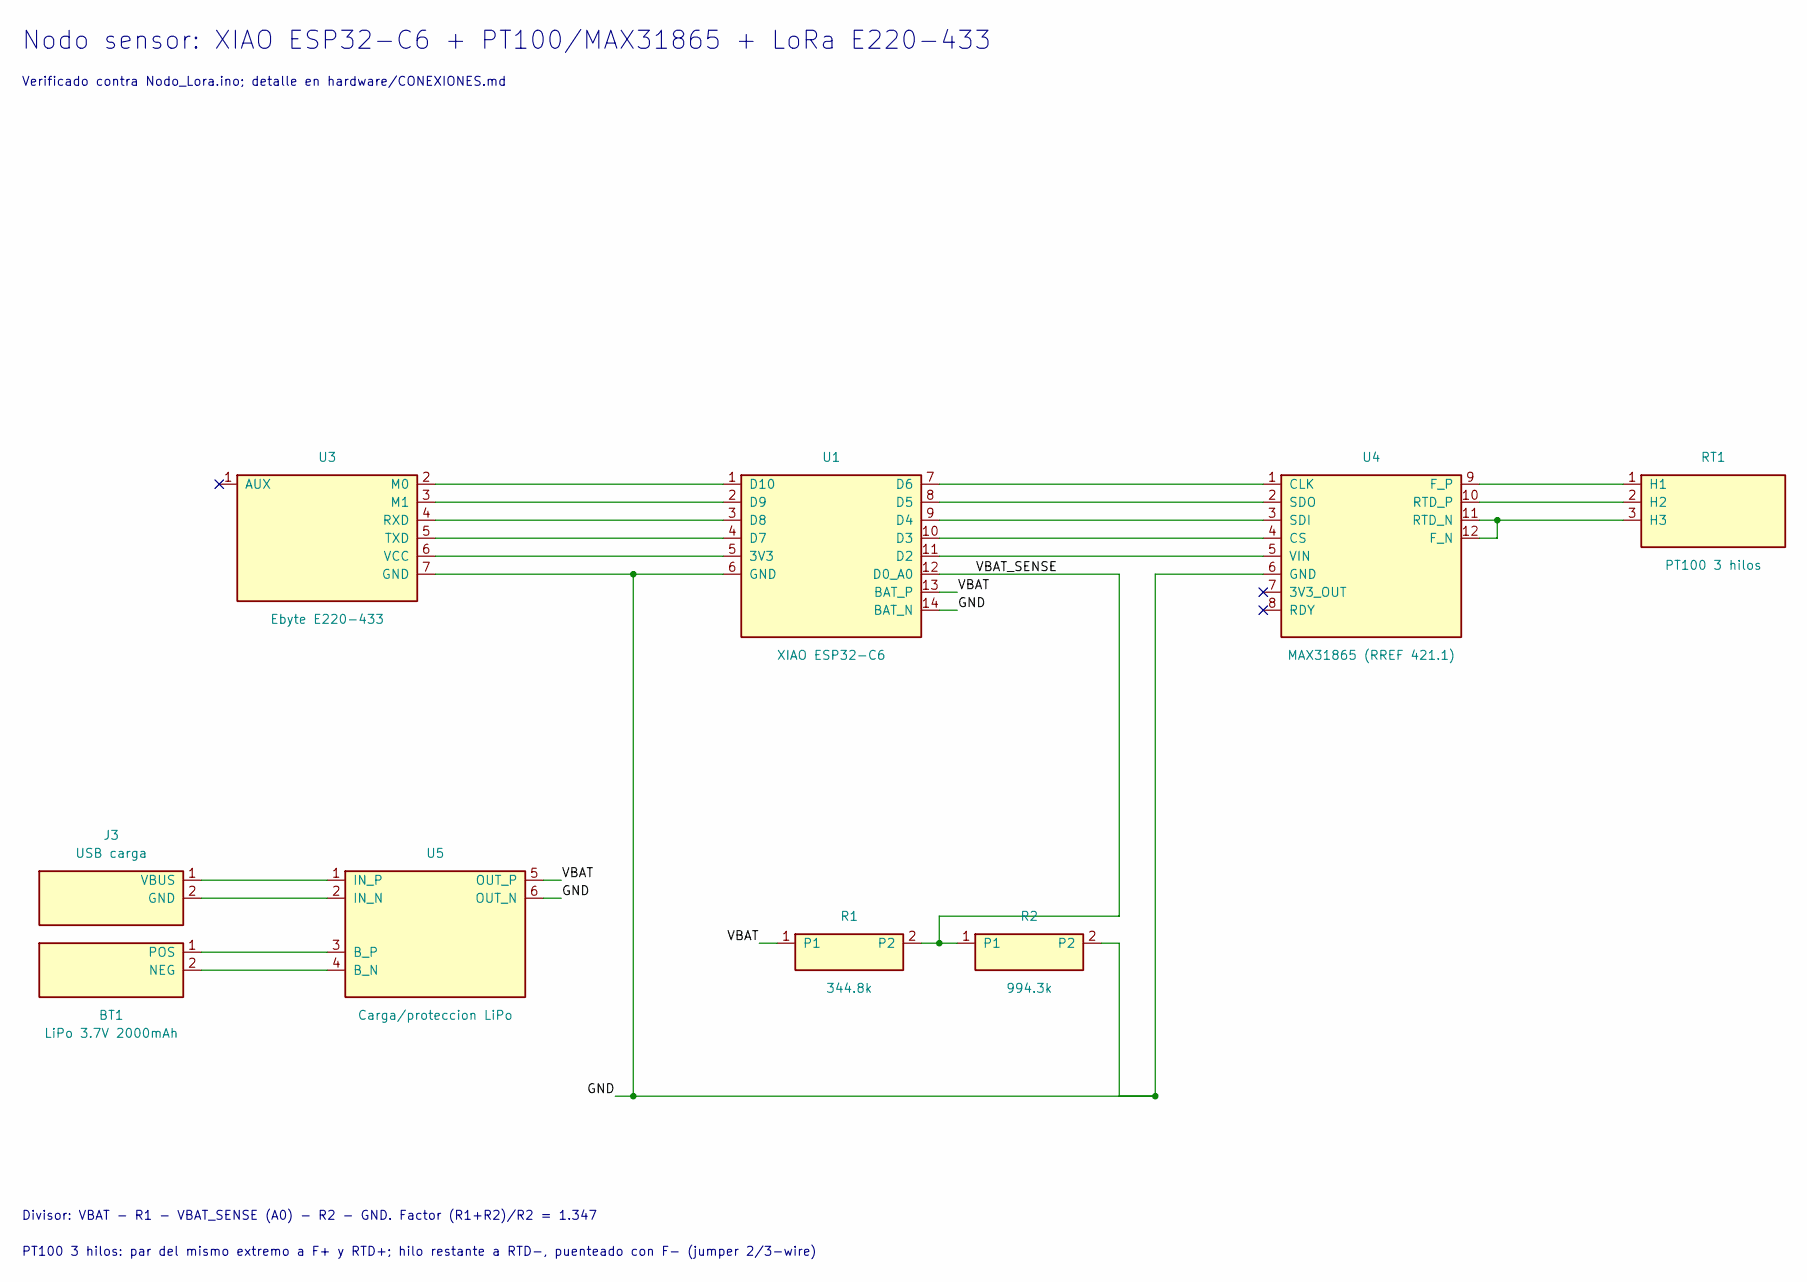
[picture p88: schematic nodo_sensor.kicad_sch]

Parts:
BT1: LiPo 3.7V 2000mAh
J3: USB carga
R1: 344.8k
R2: 994.3k
RT1: PT100 3 hilos
U1: XIAO ESP32-C6
U3: Ebyte E220-433
U4: MAX31865 (RREF 421.1)
U5: Carga/proteccion LiPo

Connections:
GND: R2.2, U1.6 (GND), U1.14 (BAT_N), U3.7 (GND), U4.6 (GND), U5.6 (OUT_N)
unnamed: BT1.1 (POS), U5.3 (B_P)
unnamed: BT1.2 (NEG), U5.4 (B_N)
unnamed: J3.1 (VBUS), U5.1 (IN_P)
unnamed: J3.2 (GND), U5.2 (IN_N)
unnamed: RT1.1 (H1), U4.9 (F_P)
unnamed: RT1.2 (H2), U4.10 (RTD_P)
unnamed: RT1.3 (H3), U4.11 (RTD_N), U4.12 (F_N)
unnamed: U1.1 (D10), U3.2 (M0)
unnamed: U1.2 (D9), U3.3 (M1)
unnamed: U1.3 (D8), U3.4 (RXD)
unnamed: U1.4 (D7), U3.5 (TXD)
unnamed: U1.5 (3V3), U3.6 (VCC)
unnamed: U1.7 (D6), U4.1 (CLK)
unnamed: U1.8 (D5), U4.2 (SDO)
unnamed: U1.9 (D4), U4.3 (SDI)
unnamed: U1.10 (D3), U4.4 (CS)
unnamed: U1.11 (D2), U4.5 (VIN)
VBAT: R1.1, U1.13 (BAT_P), U5.5 (OUT_P)
VBAT_SENSE: R1.2, R2.1, U1.12 (D0_A0)

Notes on the sheet:
Nodo sensor: XIAO ESP32-C6 + PT100/MAX31865 + LoRa E220-433
Verificado contra Nodo_Lora.ino; detalle en hardware/CONEXIONES.md
Divisor: VBAT - R1 - VBAT_SENSE (A0) - R2 - GND. Factor (R1+R2)/R2 = 1.347
PT100 3 hilos: par del mismo extremo a F+ y RTD+; hilo restante a RTD-, puenteado con F- (jumper 2/3-wire)
