DavidSPuentesc/SmartSense-Monitoring/sensores espnow lora/version con lora y pagina local/maestro_Lora_pantalla/SD_Card.cpp

#include "SD_Card.h"

uint16_t SDCard_Size = 0;
uint16_t Flash_Size = 0;

bool SD_Init() {
  pinMode(SD_CS, OUTPUT);
  digitalWrite(SD_CS, HIGH);

  pinMode(EXAMPLE_PIN_NUM_LCD_CS, OUTPUT);
  digitalWrite(EXAMPLE_PIN_NUM_LCD_CS, HIGH);

  if (SD.begin(SD_CS, SPI)) {
    printf("SD card initialization successful!\r\n");
  } else {
    printf("SD card initialization failed!\r\n");
  }

  uint8_t cardType = SD.cardType();
  if (cardType == CARD_NONE) {
    printf("No SD card attached\r\n");
    SDCard_Size = 0;
    return false;
  } else {
    printf("SD Card Type: ");
    if (cardType == CARD_MMC) {
      printf("MMC\r\n");
    } else if (cardType == CARD_SD) {
      printf("SDSC\r\n");
    } else if (cardType == CARD_SDHC) {
      printf("SDHC\r\n");
    } else {
      printf("UNKNOWN\r\n");
    }

    uint64_t totalBytes = SD.totalBytes();
    uint64_t usedBytes = SD.usedBytes();
    SDCard_Size = static_cast<uint16_t>(totalBytes / (1024ULL * 1024ULL));
    printf("Total space: %llu\n", totalBytes);
    printf("Used space: %llu\n", usedBytes);
    printf("Free space: %llu\n", totalBytes - usedBytes);
  }

  return true;
}

bool File_Search(const char* directory, const char* fileName)
{
  File Path = SD.open(directory);
  if (!Path) {
    printf("Path: <%s> does not exist\r\n", directory);
    return false;
  }

  File file = Path.openNextFile();
  while (file) {
    if (strcmp(file.name(), fileName) == 0) {
      if (strcmp(directory, "/") == 0) {
        printf("File '%s%s' found in root directory.\r\n", directory, fileName);
      } else {
        printf("File '%s/%s' found in root directory.\r\n", directory, fileName);
      }
      Path.close();
      return true;
    }
    file = Path.openNextFile();
  }

  if (strcmp(directory, "/") == 0) {
    printf("File '%s%s' not found in root directory.\r\n", directory, fileName);
  } else {
    printf("File '%s/%s' not found in root directory.\r\n", directory, fileName);
  }
  Path.close();
  return false;
}

uint16_t Folder_retrieval(const char* directory, const char* fileExtension, char File_Name[][100], uint16_t maxFiles)
{
  File Path = SD.open(directory);
  if (!Path) {
    printf("Path: <%s> does not exist\r\n", directory);
    return 0;
  }

  uint16_t fileCount = 0;
  char filePath[100];
  File file = Path.openNextFile();
  while (file && fileCount < maxFiles) {
    if (!file.isDirectory() && strstr(file.name(), fileExtension)) {
      strncpy(File_Name[fileCount], file.name(), sizeof(File_Name[fileCount]));
      File_Name[fileCount][sizeof(File_Name[fileCount]) - 1] = '\0';

      if (strcmp(directory, "/") == 0) {
        snprintf(filePath, sizeof(filePath), "%s%s", directory, file.name());
      } else {
        snprintf(filePath, sizeof(filePath), "%s/%s", directory, file.name());
      }
      printf("File found: %s\r\n", filePath);
      fileCount++;
    }
    file = Path.openNextFile();
  }
  Path.close();

  if (fileCount > 0) {
    printf("%d <%s> files were retrieved\r\n", fileCount, fileExtension);
    return fileCount;
  } else {
    printf("No files with extension '%s' found in directory: %s\r\n", fileExtension, directory);
    return 0;
  }
}

void remove_file_extension(char* file_name) {
  char* last_dot = strrchr(file_name, '.');
  if (last_dot != NULL) {
    *last_dot = '\0';
  }
}

void Flash_test()
{
  printf("/********** RAM Test**********/\r\n");
  uint32_t flashSize = ESP.getFlashChipSize();
  Flash_Size = static_cast<uint16_t>(flashSize / 1024UL / 1024UL);
  printf("Flash size: %d MB \r\n", flashSize / 1024UL / 1024UL);
  printf("/******* RAM Test Over********/\r\n\r\n");
}
