DavidSPuentesc/SmartSense-Monitoring/sensores espnow lora/version con lora y pagina local/maestro_Lora_pantalla/SD_Card.h

#pragma once

#include "Arduino.h"
#include <cstring>
#include "Display_ST7789.h"
#include "SD.h"
#include "FS.h"

#define SD_CS 4

extern uint16_t SDCard_Size;
extern uint16_t Flash_Size;

bool SD_Init();
void Flash_test();

bool File_Search(const char* directory, const char* fileName);
uint16_t Folder_retrieval(const char* directory, const char* fileExtension, char File_Name[][100], uint16_t maxFiles);
void remove_file_extension(char* file_name);
