DavidSPuentesc/SmartSense-Monitoring/sensores espnow lora/version con lora y pagina local/Modulos_Alarma/Panel_Pulsadores_LoRa/secrets.example.h

#pragma once
// Copiar este archivo como secrets.h y completar con las credenciales reales.
// secrets.h está en .gitignore y nunca se versiona.
static constexpr const char* OTA_WIFI_SSID = "TU_SSID_OTA";
static constexpr const char* OTA_WIFI_PASS = "TU_PASSWORD_OTA";
static constexpr const char* OTA_UPDATE_PASSWORD = "TU_PASSWORD_ACTUALIZACION";
