DavidSPuentesc/SmartSense-Monitoring/sensores espnow lora/version con lora y pagina local/maestro_Lora_pantalla/secrets.example.h

#pragma once
// Copiar este archivo como secrets.h y completar con la clave real del Access Point.
// secrets.h está en .gitignore y nunca se versiona. Mínimo 8 caracteres para WPA2.
const char* AP_PASS = "CLAVE_DEL_AP";
